Guiimartinho/gnss-bike-computer/hardware_gnssbike/04-pcb-e-caixa.md

# Placa e caixa

O contorno, a espessura, as camadas, onde cada bloco fica e onde nada pode
ficar. Fecha o que as [folhas do esquemático](01-esquematico.md) deixam em
aberto por natureza: um esquemático diz o que se liga a quê, e é o layout
que decide se a antena
enxerga o céu, se o harmônico da flash cai dentro de L1 e se a placa cabe na
caixa. As posições vêm da tabela de zonas de [`docs/14`](../docs/14-hardware-placa-nova.md#placa-de-circuito-impresso)
e, até 2026-09-26, do desenho do conceito da caixa (`tools/docs/case_drawing.py`,
retirado nesse dia: a proposta medida em [`caixa/`](caixa/README.md) o substitui).
Conta feita aqui vem marcada como **conta**; número de ficha ou de desenho
vem marcado como **ficha** ou **desenho**.

**Nesta página:** [O contorno](#o-contorno) · [Orçamento de área](#orçamento-de-área) · [Camadas](#camadas) · [Posicionamento](#posicionamento) · [Zonas proibidas](#zonas-proibidas) · [As duas antenas](#as-duas-antenas) · [Montagem](#montagem) · [O que só a bancada decide](#o-que-só-a-bancada-decide)

> [!WARNING]
> **Não existe placa física e nada foi fabricado nem medido.** Não há
> gerber, não há pilha de camadas de fabricante e ninguém encostou uma ponta
> de prova em nada. O que **passou a existir** desde 2026-09-23 é o projeto
> em KiCad, em [`cad/`](cad/): as 116 peças posicionadas, os planos de terra e
> parte das trilhas, com a verificação de regras do KiCad e o
> [dry-run das regras das fichas](09-dry-run-da-pcb.md).
>
> Esta página continua sendo **a planta**: os retângulos de zona daqui são o
> que o layout deve respeitar, e onde a placa de `cad/` diverge deles, a
> divergência está escrita e medida. Quando os dois discordarem, quem manda
> é o número medido no arquivo, não o retângulo desta tabela.

> [!CAUTION]
> **A placa é 34 × 90 mm desde 2026-09-24 e 34 × 95 desde 2026-09-26 (as
> três teclas espalhadas na largura do display, no passo de 13,4 mm, só
> passam pela área da antena do módulo de rádio com ele 5 mm mais baixo), e
> as tabelas de orçamento de área, de sobreposições e de posicionamento
> abaixo ainda são as de 55 × 97.** Elas
> precisam ser refeitas a partir dos retângulos novos, que estão em
> [`cad/make_dxf.py`](cad/make_dxf.py) (`ZONES`) e agora são **derivados de
> `W` e `H`**, não escritos um a um. Enquanto isso, quando esta página e o CAD
> discordarem, **quem vale é o CAD**.
>
> Uma tentativa anterior de 50 × 86 mm partia da largura do display e da
> altura da caixa. Estava errada pela raiz: **a placa não se mede pela
> caixa.** O tamanho de agora sai das regras das fichas, e a conta está em
> [De onde saem os 34 × 90](#de-onde-saem-os-34--90).
>
> A caixa do conceito continuava sendo a de 62 × 104 (o desenho dela foi
> retirado em 2026-09-26; a proposta medida, em [`caixa/`](caixa/README.md),
> tem 62 × 106 × 17), e **isso não é pendência da placa**: a caixa
> tem o tamanho que o display, a bateria e a mão pedem, e a placa encolher não
> muda nenhum dos três.

## O contorno

> [!IMPORTANT]
> **A placa não é dimensionada pela caixa, e a caixa não é dimensionada pela
> placa.** As duas são independentes: o tamanho da placa sai do **circuito**
> — peças, roteamento e as distâncias que as fichas impõem — e o da caixa sai
> do display, da bateria e da ergonomia. Uma placa menor não encolhe a caixa;
> ela apenas ocupa menos espaço dentro dela. Esta página já derivou uma da
> outra e estava errada.

| Item | Medida | Origem |
|---|---|---|
| PCB | **34 × 95 mm**, espessura de 0,8 mm | derivado das regras em [`cad/make_dxf.py`](cad/make_dxf.py) (`W`, `H`); os 5 mm além dos 90 de 2026-09-24 são das teclas no passo de 13,4 (abaixo) |
| Raio de canto da placa | **3 mm no desenho, 4 mm em [14](../docs/14-hardware-placa-nova.md#placa-de-circuito-impresso)** | as duas fontes discordam, ver abaixo |
| Caixa | conceito: 62 × 104 × 19 mm, mais 3 mm do engate de quarto de volta; proposta de 2026-09-26: **62 × 106 × 17** ([abaixo](#a-placa-de-hoje-dentro-da-caixa-do-conceito)) | o desenho do conceito (`tools/docs/case_drawing.py`, retirado em 2026-09-26); [`caixa/make_caixa.py`](caixa/make_caixa.py) (`W_C, H_C, T_C`) |
| Raio de canto da caixa | 7 mm | idem (`R`) |
| Placa da V3, para comparar | 52,35 × 77,47 mm | [13](../docs/13-placa-nova.md#o-que-cabe-numa-caixa-pequena) |

### De onde saem os 34 × 90

Uma regra domina: a **7.2** da ficha do ME54BS13 pede **50 mm entre dois
módulos de rádio** na mesma placa, e esta tem dois — o próprio ME54BS13 e o
MAX-F10S. Com o módulo deitado num canto (contorno de 17,0 × 13,5) e o
receptor no oposto (10,4 × 10,6, abaixo dos 8 mm da zona da antena), os 50 mm
entre os dois contornos fixam o lado longo. Varrendo cada milímetro inteiro
que ainda cumpre a regra **e** ainda cabe a fila de três teclas na largura
(3 × 10,2 mm mais 0,8 de margem de cada lado):

| Contorno | Área | Módulos a |
|---|---|---|
| 32 × 89 | 2.848 mm² | 50,8 mm |
| 33 × 89 | 2.937 mm² | 50,9 mm |
| **34 × 90** | **3.060 mm²** | **51,9 mm** |
| 44 × 86 | 3.784 mm² | 50,2 mm, com as teclas ainda na borda de baixo |

Ficou **34 × 90**. Os 2 mm além dos 88 que a regra sozinha permitiria não são
folga: a 88 o receptor tinha de encostar na borda esquerda para alcançar os
50 mm, e aí os pinos de 1V8 dele, que saem desse lado, ficavam com 1,2 mm de
placa para pôr um capacitor de desacoplamento que a ficha quer a 2 mm.

São **3.060 mm² contra os 5.335 mm² dos 55 × 97 que estavam escritos à mão —
43 % menos placa** — e a ocupação dos contornos das peças sobe de 28 % para
48 %.

**E depois 34 × 95** (2026-09-26). O dono quis as três teclas espalhadas na
largura do display, exatamente sob as capas da caixa, e não juntas no canto
esquerdo: no passo de 13,4 mm, o maior que a margem de 0,8 mm da borda
deixa, a terceira chave fica em x = 30,4, dentro dos 5 mm que a ficha do
ME54BS13 (7.4) quer livres em volta da área da antena do módulo. A área
começa em y = H − 22: com H = 95 ela desce 5 mm junto com o módulo, e a fila
de teclas em y = 66 passa a 5,0 mm dela. São 3.230 mm² (`GNSSBIKE_H` em
`make_dxf.py` troca a altura).

> [!IMPORTANT]
> **O raio de canto da placa não bate entre as duas fontes.** O desenho do
> conceito traçava a placa com **3 mm** de raio — `xv.rect(3.5, 3.5, W - 7, H - 7, 3, …)`,
> linha 339 do `case_drawing.py` retirado em 2026-09-26; o número vive em
> `cad/make_dxf.RADIUS_DRAWING` —, e [14](../docs/14-hardware-placa-nova.md#placa-de-circuito-impresso)
> escreve "cantos com raio de 4 mm". Um milímetro num canto não muda nada
> elétrico, mas muda o contorno que vai para o fabricante e a folga contra
> a parede de 7 mm de raio da caixa. **Qual dos dois vale ainda não foi
> decidido**, e esta página não escolhe por ninguém: registra os dois.

**Sistema de coordenadas** desta página, o mesmo de [14](../docs/14-hardware-placa-nova.md#placa-de-circuito-impresso):
origem no canto de cima à esquerda da **placa**, vista pela frente, x para a
direita (0 a 34 mm) e y para baixo (0 a 90 mm). **Não há mais conversão para
as coordenadas da caixa**: com a placa dimensionada pelo circuito e a caixa
pelo que ela guarda, onde uma fica dentro da outra é decisão do arranjo
mecânico, que não existe.

> [!IMPORTANT]
> **A folga entre a placa e a caixa não bate com o texto de [14](../docs/14-hardware-placa-nova.md#placa-de-circuito-impresso).**
> Lá está escrito "paredes de cerca de 2 mm e folga de 0,5 mm", que somam
> 2,5 mm por lado e dariam uma placa de 57 × 99 mm. O desenho põe a placa
> com 3,5 mm de recuo, o que com parede de 2 mm deixa **1,5 mm de folga
> mecânica por lado**, não 0,5 mm (**conta**: 3,5 − 2,0). Um milímetro por
> lado é a diferença entre apertar e sobrar; **qual dos dois vale é decisão
> do projeto mecânico, que não existe.** Esta página segue o desenho, que é
> executável, e registra a divergência.

## Orçamento de área

A placa tem **5.335 mm²** (**conta**: 55 × 97). A pergunta é se o que
precisa entrar cabe, e a resposta tem duas partes: a área de planta que as
zonas consomem, e a área que fica com **restrição de altura** por causa do
display na frente e da bateria atrás.

### O que cada zona consome em planta

Áreas calculadas a partir dos retângulos de [14](../docs/14-hardware-placa-nova.md#placa-de-circuito-impresso).
Todas são **conta**, menos a linha marcada como **falta**, que não tem
retângulo em documento nenhum.

| Zona | Retângulo (x, y em mm) | Lados | Área (mm²) | % dos 5.335 |
|---|---|---|---|---|
| Antena GNSS (área livre) | 0–55, 0–8 | 55 × 8 | 440,0 | 8,2 % |
| GNSS (MAX-F10S e blindagem) | 20–35, 2–16 | 15 × 14 | 210,0 | 3,9 % |
| LED RGB | 50–53, 0–3 | 3 × 3 | 9,0 | 0,2 % |
| IMU e magnetômetro | 8–15, 20–23 | 7 × 3 | 21,0 | 0,4 % |
| FPC do display | 3,7–7,1, 29,5–39,5 | 3,4 × 10 | 34,0 | 0,6 % |
| Conector do filme de luz (Molex 5034800440) | **sem retângulo em [14](../docs/14-hardware-placa-nova.md#placa-de-circuito-impresso)** | — | **falta** | — |
| Buzzer | 10,5–21,5, 46,5–55,5 | 11 × 9 | 99,0 | 1,9 % |
| Energia (nPM1300, AEM10900, MAX17262, indutores, conectores) | 16–38, 67–90 | 22 × 23 | 506,0 | 9,5 % |
| Armazenamento (flash NOR) | 0–14, 67–83 | 14 × 16 | 224,0 | 4,2 % |
| Barômetro | 4,5–8, 83–86,5 | 3,5 × 3,5 | 12,3 | 0,2 % |
| ME54BS13 **mais a zona proibida da sua antena** | 37,2–54,2, 58,7–71,4 unido a 49,5–55, 54,6–75,4 | ver a conta abaixo | 270,6 | 5,1 % |
| Botões | 8–47, 88–95 | 39 × 7 | 273,0 | 5,1 % |
| USB-C | 23–32, 94–97 | 9 × 3 | 27,0 | 0,5 % |
| Luz ambiente (OPT3001) | 0,4–2,4, 88–90 | 2 × 2 | 4,0 | 0,1 % |
| **Soma bruta** | | | **2.129,9** | **39,9 %** |
| Sobreposições contadas duas vezes | | | −102,5 | −1,9 % |
| **Soma líquida** | | | **2.027,4** | **38,0 %** |

O módulo entra com a **zona proibida**, não só com o retângulo dele: é a
zona que proíbe cobre, e é ela que o layout tem de respeitar
([Zonas proibidas](#zonas-proibidas)). Ela vai da antena até a borda da
placa e sobra 4,4 mm para cima e para baixo do módulo, e por isso a área é
a **união** dos dois retângulos (**conta**):

```
módulo:         x 37,2 a 54,2, y 58,7 a 71,4 = 17,0 × 12,7 = 215,9 mm²
zona proibida:  x 49,5 a 55,0, y 54,6 a 75,4 =  5,5 × 20,8 = 114,4 mm²
comum aos dois: x 49,5 a 54,2, y 58,7 a 71,4 =  4,7 × 12,7 =  59,7 mm²
união = 215,9 + 114,4 − 59,7 = 270,6 mm²       (270,6 ÷ 5.335 = 5,1 %)
```

> [!NOTE]
> **Estes números são novos.** Até 2026-09-23 este documento contava o
> módulo como o **Fanstel BM20C**, de 10,0 × 16,2 mm, no canto de baixo à
> direita (x 45–55, y 71,5–87,7), com a zona proibida em x 40–55, y 82–91:
> união de **240,0 mm², 4,5 %**. O módulo montado é o **MinewSemi
> ME54BS13**, maior (16,5 × 12,0 × 2,4 mm) e deitado acima das teclas, e
> todas as contas desta seção foram refeitas a partir dos retângulos novos.

A soma bruta fecha (**conta**): 440,0 + 210,0 + 9,0 + 21,0 + 34,0 + 99,0 +
506,0 + 224,0 + 12,3 + 270,6 + 273,0 + 27,0 + 4,0 = **2.129,9 mm²**.

As três sobreposições (**conta**) são exatamente os três pontos que o
layout terá de resolver:

| Sobreposição | Retângulo comum | Área |
|---|---|---|
| GNSS dentro da área livre da antena | 20–35, 2–8 | 15 × 6 = 90 mm² |
| LED RGB dentro da área livre da antena | 50–53, 0–3 | 3 × 3 = 9 mm² |
| Zona do **ME54BS13** dentro da zona de energia | 37,2–38, 67–71,4 | 0,8 × 4,4 = **3,5 mm²** |

A terceira sai de cruzar a zona do módulo com a zona de energia
(**conta**):

```
zona de energia: x 16   a 38,0, y 67,0 a 90,0
zona do módulo:  x 37,2 a 54,2, y 58,7 a 71,4
em x: de max(37,2; 16) = 37,2 a min(54,2; 38,0) = 38,0, ou seja 0,8 mm
em y: de max(58,7; 67,0) = 67,0 a min(71,4; 90,0) = 71,4, ou seja 4,4 mm
área = 0,8 × 4,4 = 3,52 mm², 3,5 mm² arredondado
```

Total das sobreposições: 90 + 9 + 3,5 = **102,5 mm²**.

A terceira sobreposição **trocou de lugar com o módulo**. Com o BM20C no
canto de baixo à direita, quem invadia a zona proibida era a faixa dos
botões, em 21 mm². Com o ME54BS13 deitado acima das teclas, a faixa dos
botões (y 88 a 95) e a zona proibida (y 54,6 a 75,4) **não se tocam mais**;
em troca, o canto de baixo à esquerda do módulo entra na zona de energia.
Os 3,5 mm² são pouco em área e **muito em significado**: é um conversor
chaveado encostando no módulo de rádio
([A zona do ME54BS13](#a-zona-do-me54bs13-em-detalhe)).

**Sobram 3.307,6 mm², 62,0 % da placa** (**conta**: 5.335 − 2.027,4), para
os passivos espalhados, as vias, os furos M2, os pontos de teste, o
footprint Tag-Connect TC2030-NL, os dois pads do console (`uart20`, `TP201` e
`TP202` de [06](06-conectores-e-pontos-de-teste.md#pontos-de-teste)) e as trilhas. **Pela planta,
fecha com folga.**

> [!NOTE]
> Os 6 módulos solares de 23 × 8 mm **não consomem área de placa**: ficam na
> face inclinada da caixa e nos dois chanfros de 45°, virados para o sol,
> enquanto a placa fica dentro, atrás do display. São três orientações
> diferentes, e é isso que faz a colheita render com o guidão apontando para
> qualquer lado — uma placa plana só tem uma orientação, então **soldar os
> módulos na placa não é uma opção**.
>
> Eles chegam por **um conector de 4 vias em pé na borda esquerda, na face
> de trás**, o `J103` (na borda direita da frente até 2026-09-26, quando o
> dry run da caixa o mediu a 0,05 mm da tampa), que consome 10,5 mm dessa
> borda e 8 mm para dentro. Antes eram três pares de
> pads de mola, e a área deles era o número que faltava aqui; agora está
> medida e entra na soma. Ver [Como os painéis chegam à
> placa](#como-os-painéis-chegam-à-placa).
>
> A antena GNSS continua sendo um elemento fora da placa quando se escolhe o
> caminho do `J302` (u.FL); pelo `JP301` também dá para montar a antena de
> chip soldada na borda de cima. **A área dos contatos da antena continua
> sem dimensionar.**

> [!IMPORTANT]
> **O conector do filme de luz não tem zona nem área.**
> [14](../docs/14-hardware-placa-nova.md#placa-de-circuito-impresso) manda
> pôr o Molex 5034800440, de 4 vias e passo de 0,5 mm, "ao lado" do FPC do
> display na borda esquerda, mas a tabela de zonas de lá **não lhe dá
> retângulo**, e a ficha dele não está resumida em nenhum documento deste
> repositório: não há como calcular a área aqui sem inventar uma medida.
> Ele só existe na montagem com a Sharp
> ([05](05-materiais.md#folha-4--display)), o que não o torna opcional no
> layout, porque a placa tem de aceitar as duas montagens. **É um número
> que falta**, e a soma acima está subestimada por ele.

### As duas sombras: display e bateria

O display fica sobre a face da frente e a bateria, sob a face de trás. Não
competem por área de planta, mas **limitam a altura** das peças embaixo
delas: até 3,0 mm sob o display (2,6 até 2026-09-26: o receptor MAX-F10S
tem 2,7 no máximo, e a caixa desceu a placa 0,4 mm em vez de tirar o
receptor de junto da antena) e até 1,2 mm sob a bateria
([14](../docs/14-hardware-placa-nova.md#placa-de-circuito-impresso)).

> [!IMPORTANT]
> **A posição do display e da célula sobre esta placa é uma PROPOSTA de
> 2026-09-26, não uma decisão.** A caixa desenhada de manhã (o conceito
> de `tools/docs/case_drawing.py`, retirado à tarde) era a da
> placa antiga, de 55 × 97, e nenhum arquivo dizia onde as duas peças caem
> sobre a placa de 34 × 90 — a tabela abaixo, até essa data, ainda trazia
> retângulos de 47 mm de largura numa placa de 34. Sem os retângulos a
> regra `ME2` do dry-run passava **sem medir peça nenhuma**; agora eles
> estão em `cad/make_dxf.py` (`SOMBRA_DISPLAY_JDI_MAX_3-0MM` e
> `SOMBRA_BATERIA_MAX_1-2MM`), a regra mede, e o que ela mede está abaixo.
> A caixa de [`caixa/make_caixa.py`](caixa/make_caixa.py) lê os mesmos
> retângulos (`make_dxf.DISPLAY_Y1`), e o dry run dela
> ([`caixa/dry_run_caixa.py`](caixa/dry_run_caixa.py)) mede a pilha inteira.

O que fixa cada retângulo, na placa de 34 × 95:

- **O display** LPM027M128C tem 40,08 × 61,8 mm: é **mais largo que a
  placa**, logo cobre a largura inteira. Em y, ele tem de acabar **acima
  das teclas**, que ficam em y = 66 com corpo de 3,5 mm (uma tecla debaixo
  do vidro não se aperta) — e acima do **furo da capa** de cada tecla na
  tampa, de 5,6 mm, que desce até y = 63,2: fim em **62,9**, começo 61,8
  acima, em **1,1**. Era 64,5 até o dry run da caixa de 2026-09-26, que
  mediu o furo entrando 1,3 mm no vidro colado; as teclas não podem descer
  (o SWD, o conector da célula e o USB-C ocupam y 67,75 a 85,44 até 0,4
  mm), e o dono quer as capas exatamente sobre as chaves.
- **A célula** de 36 × 60 × 7 também cobre a largura. A bolsa é metal, e
  metal não pode ficar atrás da antena GNSS (y até 9,88) nem no canto da
  área da antena do módulo (x ≥ 29,3, y ≥ 68,0; ficha do ME54BS13, 7.4).
  Entre as duas antenas há **58,1 mm**, e a célula tem **60**: começando
  logo abaixo da antena GNSS, em **9,9**, ela acaba em **69,9**, 1,9 mm
  dentro do canto da antena do módulo.

| Sombra | Retângulo (coordenadas da placa) | Área (mm²) | % dos 3.230 | Altura permitida |
|---|---|---|---|---|
| Display JDI LPM027M128C (contorno 40,08 × 61,8) | 0–34, 1,1–62,9 | 2.101,2 | 65,1 % | 3,0 mm |
| Bateria LiPo (36 × 60), na face de trás | 0–34, 9,9–69,9 | 2.040,0 | 63,2 % | 1,2 mm |

Contas de conferência (**conta**; a placa tem 34 × 95 = 3.230 mm²):

```
interseção das duas sombras = 34 mm × (62,9 − 9,9) = 34 × 53,0 = 1.802,0 mm²  (55,8 %)
união = 2.101,2 + 2.040,0 − 1.802,0 = 2.339,2 mm²  (72,4 %)
área sem restrição de altura dos dois lados = 3.230 − 2.339,2 = 890,8 mm²  (27,6 %)
```

**56 % da placa tem teto de 3,0 mm na frente e de 1,2 mm atrás ao mesmo
tempo**, e pouco mais de um quarto está livre das duas — a faixa de cima (a
antena GNSS e o receptor) e a de baixo (USB-C, módulo de rádio e teclas). O
dry-run de 2026-09-26 mediu as peças contra esses tetos (`ME2`), com as
alturas das fichas, e **cinco não cabiam**; no mesmo dia, com a caixa
desenhada e medida, todas saíram da sombra ou o teto subiu:

| Peça | Altura | Onde estava | Teto | O que foi feito |
|---|---|---|---|---|
| `J102`, conector da célula | 4,25 mm (GH) | face de trás, (4,0; 62,0) | 1,2 mm | virou o **JST SH** de 2,9 mm, **na frente**, em pé em (13,5; 80,4): fora das duas sombras, sob os 4,2 mm que a tampa deixa; perde a trava positiva ([06](06-conectores-e-pontos-de-teste.md#j102--bateria)) |
| `LS601`, buzzer | 3,00 mm | face de trás, zona `ZONA_BUZZER` (y 62 a 73) | 1,2 mm | face de trás em (18,0; 76,2), y ≥ 69,95, fora da célula; os furos de som ficam no fundo da caixa |
| `U502`, BMP585 | 1,86 mm | face de trás, no respiro (y 67 a 71) | 1,2 mm | face de trás em (9,7; 82,5), entre o `J103` e o buzzer, acima das pernas do USB-C; o respiro da caixa segue a peça |
| `J103`, conector do painel | 3,75 mm | frente, (29,0; 32,0) | 2,6 mm | **face de trás**, em pé na borda esquerda, (4,9; 75,2) a 270°: fora da célula, com 8 mm de ar até o fundo da caixa; o chicote sai para a parede e sobe pela lateral da placa |
| `U301`, MAX-F10S | 2,70 mm | frente, sob a antena (y 10,5 a 22) | 2,6 mm | **o teto subiu para 3,0 mm**: a caixa desceu a placa 0,4 mm (`make_caixa.DISPLAY_VAO`) e a célula acabou a 0,3 mm do fundo |

E dois conflitos que não são de altura, desenhados em `zonas.dxf`
(`CONFLITOS` em `cad/make_dxf.py`) para ninguém esquecer:

- **o display cobre 8,8 mm da área da antena GNSS** (y de 1,1 a 9,88;
  eram 7,2 com o display acabando em 64,5): a ficha da Unictron não diz o
  que um vidro com ITO a poucos milímetros faz ao ganho, e a regra `RF9`
  do dry-run também reclama do display a 11,8 mm da área da antena do
  módulo, onde a ficha do ME54BS13 pede 25;
- **a célula entra 1,9 mm no canto da área da antena do módulo.** As
  saídas são uma célula de até 58 mm, ou não mexer nas antenas e aceitar
  o canto — decisão do dono, com medição de S21 na bancada.

O inventário de peças altas fora dessas cinco é curto: o **ME54BS13
(2,4 mm)**, na frente sob o display, com 0,2 mm de folga; os dois indutores
dos bucks em 0805, o `L103` do ADP5091, o conector USB-C e os soquetes FPC,
na faixa de baixo ou na borda, fora da sombra da célula.

> [!CAUTION]
> **O ME54BS13 vai na face da frente, e não há alternativa.** Atrás, o
> teto sob a célula é 1,2 mm e o módulo tem 2,4; na frente, na placa de
> 95 mm, ele fica **abaixo do display** (y 76,25 a 88,75), sob os 4,2 mm
> que a tampa deixa fora dele — e mesmo sob o display, com o teto de 3,0,
> sobrariam 0,6 mm. As alturas saem de ficha, não de peça medida. Não
> medido: a altura real do módulo e a do pack de bateria comprado.

### A ordem de montagem

Manual de montagem: as peças em escala e os oito passos, do chicote solar ao fechamento do aparelho

O manual sai de [`tools/docs/assembly_manual.py`](../tools/docs/assembly_manual.py)
e **todas as peças estão em escala**: a caixa de 62 × 106, a placa de 34 × 95,
o display de 40,08 × 61,8, a célula de 36 × 60, os módulos de 23 × 8 e cada
conector na posição que ocupa no arquivo da placa. As posições estão
**escritas no script** (`CONEC`, `TECLAS`, `FUROS`), copiadas do
`make_pcb.py`, e não lidas do arquivo: quando um conector se move no CAD,
alguém tem de mover a folha junto (feito em 2026-09-26).

A ordem não é arbitrária. Três coisas a decidem:

1. **O chicote solar vem primeiro** porque é o único trabalho de bancada
   demorado, e porque a polaridade dele se confere com os módulos no sol,
   fora da caixa.
2. **Os dois cabos do display entram com a placa ainda fora da cavidade.**
   O `J401` e o `J402` ficam na borda esquerda, a 5,1 mm dela, e a trava de
   um FPC de 0,5 mm não se alcança com a placa assentada.
3. **O chicote solar liga antes de a placa entrar**, porque o `J103` fica no
   **verso** (em pé na borda esquerda, com a boca para a parede). A bateria
   liga **depois**: o `J102` fica na **frente**, e o cabo da célula, que está
   debaixo da placa, dá a volta pela lateral esquerda até ele.

Três coisas que o manual diz que **não estão definidas em arquivo nenhum**:
como o módulo solar é preso à parede, como o painel é preso à frente e onde
ficam os parafusos da caixa.

### Como os painéis chegam à placa

Os seis módulos ficam na caixa e a placa fica dentro dela, então entre os dois
há um chicote. Esta seção diz qual, com que configuração e por quê. Decidido
em 2026-09-24; **nada montado nem medido**.

**A configuração é obrigatória: os seis em paralelo.** Cada KXOB25-05X3F já
tem 3 células em série e abre em 2,07 V, e o MPPT do colhedor rastreia de
0,12 a 2,73 V. Dois módulos em série dariam 4,14 V — 1,4 V acima do teto.

| Arranjo | Em aberto | A 1 sol | Cabe no colhedor? |
|---|---|---|---|
| **6 em paralelo** | **2,07 V** | 6 × 18,4 = **110 mA** | **sim** |
| 2 em série, 3 ramos | 4,14 V | 55 mA | não, passa 1,4 V do teto |
| 3 em série, 2 ramos | 6,21 V | 37 mA | não |

O ponto de máxima potência fica em 80 % de 2,07 = **1,66 V**. Ao meio-dia o
arranjo real entrega cerca de **88 mA**, porque as três faces não pegam sol de
frente ao mesmo tempo; o pior caso teórico, sol normal aos seis, dá 110 mA.
O limite de entrada com o indutor de 4,7 µH fica entre 95 e 123 mA, então
**no pior caso o colhedor pode limitar** — ele sai do ponto de máxima
potência e a placa colhe um pouco menos. Não quebra nada. Está na bancada.

**O conector é o `J103`, JST ZH de 1,5 mm, 4 vias, SMD lateral, com trava.**
Três vias para os grupos (frente, chanfro esquerdo, chanfro direito) e uma
para o terra comum, que os três dividem.

```mermaid
flowchart LR
    F["face inclinada<br/>PV101 · PV102"] --> J["J103<br/>ZH 1,5 mm, 4 vias"]
    E["chanfro esquerdo<br/>PV103 · PV104"] --> J
    D["chanfro direito<br/>PV105 · PV106"] --> J
    J --> R["R113 · R114 · R115<br/>0 Ω, um por grupo"]
    R --> C["C115<br/>22 µF"]
    C --> L["L103"]
    L --> U["colhedor"]
```

Quatro decisões dentro dessa, cada uma com o seu motivo:

1. **Conector, não pad de mola.** Até 2026-09-24 eram três pares de pads de
   2 × 2 mm que uma mola da caixa pressionaria. Três razões derrubaram isso:
   a JLCPCB **não monta mola**; uma bicicleta vibra, e um contato pressionado
   que abre e fecha na entrada de um conversor chaveado é um transitório
   sujo; e o conector come **10,5 mm** de borda (a esquerda, no verso, desde
   2026-09-26) contra os 16 mm dos três pares.
2. **Família diferente da bateria, de propósito.** A célula entra num **JST
   SH de 1,0 mm** de 6 vias (era o GH de 1,25 até 2026-09-26, e a razão da
   família diferente vale igual). Se o painel usasse a mesma família, um dia
   alguém pluga a bateria de 4,2 V na entrada do colhedor, que aguenta
   **2,73 V**. Com **ZH de 1,5 mm** os dois não entram um no outro, e os
   corpos têm tamanhos visivelmente diferentes. É proteção mecânica, de
   graça. (O JST SH de 1,0 mm, que seria a escolha óbvia por ser menor, saiu
   de linha: 3 peças na JLCPCB.)
3. **Três 0 Ω, um por grupo.** Sem eles os seis módulos em paralelo dão um
   número só e nunca se sabe qual face está rendendo. Com eles, abre-se um e
   mede-se o grupo sozinho no sol. É o mesmo raciocínio do `JP301` da antena.
4. **Quatro vias, não seis.** Os três grupos dividem o mesmo terra: três
   pinos de GND seriam o mesmo nó repetido. Além disso o corpo de 6 vias tem
   13,5 mm e fazia sombra no sensor de luz ambiente, que pede o dobro da
   própria altura livre em volta (regra `OP1` do
   [dry-run](09-dry-run-da-pcb.md)).

**Regra de layout que sai disso:** o `C115` de 22 µF fica **entre o conector
e o `L103`**, encostado no conector. O colhedor é um boost com o indutor em
série na entrada, então quem segura a ondulação do chaveamento é o `C115`; se
ele estiver do lado errado, o cabo que vem da caixa vira a antena de um
conversor passando perto da antena do GNSS.

**E um grampo, o `D105`.** O conector certo impede o engano de plugar a
bateria no painel; o grampo impede o prejuízo quando o engano vier de outro
lugar — fio invertido no crimp, painel trocado, fonte de bancada. **A peça
ainda não foi escolhida**: falta conferir a corrente de fuga a 2,1 V, que
entra direto no orçamento solar, e o máximo absoluto do pino de entrada na
ficha do colhedor.

### O aperto que não fecha: a antena GNSS

Entre a borda de cima da placa e o contorno do display sobram **5,1 mm**
(**conta**: 8,6 − 3,5, do desenho), e a zona da antena de
[14](../docs/14-hardware-placa-nova.md#placa-de-circuito-impresso) reserva
8 mm. A peça do protótipo, a **TE L000670, mede 14 × 10,75 × 1 mm**
([15](../docs/15-avaliacao-componentes.md#antena-gnss)).

```
na orientação mais favorável, a peça pede 10,75 mm de profundidade
contra a zona reservada de 8 mm    faltam 10,75 − 8,00 = 2,75 mm
contra a faixa livre de 5,1 mm     faltam 10,75 − 5,10 = 5,65 mm
```

Os 2,75 mm que faltam contra a zona já são um problema; os 5,65 mm contra a
faixa livre são pior, porque o que sobra do outro lado **fica sob o
display**, e [13](../docs/13-placa-nova.md#o-que-cabe-numa-caixa-pequena) é
explícito: "Debaixo do LCD não", porque o LCD deforma o diagrama da antena e
emite ruído de banda larga. Três saídas, nenhuma decidida:

1. **Antena na parede da caixa**, com contatos de mola (a opção A de
   [13](../docs/13-placa-nova.md#o-que-cabe-numa-caixa-pequena), que é o que
   Garmin, COROS e Wahoo fazem): a peça sai da placa e o aperto some. Pede
   fornecedor de antena sob medida, que ainda não existe
   ([14](../docs/14-hardware-placa-nova.md#pendências)).
2. **Display mais para baixo**, roubando dos botões: cada milímetro de
   descida é um milímetro a menos na faixa de baixo, que já tem os botões
   (y 88 a 95) e o USB-C (y 94 a 97).
3. **Caixa mais alta**, que é o que [13](../docs/13-placa-nova.md#o-que-cabe-numa-caixa-pequena)
   já previa como consequência da antena.

Com a Sharp, que é 1,0 mm mais alta que o JDI (**conta**: 62,8 − 61,8), a
faixa livre cai para cerca de **4,6 mm** se o centro for mantido — o aperto
piora.

## Camadas

**4 camadas, 0,8 mm**, com controle de impedância, como já registrado em
[14](../docs/14-hardware-placa-nova.md#placa-de-circuito-impresso).

```mermaid
flowchart TB
    L1["L1 · frente<br/>peças da face do display, sinais rápidos e curtos,<br/>rede em π da antena GNSS, linha de 50 Ω até o elemento"]
    L2["L2 · GND sólido<br/>referência de L1 e de L3, e o plano que a antena usa para irradiar"]
    L3["L3 · alimentação e sinais lentos<br/>3V0 e 1V8 em áreas; display e USB entre L2 e o cobre de L4"]
    L4["L4 · trás<br/>peças da face da bateria, sinais, cobre de retorno"]
    L1 --- L2 --- L3 --- L4
```

### Por que 4 e não 2

| Motivo | O número por trás |
|---|---|
| **O plano de terra é a antena.** Numa antena linear quem irradia é o plano; [13](../docs/13-placa-nova.md#o-que-cabe-numa-caixa-pequena) traz o mesmo chip com 43,4 dB-Hz num plano de 80 × 40 mm e **34,7 dB-Hz** num de 24 × 15 mm | 8,7 dB-Hz de diferença, ficha |
| Em 2 camadas o plano da face de baixo é rasgado pelo roteamento: os 31 sinais de [03](03-netlist.md#nós-do-mcu) mais os 12 nós de alimentação teriam de passar por ali | 31 e 12, do netlist |
| **Camada interna para display e USB.** [13](../docs/13-placa-nova.md#regras-de-projeto) e [14](../docs/14-hardware-placa-nova.md#regras-de-layout) pedem essas linhas entre planos de terra; em 2 camadas não existe camada interna | — |
| **Referência contínua para as duas impedâncias controladas:** 50 Ω do `RF_IN` do MAX-F10S até o elemento e 90 Ω diferencial do par `USB_DM`/`USB_DP` | [03](03-netlist.md#dedicados-do-módulo) |
| **Área.** 46,4 % da frente está sob o display e 40,5 % da traseira sob a bateria: sobram poucas regiões boas para peças, e o roteamento tem de descer | **conta**, acima |
| [13](../docs/13-placa-nova.md#regras-de-projeto), regra 6, já manda "placa de 4 camadas, com planos sólidos e moldura de terra com vias" | — |

A linha de 50 Ω fica curta por construção: a zona do GNSS começa em y 2 e a
zona da antena vai de y 0 a 8, de modo que o percurso é de **poucos
milímetros**. O comprimento exato não existe até o footprint do MAX estar
posicionado e o pino `RF_IN` ter coordenada.

### 0,8 mm, e a tensão que isso cria

A espessura de 0,8 mm **não é escolha de layout**: o desenho do receptáculo
USB-C Molex 2036150003 a recomenda, e a especificação do projeto já desceu
de 1,0 para 0,8 mm por causa dele ([15](../docs/15-avaliacao-componentes.md#usb-c-e-proteção)).
Com 4 camadas dentro de 0,8 mm, os dielétricos ficam finos:

```
cobre: 4 folhas de 35 µm (1 oz) = 0,14 mm
dielétrico disponível = 0,80 − 0,14 = 0,66 mm, repartido em 3 vãos
repartição uniforme = 0,66 ÷ 3 = 0,22 mm por vão
```

E aqui a conta para. A largura de uma trilha de 50 Ω em L1 depende do vão
**L1–L2**, e as duas repartições plausíveis de 0,66 mm são muito diferentes:
uma pilha uniforme dá 0,22 mm de vão, e uma pilha com prepreg fino por fora
e núcleo grosso no meio dá algo como 0,10 mm fora e 0,46 mm no meio. **A
largura de 50 Ω e a de 90 Ω diferencial não existem como número até o
fabricante mandar a pilha dele**, e [02](02-calculos.md#o-que-não-foi-calculado)
já registra as duas como não calculadas.

> [!IMPORTANT]
> **Confirmar com o fabricante, antes do layout:** que ele fabrica 4 camadas
> em 0,8 mm acabados, com que repartição de dielétrico, com que cobre
> (35 µm ou 18 µm) e com que largura de trilha para 50 Ω e 90 Ω
> diferencial nessa pilha. Sem esses quatro números o roteamento de RF e de
> USB não começa. **Nenhum fabricante foi consultado.**

Uma placa de 0,8 mm também **empena mais** que uma de 1,6 mm no forno e sob
o calor do carregador, que dissipa até 1,50 W a poucos milímetros da célula
([02](02-calculos.md#calor-do-carregador)). Não medido.

## Posicionamento

Os retângulos abaixo são os de [14](../docs/14-hardware-placa-nova.md#placa-de-circuito-impresso),
nas coordenadas da placa, e batem com o desenho da caixa — **com uma
exceção: o módulo de rádio**, cujo retângulo mudou com a troca do BM20C
pelo ME54BS13 e não é mais o de lá. As três faixas de y correspondem à
borda de cima (antena e GNSS), ao meio (sob o display, com a bateria atrás)
e à base (energia, botões e USB); o módulo fica **a cavalo entre as duas
últimas**, de y 58,7 a 71,4.

```mermaid
flowchart TB
    subgraph PCB["PCB 34 × 90 mm · vista pela frente · origem no canto de cima à esquerda"]
        direction TB
        subgraph Y1["y 0 a 20 · borda de cima"]
            direction LR
            A1["área livre da antena GNSS<br/>x 0 a 55 · y 0 a 8<br/>sem cobre em nenhuma camada"]
            A2["MAX-F10S sob blindagem<br/>x 20 a 35 · y 2 a 16<br/>frente, até 2,6 mm"]
            A3["LED RGB<br/>x 50 a 53 · y 0 a 3"]
        end
        subgraph Y2["y 20 a 67 · meio, sob o display"]
            direction LR
            B1["FPC do display, 10 vias<br/>x 3,7 a 7,1 · y 29,5 a 39,5<br/>sai pela esquerda"]
            B2["BMI270 e MMC5633NJL<br/>x 8 a 15 · y 20 a 23"]
            B3["buzzer piezo<br/>x 10,5 a 21,5 · y 46,5 a 55,5"]
            B4["LiPo 36 × 60 × 7 mm, atrás<br/>x 9,5 a 45,5 · y 22,5 a 82,5<br/>teto de 1,2 mm embaixo"]
            B5["ME54BS13 16,5 × 12,0 × 2,4 mm<br/>x 37,2 a 54,2 · y 58,7 a 71,4<br/>deitado, na frente; antena nos últimos<br/>4,46 mm, virada para a borda direita"]
        end
        subgraph Y3["y 67 a 97 · base"]
            direction LR
            C1["flash MX25R6435F<br/>x 0 a 14 · y 67 a 83"]
            C2["energia: nPM1300, MAX17262,<br/>AEM10900, indutores<br/>x 16 a 38 · y 67 a 90"]
            C4["BMP585 no respiro, atrás<br/>x 4,5 a 8 · y 83 a 86,5"]
            C5["3 teclas Omron B3S-1002P<br/>6 × 6 × 4,3 mm<br/>x 8 a 47 · y 88 a 95"]
            C6["USB-C IPX8<br/>x 23 a 32 · y 94 a 97"]
            C7["OPT3001<br/>x 0,4 a 2,4 · y 88 a 90"]
        end
    end
    ANT["elemento linear L1 e L5<br/>na parede de cima da caixa,<br/>fora da placa, por contatos de mola"] -.->|"linha de 50 Ω, poucos mm"| A2
    Y1 --> Y2 --> Y3
    PV["6 módulos solares 23 × 8 mm<br/>2 na face inclinada e 2 em cada chanfro,<br/>na caixa, fora da placa"] -.->|"3 grupos em paralelo,<br/>J103 de 4 vias"| C2
```

O que o arranjo garante, e por quê:

| Escolha | Razão |
|---|---|
| GNSS e sua antena na borda de **cima**, rádio na borda **direita**, acima das teclas | é a borda de cima que aponta para o céu com o aparelho inclinado no guidão ([13](../docs/13-placa-nova.md#antena-gnss-dentro-da-caixa)). O rádio ficava no canto de baixo à direita, em ponta oposta; o ME54BS13, maior e deitado, subiu, e a separação entre as duas antenas caiu de 87,2 para 67,2 mm ([As duas antenas](#as-duas-antenas)) |
| FPC do display pela **esquerda** | longe das duas antenas ([14](../docs/14-hardware-placa-nova.md#regras-de-layout)); as 10 vias estão na [folha 4](01-esquematico.md#folha-4--display) |
| Energia (bucks e boost) na base, na diagonal da antena GNSS | laços de chaveamento longe da antena ([13](../docs/13-placa-nova.md#regras-de-projeto), regra 5) |
| BMP585 na face de trás, junto do respiro, em y 83 a 86,5 | fora da sombra da bateria, que termina em y 82,5 (**conta**) |
| OPT3001 embaixo à esquerda | sob a janela de luz ambiente, longe das antenas |
| USB-C no meio da borda de baixo | o anel veda contra a parede, sem tampa |
| `J202`, o conector SWD de 10 vias, em (11,3; 72,2), abaixo das teclas e à esquerda do corredor do par USB | tem 5 mm de altura, então não cabe sob o display (teto 2,6) nem sob a célula, e precisa da face da frente, que é a que se abre; deixado como `JUNTO` do módulo o colocador o pôs em (17,5; 60,5), debaixo do display. A posição é explícita em `make_pcb.py` (2026-09-26) |

## Zonas proibidas

Quatro zonas, com quatro proibições diferentes. **Nenhuma foi verificada em
cobre.**

| Zona | Retângulo (placa) | Área | O que é proibido | Origem |
|---|---|---|---|---|
| **Antena do ME54BS13** | x 49,5–55, y 54,6–75,4 | 114,4 mm² (**conta**: 5,5 × 20,8) | cobre, trilha, plano e via **em todas as camadas**; nenhum componente | ficha MinewSemi ME54BS13 V1.0.0, 7.2 |
| **Antena GNSS** | x 0–55, y 0–8 | 440 mm² (**conta**) | cobre em todas as camadas sob a antena; nada metálico mais alto que 3 mm num raio de 10 mm; a caixa a 3 a 5 mm | [13](../docs/13-placa-nova.md#regras-de-projeto), [14](../docs/14-hardware-placa-nova.md#placa-de-circuito-impresso) |
| **Sombra da bateria** | x 9,5–45,5, y 22,5–82,5 | 2.160 mm² (**conta**) | peças acima de 1,2 mm na face de trás; e a bolsa metálica não pode ficar entre a antena GNSS e o céu | [13](../docs/13-placa-nova.md#regras-de-projeto), [14](../docs/14-hardware-placa-nova.md#placa-de-circuito-impresso) |
| **Conector USB-C** | x 23–32, y 94–97 | 27 mm² (**conta**) | o anel de vedação passa da borda da placa; nada entre o corpo do conector e a parede | desenho Molex 2036150003 |

### A zona do ME54BS13, em detalhe

O módulo tem **16,5 × 12,0 × 2,4 mm** e a antena dele é uma **antena de
PCB** numa das pontas de 12 mm: os últimos **4,46 mm** do comprimento. A
ficha MinewSemi ME54BS13 V1.0.0, na seção 7.2, pede que essa ponta fique
**virada para a borda da placa** e que em volta dela fiquem **4 mm livres**,
sem cobre, trilha, plano ou via em camada nenhuma. Ele fica **deitado**,
acima das teclas, com a antena na borda **direita**, na **face da frente**.

```
zona do módulo:  x 37,2  a 54,2,  y 58,7 a 71,4  (o corpo mais a folga de
                                                  posicionamento)
corpo:           x 37,45 a 53,95, y 59,0 a 71,0  (16,5 × 12,0, centro em
                                                  45,7; 65,0)
área da antena:  x 49,49 a 53,95, y 59,0 a 71,0  (os últimos 4,46 mm)
zona proibida:   x 49,5  a 55,0,  y 54,6 a 75,4  (a área da antena, mais os
                                                  4 mm livres, até a borda)
```

**A troca de módulo desfez um conflito e criou outro.** O que sumiu: com o
BM20C no canto de baixo à direita, a faixa dos botões invadia 21 mm² da
zona proibida. Com o ME54BS13 deitado acima das teclas, a faixa dos botões
(y 88 a 95) e a zona proibida (y 54,6 a 75,4) **não se tocam**, e os quatro
parafusos que o desenho da caixa ainda mostra — em (3,0; 9,0), (52,0; 9,0),
(3,0; 88,0) e (52,0; 88,0) na placa — também ficam todos fora dela.

O que apareceu no lugar é a **regra de isolação da seção 7.2** da mesma
ficha, `Interference Isolation Rule`, que não é uma distância só: é uma
tabela de quatro linhas, medida **do módulo** até a fonte de interferência.

| Fonte de interferência | Distância mínima recomendada | Existe nesta placa? |
|---|---|---|
| Fonte chaveada DC-DC, indutor de potência, transformador | **20 mm** | sim: `U101`, `U103`, `L101`, `L102`, `L103` |
| USB 3.0 / HDMI 2.0 / DDR / SDIO de alta velocidade | 20 mm | não: o USB aqui é 2.0 full speed |
| Clock de alta frequência de MCU, PHY Ethernet | 15 mm | não: o único clock rápido está dentro do próprio módulo |
| **Display, câmera, cabo FPC com fiação** | **25 mm** | sim: o display e os dois cabos planos |

O retângulo da zona de energia desta página termina em x 38 e a antena começa
em x 49,5 (**conta**: 49,5 − 38 = **11,5 mm**) — mas o retângulo é planta, não
é peça. **Na placa montada em [`cad/`](cad/) a linha dos 20 mm é cumprida**: o
posicionador carrega a restrição (`LONGE_DO_MODULO` em `cad/make_pcb.py`) e
a regra `RF9` de [`cad/dry_run_pcb.py`](cad/dry_run_pcb.py) mede
([09](09-dry-run-da-pcb.md)). Sem a restrição, o `L103` fica a **6,8 mm**.

> [!IMPORTANT]
> **A linha dos 25 mm do display deixou de ser questão da placa e virou
> questão do arranjo mecânico.** Enquanto a placa tinha 55 × 97 mm, o display
> de 40,08 × 61,8 ficava por cima dela e a sua sombra chegava a **11,3 mm** do
> módulo, contra os 25 mm da tabela — sem posição na placa que resolvesse.
> Com a placa em **34 × 90**, o display é **mais largo do que ela**: ele não
> fica mais sobre a placa, e o que o `RF9` mede agora é o que de fato está na
> placa, os dois cabos planos — o pior deles, o `J402`, a **31,3 mm** do
> módulo, acima dos 25.
>
> Isso **não declara o problema resolvido**: declara que ele mudou de lugar.
> Quanto o display fica do módulo passa a depender de onde a caixa põe cada
> um, e nenhum documento fixa isso ainda. A saída que a própria ficha dá no
> mesmo parágrafo — *"Isolation using different PCB layers and shielding
> covers is recommended"* — continua valendo se a distância não sair.
> **A consequência no alcance só sai de bancada.**

A bolsa da bateria, atrás, termina em x 45,5, a **4 mm** da zona proibida
(**conta**: 49,5 − 45,5), e isso continua em aberto.

> [!WARNING]
> **Nenhum DRC pega a regra dos 20 mm.** Ela não proíbe cobre, proíbe
> **peça**, e o DRC de um CAD não conhece esse tipo de restrição. Quem a
> cumpre é quem posiciona. Por isso ela é uma restrição do posicionador e uma
> medida do dry-run, em vez de uma boa intenção: o `RF9` falha se alguém
> encostar de novo. O que ela custou foi empurrar o colhedor solar e o
> indutor dele para dentro da zona de energia, e custou **1,3 mm** ao
> desacoplamento do `U104`, que foi de 1,7 para **3,3 mm** contra um limite
> de 2 — a troca está registrada porque é troca, não é acidente. **A
> consequência elétrica continua não medida: só bancada diz se o alcance e o
> ruído ficaram onde se espera.**

> [!WARNING]
> **Esta página já afirmou que a regra dos 20 mm não existia.** Ela existe: é
> a 7.2, `Interference Isolation Rule`, e o que se leu antes foi a 7.3, que
> só traz o qualitativo *"do not place modules adjacent to strong
> interference sources"*. Enquanto a afirmação valeu, a restrição saiu do
> posicionador e um indutor de potência chegou a **6,8 mm** do módulo.
> Corrigido em 2026-09-24, lendo a ficha `ME54BS13-nRF54LM20A_Datasheet_K_EN
> v1.0.0` de novo, página 11.

**O que a ficha do ME54BS13 não responde e a do BM20C respondia:** a regra
dos **30 mm de metal externo** era da Fanstel. Se a MinewSemi tem
equivalente, ninguém leu; até lá, a bateria a 4 mm da zona proibida é um
risco **sem número**, e o alcance do rádio só sai de medida.

### A zona da antena GNSS, em detalhe

Além do cobre, três coisas não podem ficar entre a antena e o céu: a **bolsa
metálica da bateria**, os **parafusos** e o **painel solar**
([13](../docs/13-placa-nova.md#regras-de-projeto), regra 2). Na geometria
atual a bateria termina em y 22,5, a 14,5 mm da zona da antena (**conta**:
22,5 − 8), o que resolve a bateria. Os dois parafusos de cima estão em
(6,5; 12,5) e (55,5; 12,5) nas coordenadas da caixa, ou seja, (3,0; 9,0) e
(52,0; 9,0) na placa: **1 mm abaixo da zona**, com cabeça e ilha que
certamente entram nela. Os módulos solares mais altos são os dos chanfros
laterais, e começam em **y 21,5 na caixa**, ou **y 18 na placa**; a faceta
chanfrada que os recebe começa antes, em **y 17,5 na caixa**, ou **y 14 na
placa** (no desenho do conceito, retirado em 2026-09-26: o bisel
`rect(0.6, 17.5, 6.2, 55.0, …)` e os módulos `module(fv, x0, 21.5, 5.5, 23.0, True)`):

```
módulo mais alto:  y 21,5 − 3,5 = 18,0 na placa, a 18,0 − 8 = 10,0 mm da zona
faceta chanfrada:  y 17,5 − 3,5 = 14,0 na placa, a 14,0 − 8 =  6,0 mm da zona
```

Uma versão anterior desta página dizia "y 18 na caixa (y 14,5 na placa)":
os 18 já eram a coordenada da **placa**, e o recuo de 3,5 mm foi descontado
duas vezes. Nenhum dos três foi checado contra o raio de 10 mm que a regra
pede.

### A zona do conector USB-C

O conector é o Molex 2036150003 da [folha 1](01-esquematico.md#folha-1--energia).
O desenho da Molex dá: **placa de 0,8 mm**, furo de **9,54 × 3,76 mm** numa
parede de **pelo menos 1,2 mm**, e a **borda da placa 2,73 mm atrás da
frente do conector**. Com o recuo de 3,5 mm:

```
folga da borda da placa à face externa da caixa = 3,5 mm
a boca do conector fica 3,5 − 2,73 = 0,77 mm atrás da face externa
com parede de 1,2 mm, o conector entra 2,73 − (3,5 − 1,2) = 0,43 mm no furo
com parede de 2,0 mm, o conector entra 2,73 − (3,5 − 2,0) = 1,23 mm no furo
```

Fecha nos dois casos (**conta**), com o anel apertado contra a face interna
da parede. O que sobra em aberto é o **plugue**: ele precisa vencer 0,77 mm
de furo antes de alcançar a boca do conector, e um plugue de capa grossa
pode não entrar. **Nenhum cabo foi provado contra nenhuma caixa.**

## As duas antenas

Uma placa com **duas antenas ligadas a rádios que trabalham ao mesmo
tempo** é o risco de RF deste projeto, e já está registrado como pendência
em [10](../docs/10-status-do-port.md), na
[proposta](../docs/13-placa-nova.md#riscos), nas
[pendências de 14](../docs/14-hardware-placa-nova.md#pendências) e na
[bancada antes do layout de 15](../docs/15-avaliacao-componentes.md#bancada-antes-do-layout).
O que este documento acrescenta é a distância que a geometria dá.

| Antena | Onde | Frequência |
|---|---|---|
| 2,4 GHz (BLE e ANT+) | antena de PCB do ME54BS13, últimos 4,46 mm, x 49,49–53,95, y 59,0–71,0 | 2,40 a 2,48 GHz |
| GNSS L1 e L5 | elementos na parede de cima, fora da placa, x 2,5–25 (L1) e x 30–52,5 (L5), cerca de 2,2 mm à frente da borda de cima ([folha 3](01-esquematico.md#folha-3--gnss)) | 1.575,42 MHz e 1.176,45 MHz |

Distância entre a antena do rádio e o ponto mais próximo do elemento de L5
(**conta**, do centro (51,7; 65,0) ao ponto (52,5; −2,2)):

```
d = raiz de ((52,5 − 51,7)² + (65,0 + 2,2)²) = raiz de (0,64 + 4.515,84) = 67,2 mm
```

Cerca de **67 mm**. Em comprimentos de onda (**conta**, com
c = 3 × 10⁸ m/s):

| Banda | λ | Distância |
|---|---|---|
| 2,44 GHz | 123,0 mm | 0,55 λ |
| L1, 1.575,42 MHz | 190,4 mm | 0,35 λ |

> [!CAUTION]
> **A troca de módulo custou 20 mm de separação.** Com o BM20C no canto de
> baixo à direita a antena ficava em (50; 85) e a conta dava **87,2 mm,
> 0,71 λ** em 2,44 GHz: as duas antenas em pontas opostas da diagonal, que
> é o máximo que uma placa de 55 × 97 mm permite. Com o ME54BS13 deitado
> acima das teclas a antena subiu para y 65 e a distância caiu para
> **67,2 mm, 0,55 λ** (**conta**: 87,2 − 67,2 = 20,0 mm a menos). A
> geometria, que já era o ponto fraco, **piorou**, e o ensaio de S21
> deixou de ser conferência para virar o que decide se o arranjo serve.

> [!CAUTION]
> **Menos de um comprimento de onda não é muita separação.**
> [13](../docs/13-placa-nova.md#regras-de-projeto) dá a faixa esperada num
> aparelho pequeno: **isolação de 6 a 20 dB**, o que com os +8 dBm do
> nRF54LM20A põe **de −12 a +2 dBm na entrada do GNSS**. A defesa deste
> projeto é o MAX-F10S ter SAW, LNA e SAW **dentro do módulo** (a entrada
> aguenta 0 dBm, e a ficha não abre exceção fora da banda). **A isolação
> desta placa não existe como número: ninguém mediu o S21, porque não há
> placa.** O ensaio já está previsto: S21 em 2,44 GHz e C/N0 com o rádio
> transmitindo, antes de ligar o rádio na potência cheia
> ([15](../docs/15-avaliacao-componentes.md#bancada-antes-do-layout)).

### O harmônico de 8 MHz da flash

[13](../docs/13-placa-nova.md#regras-de-projeto) escolheu as frequências do
barramento de armazenamento **de propósito** para fugir de L1: 16 ou
21,33 MHz, "nunca a 8 ou 25 MHz", porque os harmônicos de 1, 2, 4, 8 e
25 MHz caem a menos de 0,6 MHz do centro de L1. Quando o cartão saiu e a
flash NOR entrou, o devicetree ficou com
[`spi-max-frequency = <8000000>`](../zephyr_app/boards/gnss/gnssbike/)
(`gnssbike_nrf54lm20a_cpuapp.dts:463`) — **8 MHz, um dos que a regra
mandava evitar**. A conta confirma:

```
1.575,42 ÷ 8 = 196,93, e o harmônico vizinho é 197 × 8 = 1.576,00 MHz
distância ao centro de L1 = 1.576,00 − 1.575,42 = 0,58 MHz
```

O barramento sai da flash (x 0 a 14, y 67 a 83) e vai ao MCU; a antena está
na borda de cima. **Risco a mitigar no layout**, nas três frentes que
[13](../docs/13-placa-nova.md#regras-de-projeto) e
[14](../docs/14-hardware-placa-nova.md#regras-de-layout) já indicam:

1. **Borda lenta:** **33 Ω** em série no `NOR_SCK` e nos dados, junto do
   pino do MCU, para tirar energia dos harmônicos altos. A conta de
   [02](02-calculos.md#resistor-de-série-no-spi-da-flash) mostra que 33 Ω
   custa cerca de 1 % do meio período a 8 MHz, longe de atrapalhar o
   relógio, e que 100 Ω também caberiam. **O valor final sai de medida**,
   com o espectro na banda (`UBX-MON-SPAN`) e a flash trabalhando: a
   capacitância real da trilha ainda não existe.
2. **Trilha curta:** a flash está a cerca de **67 mm** da área livre da
   antena (**conta**: do meio da zona de armazenamento, y 75, à borda da
   zona da antena, y 8), o que ajuda; manter o laço `SCK`/retorno o mais
   curto possível.
3. **Camada interna** entre planos de terra, como o display e o USB.

Uma quarta saída é de firmware e não de layout: **16 MHz tira o harmônico do
centro de L1** (o valor que [13](../docs/13-placa-nova.md#regras-de-projeto)
tinha escolhido para o mesmo barramento). Trocar o número é uma linha do
devicetree; **a decisão é do dono e não é deste documento**. O que a bancada
tem de fazer é o ensaio: `UBX-MON-SPAN` com a flash escrevendo e apagando,
com e sem os resistores.

### A placa de hoje dentro da caixa do conceito

O dono pediu, em 2026-09-26, para ver a caixa com a placa dentro; e depois,
o interior dela: lugar para colar a célula, teclas que batam com as chaves da
placa, os cortes para colar os painéis e algo transparente por cima deles
para a chuva; depois, as chaves da placa exatamente sob as capas, um dry run
da caixa inteira, a porta do USB-C, o suporte de uma antena GNSS externa e a
fixação dos painéis laterais conferida. O [`caixa/make_caixa.py`](caixa/make_caixa.py)
é uma **proposta** desenhada em volta da `gnssbike.kicad_pcb` de hoje (o
courtyard, a altura e a face de cada peça, e o GLB da placa nas vistas 3D),
e o [`caixa/dry_run_caixa.py`](caixa/dry_run_caixa.py) mede essa mesma
proposta, regra a regra; a decidir em cima dela; nada foi impresso.

| Decisão da proposta | Valor | Por quê |
|---|---|---|
| Caixa | 62 × **106** × **17** mm, raio 7, paredes 2, fundo e tampa 1,5 | a planta é a do conceito de 2026-09-20 mais 2 mm de comprimento, que o berço da antena externa pede (abaixo); 19 sobrava, e com 16 o USB-C (3,26) e o conector SWD batiam na tampa: sob ela sobram 4,2 mm da face da placa |
| Placa | centrada (x 14 a 48), a 0,5 mm da parede de baixo (y 8,5 a 103,5) | o USB-C chega ao entalhe da parede; em cima sobram 6,5 mm para o berço da antena |
| Pilha, do fundo à tampa | célula colada no fundo (z 1,8 a 8,8) entre quatro nervuras; 0,5 de ar e 1,2 de peças do verso; placa em 10,5 a 11,3; **3,0** de peças da frente sob o display (era 2,6: o receptor tem 2,7); display colado por baixo da tampa em volta da janela (fita 0,2), vidro em 14,3 a 15,3; tampa em 15,5 a 17 | os tetos das sombras da placa, os mesmos de `make_dxf.ZONES` (`DISPLAY_Y1`) |
| O que segura a placa | **duas** bossas M2, nos furos de (3,2; 7,0) e (14,4; 91,7), e quatro pilares de ø3 (três cantos e um ao lado do USB-C) | nenhum furo sobre a célula; o segundo foi para a borda de baixo porque a reserva dele ocupava o lugar do sensor de luz e a faixa do verso que segura o `J103` |
| Teclas | as três chaves da placa no passo de **13,4 mm** (x 3,6, 17 e 30,4), espalhadas na largura do display, e as capas **exatamente sobre elas**: capa quadrada de 5 em furo de 5,6, com aba de 7 × 0,5 por baixo da tampa; membrana de TPU de 0,3 num rebaixo de 0,4 | pedido do dono: mexer na placa, não fazer a caixa alcançar as chaves com barras; o furo da capa obrigou o display a subir 1,6 mm na placa (acima) |
| Painéis | dois módulos de 23 × 8 numa faceta plana de 1,5 mm abaixo das teclas, em bolsos de 1,9 sob uma cobertura de 0,6 colada num degrau de 1 mm, com furos de fio de ø1; dois em cada chanfro de 45° e **7,5 mm** das arestas longas (era 6,2), em bolsos de 1,9 cortados na face rebaixada de 0,6, sob uma **tira** transparente de ponta a ponta da rampa, com duas fendas de fio de 1,5 × 2 por bolso | a 6,2 a rampa tinha 8,8 mm e o módulo ocupa 8,4 dela: não havia lugar para degrau nem parede; a 7,5 a rampa tem 10,6, com 1,1 de parede em cada ponta e 0,5 atrás do bolso (`CX10`) |
| Chanfros na montagem | a parede longa da concha para em z 9,5 sob o chanfro, e o pé do chanfro (x 0 a 4,24) assenta nela; a face interna do chanfro é paralela à rampa até 1,0 mm do vidro do display e sobe vertical dali; a placa da tampa começa em x 7,5 ao lado dos chanfros, dentro do sólido deles | pedido do dono; medido em `CX11` (folga de 1,0 ao vidro e 7,96 à placa); até o dry run a placa da tampa atravessava a rampa 2,7 mm |
| Furos e janelas | USB-C na parede de baixo e na aba da tampa, o entalhe começando 0,3 abaixo da face da placa; porta de 14 × 8,2 × 1,2 por fora, em dois ressaltos com pino de ø1,5; três furos de som sob o buzzer e o respiro do barômetro no fundo; janela do LED (`D601`) e do sensor de luz (`U505`) sobre as peças, na fileira das teclas | as peças da placa saíram de baixo do display no mesmo dia |
| Antena GNSS externa (opção) | berço de 12,6 × 4,6 entre duas nervuras contra a parede de cima, com lábio na frente, para uma patch de 12 × 12 × 4 em pé; o rabicho U.FL chega ao `J302` a 15 mm | com a placa a 4,5 mm da parede de cima o berço entrava na placa (`CX12`): a caixa cresceu 2 mm |
| Tampa | 4 parafusos M2 nos cantos, em bossas de ø5, a mais de 8 mm das duas antenas | a vedação da partição não está desenhada |

O dry run da caixa, na placa de hoje: **12 regras medidas e cumpridas, 0
violadas, 1 não medida** (a passagem dos fios dos seis módulos por dentro da
tampa, a junta da porta e da partição, o aperto das capas na membrana e os
parafusos auto-atarraxantes: só uma prova impressa diz). Antes das correções
do dia ele acusava seis: `J103` a 0,05 mm da tampa e sob o display, `U301`
sob o display com 2,7 contra 2,6, os furos das capas 1,3 mm dentro do vidro,
o entalhe do USB-C 0,2 mm acima da base do receptáculo, o berço da antena
dentro da placa e a fita do display com 1,0 mm nos lados curtos — este
último é o que o display dá, e a regra passou a pedir 1,0.

Saem [`gnssbike-caixa.pdf`](caixa/gnssbike-caixa.pdf) (frente com a tampa e a
porta, por dentro com o berço, cortes A-A e B-B, detalhes da tecla e do
bolso, premissas, o que não bate e as peças), as vistas
[`gnssbike-3d-caixa-aberta.png`](../docs/img/hardware/gnssbike-3d-caixa-aberta.png),
[`gnssbike-3d-caixa-frente.png`](../docs/img/hardware/gnssbike-3d-caixa-frente.png) e
[`gnssbike-3d-caixa-explodida.png`](../docs/img/hardware/gnssbike-3d-caixa-explodida.png), e
os STL `caixa-concha`, `caixa-tampa`, `caixa-tecla-1/2/3`,
`caixa-membrana-teclas`, `caixa-cobertura-faceta`, `caixa-cobertura-chanfro`
e `caixa-porta-usb`, sopas de triângulos para o fatiador, não sólidos de CAD.

O que o desenho ainda mostra que **não bate**, para o dono decidir:

| O que | Medida | Quem cede |
|---|---|---|
| A célula (36) e o display (40,08) são mais largos que a placa (34) | 1 mm e 3,04 mm de cada lado | a caixa é quem os segura, e a proposta já faz isso |
| O conector da célula perdeu a trava positiva | JST SH de 2,9 mm no lugar do GH de 4,25, que não cabia sob a tampa (4,2 mm) | o cabo preso à caixa com fita, ou a caixa 0,5 mm mais alta com o GH |
| O display cobre 8,8 mm da área da antena GNSS | subiu 1,6 mm para o furo das capas sair do vidro | só medindo, na bancada (conflito já registrado acima) |
| O conceito tem microSD, AEM10900 e BM20C, a faceta entre o display e os botões e o engate atrás | — | o raio X do conceito (`docs/img/placa-nova-caixa.svg`) está desatualizado; o engate de quarto de volta não foi desenhado |

Não desenhados: a saída dos fios dos seis módulos por dentro da tampa até
`J103`, `J104` e `J105` (passam pelos furos e fendas), o pino e a junta da
porta, a vedação da partição, textos e logotipo.

## Montagem

Três restrições de processo mandam no layout, e todas vêm do módulo:

| Restrição | Consequência | De onde vem |
|---|---|---|
| **60 ilhas LGA por baixo**, além dos 20 pads castelados da borda | montagem por estêncil e forno. Os castelados se inspecionam e, no limite, se retocam com ferro; **as 60 ilhas do meio, não**. Um erro sob o módulo custa uma estação de ar quente ou a placa | desenho mecânico da ficha ME54BS13 V1.0.0 |
| **No máximo duas passagens pelo forno** | uma face por passagem; nada de retrabalho térmico "de brinde" | **regra herdada da ficha do BM20C**: a do ME54BS13 não foi lida quanto a refusão — **a confirmar** |
| **O lado do módulo por último** | a face do módulo é a **segunda** passagem | idem |

Combinando com a conta da sombra da bateria, que põe o módulo na **face da
frente** (acima), a ordem fica:

```mermaid
flowchart LR
    P1["1ª passagem · face de trás<br/>BMP585 no respiro, conector da bateria,<br/>peças até 1,2 mm sob a célula"] --> P2["2ª passagem · face da frente<br/>ME54BS13, MAX-F10S e blindagem,<br/>nPM1300, AEM10900, MAX17262,<br/>indutores, FPC, USB-C, teclas"]
    P2 --> P3["sem 3ª passagem:<br/>o que falhar vai a ar quente,<br/>peça a peça"]
```

O que isso impõe:

- **Tudo o que é pesado vai na segunda passagem**, ou é colado. Na segunda
  passagem a face de trás fica de cabeça para baixo e só a tensão
  superficial da solda a segura: o conector USB-C, o soquete FPC, a
  blindagem do GNSS e os indutores **não** podem ficar na face de trás sem
  cola. A geometria já ajuda: todos esses estão na frente.
- **A face de trás fica com pouca coisa**: o BMP585 junto do respiro, o
  conector da bateria e passivos baixos sob a célula. É o inverso do
  costume, e é consequência direta do módulo.
- **MSL.** O MAX-F10S é MSL 4 e o BMP585, MSL 3
  ([14](../docs/14-hardware-placa-nova.md#regras-de-layout)). Duas passagens
  consomem o orçamento de exposição das duas peças; se a placa parar entre
  as passagens, elas voltam para a estufa.
- **Peças WLP**, o MAX17262 e o MMC5633NJL, pedem estêncil fino e inspeção
  por raio X ou por ótica lateral, que **não estão disponíveis aqui**.

Estas conclusões vêm da regra da ficha e da geometria calculada acima;
**nada foi montado, e a escolha de face de cada peça é do arquivo de
montagem, que não existe.**

## O que só a bancada decide

| Em aberto | Por que não fecha aqui | Onde |
|---|---|---|
| **A pilha do fabricante** | sem as espessuras de dielétrico não há largura de trilha para 50 Ω nem para 90 Ω diferencial; 0,66 mm repartido em 3 vãos admite pilhas muito diferentes | [Camadas](#camadas), [02](02-calculos.md#o-que-não-foi-calculado) |
| **4 camadas em 0,8 mm** | o USB-C manda a espessura e o resto manda as camadas; falta confirmar que o fabricante faz a combinação | [Camadas](#camadas) |
| **A antena GNSS de verdade** | a TE L000670 não cabe: faltam 2,75 mm contra a zona e 5,65 mm contra a faixa livre acima do display | [Orçamento de área](#orçamento-de-área) |
| **Isolação entre as duas antenas** | a conta dá 67,2 mm, 0,55 λ em 2,44 GHz, 20 mm menos do que com o módulo antigo; a isolação real depende do plano, da caixa e das correntes de retorno. Medir o S21 antes de ligar o rádio na potência cheia | [As duas antenas](#as-duas-antenas), [15](../docs/15-avaliacao-componentes.md#bancada-antes-do-layout) |
| **Harmônico de 8 MHz da flash** | 0,58 MHz do centro de L1; só o `UBX-MON-SPAN` com a flash trabalhando diz se aparece | [As duas antenas](#as-duas-antenas) |
| **Alcance do rádio** | a linha de **20 mm** da tabela de isolação (ficha **7.2**) é cumprida na placa de [`cad/`](cad/), mas a de **25 mm do display não é e não pode ser** — 11,3 mm medidos; a bolsa da bateria fica a 4 mm da zona proibida; e se a MinewSemi tem regra de metal externo ninguém a leu | [Zonas proibidas](#zonas-proibidas), [09](09-dry-run-da-pcb.md) |
| **Área do FPC do display** | os **3,4 × 10 mm** da tabela de zonas não saem de ficha nenhuma: o PDF do Hirose FH28 que está em `datasheets/` é só a folha de especificação (ELC4-153887-02), **sem vista, sem corte e sem tabela de cotas**. Falta a folha de desenho da Hirose, ou medir uma amostra | [Orçamento de área](#orçamento-de-área) |
| **Folga entre placa e caixa** | 3,5 mm no desenho contra os 2,5 mm que [14](../docs/14-hardware-placa-nova.md#placa-de-circuito-impresso) descreve | [O contorno](#o-contorno) |
| **Raio de canto da placa** | 3 mm no desenho do conceito (`cad/make_dxf.RADIUS_DRAWING`) contra os 4 mm de [14](../docs/14-hardware-placa-nova.md#placa-de-circuito-impresso); as duas fontes discordam e nenhuma foi confirmada | [O contorno](#o-contorno) |
| **Face de cada peça e ordem do forno** | a conta põe o ME54BS13 na frente; o arquivo de montagem não existe | [Montagem](#montagem) |
| **Plugue do USB-C na caixa** | a boca do conector fica 0,77 mm atrás da face externa; um plugue de capa grossa pode não entrar | [Zonas proibidas](#zonas-proibidas) |
| **Contatos da antena** | a área dos contatos do elemento de antena na parede da caixa não está dimensionada. Os painéis **deixaram de ser pendência** em 2026-09-24: são um `J103` de 4 vias medido ([Como os painéis chegam à placa](#como-os-painéis-chegam-à-placa)) | [Orçamento de área](#orçamento-de-área) |
| **Zona do conector do filme de luz** | [14](../docs/14-hardware-placa-nova.md#placa-de-circuito-impresso) põe o Molex 5034800440 ao lado do FPC do display, mas não lhe dá retângulo, e a medida do corpo dele não está em nenhum documento daqui | [Orçamento de área](#orçamento-de-área) |
| **Empenamento e calor** | 0,8 mm empena mais, e o carregador linear dissipa até 1,50 W dentro de uma caixa vedada | [02](02-calculos.md#calor-do-carregador) |
| **Altura real das peças** | o empilhamento de [14](../docs/14-hardware-placa-nova.md#empilhamento-mecânico) fecha em 17,1 mm dentro de 19 mm, com 1,9 mm de folga, a partir de fichas e não de peças medidas | [14](../docs/14-hardware-placa-nova.md#empilhamento-mecânico) |
