Guiimartinho/gnss-bike-computer/docs/16-arquitetura-firmware.md

# Arquitetura do firmware e máquinas de estado

Arquitetura-alvo do firmware para a placa nova (nRF54LM20A, [14-hardware-placa-nova.md](14-hardware-placa-nova.md)): princípios, camadas, serviços, threads, eventos, máquinas de estado, energia, armazenamento, comunicação, atualização de firmware e a migração a partir do port atual ([05-arquitetura-zephyr.md](05-arquitetura-zephyr.md)). O comportamento continua sendo o do legacy ([04](04-arquitetura-legacy.md), [06](06-algoritmos.md), [08](08-interface.md)); o que muda é como o firmware se organiza para o hardware novo.

> [!IMPORTANT]
> Plano, em implementação. A base (serviços, threads, zbus, máquinas de sistema e de modo, watchdog por serviço) está no código desde 2026-09-19, descrita em [05](05-arquitetura-zephyr.md); o resto é plano. Nada foi testado em placa. Toda diferença de comportamento em relação ao legacy aparece marcada como proposta e, quando aprovada, vai para [06](06-algoritmos.md) e [10](10-status-do-port.md).

**Nesta página:** [Princípios](#princípios) · [Blocos do Zephyr e do NCS](#blocos-do-zephyr-e-do-ncs) · [Camadas](#camadas) · [Serviços](#serviços) · [Threads](#threads) · [Eventos](#eventos) · [Fluxo de dados](#fluxo-de-dados) · [Máquinas de estado](#máquinas-de-estado) · [Partida e desligamento](#partida-e-desligamento) · [Energia por estado](#energia-por-estado) · [Armazenamento](#armazenamento) · [Comunicação](#comunicação) · [Atualização de firmware](#atualização-de-firmware) · [Falhas](#falhas) · [Migração do port](#migração-do-port) · [Ordem de implementação](#ordem-de-implementação) · [Decisões em aberto](#decisões-em-aberto)

## Princípios

1. **O legacy é a especificação.** Modos, ciclo por localização, segmentos, telas, botões, menu e desligamento automático seguem o stravaV10; o que muda é a organização do código.
2. **Um dono por dado.** A thread do modelo é a única que escreve o estado do aparelho, como a `main_loop` do port antigo; as outras recebem cópias.
3. **Eventos, não varredura.** Cada serviço publica quando tem dado novo e dorme no resto do tempo. A CPU só acorda por motivo, o que conta num aparelho que gasta cerca de 21 mW ([15](15-avaliacao-componentes.md#efeito-no-aparelho)).
4. **ISR não processa.** A regra do projeto continua: a interrupção copia e acorda uma thread.
5. **Zephyr nativo.** Devicetree, drivers e subsistemas do Zephyr e do NCS: máquinas de estado no SMF, eventos no zbus, interface no LVGL, botões no subsistema de entrada, USB no `device_next`, arquivos no FatFs, configurações no ZMS, atualização pelo MCUboot.
6. **Energia por estado.** Cada estado do aparelho diz quais trilhos, rádios e sensores ficam ligados ([Energia por estado](#energia-por-estado)).
7. **Medido, não suposto.** Pilhas por `CONFIG_STACK_USAGE`, consumo pelo PPK2, watchdog por thread.

## Blocos do Zephyr e do NCS

Conferidos no NCS v3.3.0 local (`C:\ncs\v3.3.0`, Zephyr 4.3.99).

| Bloco | Onde | O que importa para este firmware |
|---|---|---|
| SMF | `zephyr/lib/smf`, `CONFIG_SMF` | estados hierárquicos com `CONFIG_SMF_ANCESTOR_SUPPORT`; ações de entrada, execução e saída; a execução devolve `SMF_EVENT_HANDLED` ou `SMF_EVENT_PROPAGATE` para o estado pai |
| zbus | `zephyr/subsys/zbus`, `CONFIG_ZBUS` | listener (roda no contexto de quem publica), subscriber (fila, `zbus_sub_wait`), message subscriber (cópia da mensagem) e async listener (workqueue) |
| Entrada | `gpio-keys`, `zephyr,input-longpress` | debounce por devicetree; o toque curto sai na soltura, o longo depois do tempo configurado |
| LVGL | `modules/lib/gui/lvgl` (9.5 "dev", instantâneo do master) e `zephyr/modules/lvgl` | teclado pelo `zephyr,lvgl-keypad-input`; o driver de tela é que define o formato de pixel ([18](18-interface-telas.md#framework)) |
| USB | `device_next`: `CONFIG_USBD_CDC_ACM_CLASS`, `CONFIG_USBD_MSC_CLASS` | o USBHS do nRF54LM20 tem suporte (`nordic,nrf-usbhs-nrf54l`); as amostras `cdc_acm` e `mass` do NCS aceitam o nRF54LM20A |
| Arquivos | FatFs R0.16 sobre `zephyr,flash-disk` | a placa não tem cartão: o disco é uma partição da flash NOR soldada (`boards/gnssbike_nrf54lm20a_cpuapp.overlay`), com `CONFIG_DISK_DRIVER_FLASH=y` e `CONFIG_DISK_DRIVER_SDMMC=n` no `.conf` da placa; o ponto de montagem continua `/SD:`. O caminho de cartão (`zephyr,sdhc-spi-slot` com `zephyr,sdmmc-disk`) e o LittleFS também existem no Zephyr, mas não são usados |
| Configurações | `CONFIG_ZMS` e `CONFIG_SETTINGS_ZMS` | a placa do DK não liga o ZMS por padrão; o port liga |
| Atualização | MCUboot pelo sysbuild (`SB_CONFIG_BOOTLOADER_MCUBOOT`), mcumgr | no nRF54L o NCS usa `SWAP_USING_MOVE` e assinatura ED25519; transportes BLE (pede o papel periférico) e UART, que chega ao USB pelo CDC ACM (amostra `usb_mcumgr`) |
| GNSS | `zephyr/include/zephyr/drivers/gnss.h` | posição por `GNSS_DATA_CALLBACK_DEFINE` (graus em nanograus, velocidade em mm/s) e satélites por `CONFIG_GNSS_SATELLITES`; os callbacks rodam no workqueue do modem; o driver do u-blox é do port (`modules/gnss_drivers`), com **dois** compatíveis, `u-blox,max-f10` e `u-blox,max-m10` (`dts/bindings/gnss/`), no mesmo código: a placa declara o `u-blox,max-f10` do MAX-F10S e o compatível é o que diz ao driver se o receptor tem o grupo `CFG-PM` |
| BLE | `CONFIG_BT_MAX_CONN`, clientes do NCS em `nrf/subsys/bluetooth/services` | o NCS traz clientes de FC (`hrs_client`), bateria, NUS e hora; **CSC, CPS, LNS e FTMS não têm cliente pronto**: o port mantém os seus, sobre o `BT_GATT_DM` |
| Energia | drivers `npm13xx` (mfd, regulador, carregador, GPIO, LED, watchdog), `maxim,max17262`, `sys_poweroff()` | o carregador expõe estado, erro e VBUS como canais de sensor; o nRF54L não tem PM de sistema, só PM de dispositivo e o System OFF |
| Sensores | `bosch,bmp581`, `bosch,bmi270`, `memsic,mmc56x3`, `ti,opt3001`; `st,lsm6dsv16x` para o IMU alternativo | o BMP581 lê por RTIO e só avisa dado pronto no modo de stream (pede o pino de interrupção); o BMI270 carrega um arquivo de configuração na partida e dá gatilhos de dado pronto e de movimento, mas o de movimento pede a configuração `base` (8 KB, compatível extra `bosch,bmi270-base`, sem exemplo no NCS) em vez da `max_fifo` padrão (328 bytes); o BMI270 não tem fusão, e a inclinação sai do acelerômetro, como no legacy; com o LSM6DSV16X no mesmo footprint, o devicetree declara os dois e o firmware usa o que `device_is_ready()` aceitar; o MMC5633NJL fica no mesmo I2C, e o firmware nunca varre o barramento (o endereço 0x7E o põe em I3C); o OPT3001 fica em modo contínuo, sem limiares |
| Watchdog | `CONFIG_TASK_WDT` | 5 canais por padrão: com as 8 threads da aplicação, o `prj.conf` põe `CONFIG_TASK_WDT_CHANNELS=10`; o `wdt31` vem desligado no dtsi do SoC, e o overlay do port o liga |

## Camadas

```mermaid
flowchart TB
    subgraph UI["interface"]
        SCR["telas e widgets (LVGL)<br/>menu, notificações, luz"]
    end
    subgraph APP["aplicação"]
        FSM["máquinas de estado (SMF)<br/>sistema, modo, gravação, interface"]
    end
    subgraph MODEL["modelo (port do legacy)"]
        BOU["boucle por modo<br/>attitude, Kalman, mode_fsm"]
        SEG["segmentos, percurso,<br/>zonas, suffer score, RR"]
        NOV["módulos novos<br/>power_metrics, alerts, workout,<br/>notif_filter, cps/lns/komoot, qry"]
    end
    subgraph SVC["serviços"]
        PWR["energia<br/>nPM1300, AEM10900, MAX17262"]
        GNS["GNSS<br/>u-blox por UBX"]
        SNS["sensores<br/>BMP585, BMI270, MMC5633NJL, OPT3001"]
        RAD["rádio<br/>BLE e ANT+"]
        STO["armazenamento<br/>FatFs na flash NOR"]
        USB["USB<br/>CDC ACM e MSC"]
        CFG["configurações<br/>ZMS"]
    end
    subgraph ZEP["Zephyr e NCS v3.3.0"]
        DRV["drivers por devicetree, zbus, SMF, LVGL,<br/>BT host e SoftDevice Controller, sdk-ant, USB device_next"]
    end
    SCR --> FSM
    FSM --> MODEL
    FSM --> SVC
    MODEL --> SVC
    SVC --> ZEP
    SCR --> ZEP
```

As camadas só se falam para baixo por chamada e para cima por evento: um serviço nunca chama a interface, publica um evento que a interface escuta.

Os módulos do modelo que não estavam no plano de 2026-09-18 e entraram depois, todos com teste de host próprio ([12](12-ferramentas-testes.md#testes-de-host-do-port)) e **nenhum testado em placa**:

| Módulo | O que faz |
|---|---|
| `model/power_metrics.c` | as métricas de Coggan: potência normalizada, fator de intensidade, TSS e índice de variabilidade |
| `model/alerts.c` | os 12 alertas do ciclista: máximo e mínimo de FC, potência, velocidade e cadência, marcos de distância, marcos de tempo em movimento e os lembretes de beber e de comer (`include/model/alerts.h:51-63`) |
| `model/workout.c` | o treino estruturado dos arquivos `.WKT`: passos, repetições e o alvo mandado ao rolo |
| `model/notif_filter.c` | o filtro das notificações do iPhone que chegam pelo ANCS (categoria, repetição, intervalo mínimo, chamadas) |
| `model/cps_parse.c` | o medidor de potência pelo BLE (Cycling Power): potência, cadência, velocidade e balanço entre as pernas |
| `model/lns_parse.c` | a posição do celular pelo BLE (Location and Navigation) |
| `model/komoot_turn.c` | as 24 direções do Komoot traduzidas nas 9 setas da tela |
| `model/qry.c` | as respostas do comando `$QRY`: listar o armazenamento e apagar um arquivo pela política de `model/file_policy.c` |

## Serviços

| Serviço | Responsável por | Publica | Hardware |
|---|---|---|---|
| Energia | ligar e desligar, ship mode, trilhos, carga pelo USB e pelo painel, estado de carga, desligamento automático, botão de ligar | estado da bateria e da carga, pedido de desligar | nPM1300, AEM10900, MAX17262 |
| GNSS | configuração por UBX, sinais de L1 e L5, AssistNow, backup, reinício por falta de dado (LEAP e potência plena só com o M10N) | uma posição por época (NAV-PVT), satélites | u-blox MAX-F10S, direto na UART (a 3,0 V desde 2026-09-26) |
| Sensores | barômetro a 10 Hz (como o legacy), IMU por FIFO, magnetômetro, luz ambiente | amostras filtradas | BMP585, BMI270, MMC5633NJL, OPT3001 |
| Rádio | BLE central (sensores e celular), ANT+ (HRM, BSC, FE-C), pareamento, religação | dados de cada sensor, estado de cada ligação | nRF54LM20A |
| Armazenamento | FatFs, formatos do legacy, lotes de gravação, carga de segmentos, percursos e treinos, comandos `$LOC`, `$DWN`, `$QRY` | resultados de carga, estado do armazenamento | flash NOR **MX25R6435F** de 8 MB soldada, sozinha no `spi00` (CS P2.05, 8 MHz), com `zephyr,flash-disk` montado em `/SD:` |
| USB | porta serial dos comandos (CDC ACM) e o disco do ciclista no PC (MSC) | estado da conexão | USBHS do nRF54LM20A |
| Configurações | FTP, peso, sensores pareados, campos das telas, calibração do magnetômetro | mudanças de configuração | ZMS no RRAM |

## Threads

Prioridade no Zephyr: número menor ganha. São **8** threads da aplicação, uma por serviço; os valores abaixo são os que estão no código (`APP_PRIO_*` em `include/app/app_svc.h` e o `K_THREAD_DEFINE` de cada serviço). A regra do projeto pede medir com `CONFIG_STACK_USAGE` e deixar 1 KB de folga: as oito foram medidas assim e todas passam da folga ([05](05-arquitetura-zephyr.md#pilhas)). Medida no build, não na placa.

| Thread | Prioridade | Pilha | Acorda com | Faz |
|---|---|---|---|---|
| `sensors` | 4 | 2048 B | timer de 100 ms e interrupção da FIFO do IMU | lê os sensores e publica |
| `model` | 5 | 4096 B | qualquer evento que o modelo assina | o ciclo do modo (a `main_loop` do port antigo), a única que escreve o modelo; publica uma cópia do estado por época |
| `gnss` | 6 | 2048 B | quadros UBX do receptor e pedidos da máquina de energia | configura o receptor, manda comando e espera resposta fora do workqueue do modem |
| `radio` | 6 | 3072 B | eventos do BT e do ANT, timers de religação | máquinas de estado de cada sensor, conversão em eventos |
| `ui` | 7 | 6144 B | cópia nova do modelo, botão, notificação, timer do LVGL | compõe e envia a tela, menu, luz |
| `storage` | 8 | 3584 B | lote de gravação, pedido de carga, comando | FatFs e comandos |
| `usb` | 8 | 2048 B | interrupção do CDC ACM e mudança de modo | porta serial dos comandos e disco MSC |
| `power` | 9 | 3072 B | interrupções do nPM1300, do AEM10900 e do MAX17262, timer de 60 s | energia, carga, desligamento |

Ficam por conta do Zephyr e do NCS: as threads do BT host e do MPSL, as do `sdk-ant`, a do subsistema de entrada, o workqueue do modem (onde rodam os callbacks do GNSS), o workqueue do sistema, o log e o idle. Cada thread da aplicação tem o seu canal de 4 s no `task_wdt`, como hoje ([05](05-arquitetura-zephyr.md#watchdog)), com `CONFIG_TASK_WDT_CHANNELS=10` no `prj.conf`, acima dos 5 do padrão.

## Eventos

O zbus passa mensagens por canais com cópia: quem publica não espera quem lê, e quem lê recebe um retrato consistente, sem a trava que a interface antiga usava (`model_lock()`). No código, cada serviço tem uma caixa de entrada enchida por listeners ([05](05-arquitetura-zephyr.md#eventos)), e a lista de canais cresceu para 20.

| Canal | Quem publica | Quem assina | Ritmo | Conteúdo |
|---|---|---|---|---|
| `gnss_fix` | GNSS | modelo | 1 Hz | posição, velocidade, rumo, altitude, hora, precisão, satélites |
| `baro` | sensores | modelo | 10 Hz | pressão e temperatura |
| `imu` | sensores | modelo | 1 Hz (lote da FIFO) | inclinação, rugosidade, movimento |
| `mag` | sensores | modelo | 1 Hz | rumo magnético |
| `ambient` | sensores | interface | 1 Hz | lux |
| `ext_sensor` | rádio | modelo | por dado | FC e RR, potência, cadência, velocidade, rolo |
| `phone` | rádio | modelo | por dado | posição do celular (LNS), curva do Komoot |
| `link_status` | rádio | interface | por mudança | estado de cada sensor |
| `model_state` | modelo | interface, armazenamento, rádio | por época | o retrato do modelo que as telas mostram |
| `notif` | modelo, rádio, energia, armazenamento | interface | por evento | notificação com tipo e duração |
| `log_record` | modelo | armazenamento | a cada lote (5 snapshots de 15 m) | registros do log |
| `power_status` | energia | interface, modelo | por mudança e a cada 60 s | tensão, estado de carga, fonte de carga, temperatura |
| `system_cmd` | interface, energia, armazenamento | aplicação | por evento | trocar modo, desligar, entrar em MSC |
| `input` | subsistema de entrada | interface | por botão | botão e tipo de toque |

## Fluxo de dados

```mermaid
flowchart LR
    GNSSM["MAX-F10S"] -->|"NAV-PVT"| GS["serviço GNSS"]
    BARO["BMP585"] --> SS["serviço de sensores"]
    IMU["BMI270 e MMC5633NJL"] --> SS
    EXT["sensores BLE e ANT+"] --> RS["serviço de rádio"]
    PHONE["celular"] --> RS
    GS -->|"gnss_fix"| MOD["modelo<br/>boucle do modo"]
    SS -->|"baro, imu, mag"| MOD
    RS -->|"ext_sensor, phone"| MOD
    MOD -->|"model_state"| UI["interface"]
    MOD -->|"log_record"| ST["armazenamento"]
    MOD -->|"notif"| UI
    PS["serviço de energia"] -->|"power_status"| UI
    PS -->|"power_status"| MOD
    ST --> FS[("FatFs em /SD:<br/>flash NOR MX25R6435F")]
    UI --> LCD["Sharp LS027B7DH01A<br/>ou JDI LPM027M128C"]
```

## Máquinas de estado

Todas no SMF do Zephyr, com estados hierárquicos e ações de entrada, execução e saída; cada máquina roda na thread do serviço que a possui. A dos segmentos continua a do legacy ([06](06-algoritmos.md#segmentos)).

| Máquina | Dono | Origem |
|---|---|---|
| Sistema e energia | serviço de energia | nova; desligamento automático do legacy (`legacy/source/scheduling/power_scheduler.cpp:16-46`) |
| Modo | modelo | desenho próprio em `model/mode_fsm.c`, com as famílias e as três regras abaixo |
| Gravação | modelo | log do legacy (`Attitude::computeDistance`, `legacy/source/model/Attitude.cpp:431-490`) |
| GNSS | serviço GNSS | `GPS_MGMT` (`legacy/source/sensors/GPSMGMT.cpp:143-265`), refeita para UBX |
| Sensor externo | serviço de rádio, uma por sensor | pareamento do `ant_device_manager` e reaberturas do HRM ([07](07-radio-ant-ble.md#ant-no-legacy)) |
| Carga | serviço de energia | nova |
| Interface | interface | telas por modo e menu (`legacy/source/vue/Vue.h:21-26`, `legacy/source/vue/Menuable.cpp:255-294`) |
| Luz do display | interface | nova (a V3 não tem luz) |
| Segmento | modelo | legacy, sem mudança |

### Sistema e energia

```mermaid
stateDiagram-v2
    [*] --> Desligado
    Desligado --> Partida: botão de ligar ou VBUS
    Partida --> Ligado: serviços prontos
    Ligado --> Desligando: pedido de desligar
    Desligando --> Desligado: sem VBUS
    Desligando --> CarregandoDesligado: com VBUS
    CarregandoDesligado --> Desligado: VBUS some
    CarregandoDesligado --> Partida: botão de ligar
    Ligado --> MSC: comando $DWN,16
    MSC --> Partida: reset
    note right of Desligado
        ship mode do nPM1300
        painel carrega até 3,90 V
        backup do GNSS ligado
    end note
    note right of CarregandoDesligado
        o nPM1300 não entra em ship mode com VBUS
        MCU em System OFF, só o BUCK2 (3V0) ligado
        acorda pelo GPIO3 quando o VBUS some
    end note
```

- **Pedido de desligar:** menu, botão de ligar mantido apertado, 15 min sem ping ou bateria crítica.
- **Desligamento automático:** 15 min sem ping desligam, como no legacy. O ping vem de cada localização processada em CRS e PRC (`legacy/source/model/BoucleCRS.cpp:197`) e de cada dado do rolo em FEC (`legacy/source/model/BoucleFEC.cpp:83`). Parado com fix, o legacy nunca desliga; pingar só em movimento é uma **proposta**, a decidir.
- **Bateria crítica:** nova. Quando o MAX17262 marca a bateria no fim (0 %, que ele declara na tensão de vazio, 3,3 V), o aparelho grava e desliga antes do PCM cortar a célula. Antes, a 10 %, uma notificação de bateria fraca. No código desde 2026-09-19 (`src/svc/power/battery.c`, [06](06-algoritmos.md#bateria)); não testado na placa.
- **Botão de ligar:** o nPM1300 liga pelo SHPHLD e avisa o MCU pelo GPIO3, como a amostra `npm13xx_one_button`; o desligamento pelo botão longo sai da mesma amostra.

### Modo

Os cinco modos vivem em duas famílias, e a família é um estado pai de verdade, não uma função auxiliar: ao ar livre a posição vem do receptor e alimenta a distância; dentro de casa ela vem do rolo ou do PC, e um fix não quer dizer nada.

```mermaid
stateDiagram-v2
    [*] --> CRS
    state "Ao ar livre" as Outdoor {
        CRS
        PRC
        DBG
    }
    state "Dentro de casa" as Indoor {
        FEC
        Zwift
    }
    CRS --> PRC: menu, com percurso carregado
    PRC --> CRS: menu, ou o percurso saiu
    CRS --> DBG: menu
    DBG --> CRS: menu
    Outdoor --> Indoor: menu, fora de uma gravação
    Indoor --> Outdoor: menu, fora de uma gravação
    note right of Outdoor
        GNSS ligado, barômetro a 10 Hz
        ciclo a cada localização
    end note
    note right of Indoor
        GNSS em backup, canal FE-C aberto
        ciclo a cada dado do rolo
    end note
```

A máquina é `model/mode_fsm.c`, com teste de host próprio (`test_mode_fsm`). Ela **não** é o `boucle__change_mode()` do legacy (`legacy/source/model/Boucle.cpp:101-142`), que não guarda nada e deixa entrar em qualquer modo a qualquer momento. Três regras foram acrescentadas, e cada uma era um jeito de perder um pedal:

1. **Modo de percurso pede percurso.** Entrar em PRC sem nada carregado deixava o ciclista numa tela de navegação sem navegação; agora a troca é recusada e a tela diz o porquê. Se o percurso sair debaixo de quem está seguindo, o modo volta sozinho para CRS.
2. **Pedal gravando não muda de família.** Sair da rua para o rolo no meio de uma gravação misturava dado de rolo no arquivo de um pedal de verdade. Dentro da mesma família a troca é livre: quem grava na rua pode querer o percurso ou a tela de diagnóstico, e nenhum dos dois muda de onde vêm os números.
3. **Os números da sessão são da atividade, não do modo.** A máquina não encosta nas zonas de potência nem no suffer score. Até 2026-09-21 entrar em FEC chamava `power_zone_reset()` e `suffer_score_reset()`, e quem punha a bicicleta no rolo perdia as zonas do pedal inteiro — e eram as duas únicas chamadas de reset no firmware, de modo que fora desse caminho as zonas nunca zeravam.

Duas coisas do legacy ficaram **de fora** de propósito: invalidar o modo antigo para liberar os pontos do percurso (aqui eles moram num vetor estático, não há o que liberar) e o `stc.resetCharge()` a cada troca (o medidor de carga do legacy não existe na placa nova).

- O GNSS segue a família: acorda ao ar livre (`legacy/source/model/BoucleCRS.cpp:38`) e dorme dentro de casa (`legacy/source/model/BoucleFEC.cpp:45`). No u-blox, dormir é mandar `UBX-RXM-PMREQ` e desligar o BUCK1, com o backup mantido.
- O MSC fica na máquina de sistema, porque desmonta o FatFs e para o modelo.

### Gravação

```mermaid
stateDiagram-v2
    [*] --> SemPosicao
    SemPosicao --> Descarte: primeira posição válida
    Descarte --> Gravando: 25 m percorridos
    Gravando --> SemPosicao: posição some
    note right of Gravando
        snapshot a cada 15 m
        a cada 5 snapshots grava o lote
        no arquivo do dia e salva o estado para o FDIR
    end note
```

É a gravação do legacy: contínua em CRS e PRC, num arquivo por dia (`@DDMMYY.txt`, [09](09-armazenamento-usb.md#arquivos-do-legacy)), sem início nem fim explícitos. Atividade com início, pausa e fim, e exportação em FIT ou GPX para o Strava, é **proposta** ligada aos formatos no SD, que continuam em aberto.

### GNSS

O receptor escolhido, o **MAX-F10S**, não tem modo econômico de rastreio: a firmware do F10 não tem o grupo `CFG-PM` (descrição de interface UBX-23002975 R02, seção 4.8). A máquina é a mesma para as duas peças do footprint, e o que muda é se o estado **LEAP** existe: o serviço passa `has_leap` ao `gnss_power_init()` a partir do compatível do devicetree.

```mermaid
stateDiagram-v2
    [*] --> Backup
    Backup --> Adquirindo: modo CRS ou PRC
    Adquirindo --> Rastreando: primeiro fix
    Rastreando --> Plena: sinal fraco, só com LEAP
    Plena --> Rastreando: sinal bom por 60 s, só com LEAP
    Rastreando --> Assistencia: dados do AssistNow chegam (a fazer)
    Assistencia --> Rastreando: dados gravados
    Rastreando --> Backup: modo FEC ou Zwift, desligar
    Plena --> Backup: modo FEC ou Zwift, desligar
    Adquirindo --> Backup: modo FEC ou Zwift, desligar
    note right of Rastreando
        F10S: potencia plena, 46,8 mW, 1 Hz
        M10N: LEAP, 13,7 mW, 1 Hz
        sem depender do TIMEPULSE
    end note
    note right of Backup
        UBX-RXM-PMREQ, depois o BUCK1 desligado
        V_BCKP pelo TPS7A02
    end note
```

- **Sinal fraco:** fix perdido, ou precisão estimada pior que um limite a ajustar na bancada. Vale só para o M10N, onde o LEAP rastreia até −159 dBm e a potência plena até −167 dBm ([15](15-avaliacao-componentes.md#escolha-max-f10s)). No F10S o rastreio já é de −167 dBm e não há para onde subir: com `has_leap` falso a máquina nunca pede um modo de energia, e o estado de rastreio aparece como potência plena.
- **Assistência:** a SPG 5.30 pede o LEAP desligado enquanto os dados do AssistNow Live Orbits vão para a flash do módulo. O F10S é ROM e não tem Live Orbits: sobram o AssistNow Offline e o Autonomous, só de L1.
- **Sinais do F10:** todo `CFG-SIGNAL` reinicia o subsistema GNSS, e a seção 4.9.20 pede esperar o reconhecimento e mais 0,5 s. O driver manda as nove chaves de L1, L5 e NavIC num `UBX-CFG-VALSET` só, para custar um reinicio em vez de nove.
- **Vigia:** o legacy reinicia a UART quando passa 3 s sem hora nem satélites (`legacy/source/sensors/GPSMGMT.cpp:143-176`), e avisa na tela. Aqui, 10 s sem `UBX-NAV-PVT` com o receptor ligado mandam a configuração de novo, e 30 s puxam o RESET_N (ou mandam `UBX-CFG-RST`, sem o pino), com notificação: a configuração custa cerca de 0,5 s (mais 0,5 s do reinicio dos sinais, no F10), então não vale repetir a cada 3 s. Implementado em `gnss_power.c` (`GNSS_POWER_SILENCE_MS` e `GNSS_POWER_RESET_MS`), com `test_gnss_power`.
- **Implementado** em 2026-09-19, sem receptor para testar: a máquina inteira em `src/svc/gnss/gnss_power.c` (pura, com `test_gnss_power`, 21 casos, dos quais 5 são do receptor sem LEAP) e as ações no driver próprio ([05](05-arquitetura-zephyr.md#receptor-gnss)). Falta a assistência: o AssistNow ainda não entrou.
- **Ajuda do celular:** o legacy manda a posição do LNS ao GPS depois de 5 posições seguidas (`legacy/source/model/Locator.cpp:217`); no u-blox é o `UBX-MGA-INI-POS_LLH`.

### Sensor externo

Uma máquina por sensor pareado: frequência cardíaca, velocidade e cadência, potência, rolo, e o que o [catálogo de dispositivos](17-dispositivos-ble-ant.md) acrescentar.

```mermaid
stateDiagram-v2
    [*] --> SemPar
    SemPar --> Buscando: pareamento no menu
    Buscando --> Conectado: escolhido na lista, ID salvo
    Buscando --> SemPar: cancelado ou 30 s
    Conectado --> Perdido: sem dado por 5 s
    Perdido --> Conectado: dado volta
    Perdido --> Religando: 30 s
    Religando --> Conectado: ID salvo encontrado
    note right of Religando
        ANT+: busca de baixa prioridade pelo número do dispositivo
        BLE: varredura com filtro de endereço
    end note
```

- O pareamento do legacy busca em fundo e lista até 7 sensores com ID e RSSI (`legacy/rf/ant_device_manager.cpp`, [07](07-radio-ant-ble.md#ant-no-legacy)).
- Os tempos (5 s, 30 s) são de partida; o HRM do legacy reabre o canal até 5 vezes.

### Carga

```mermaid
stateDiagram-v2
    [*] --> Bateria
    Bateria --> Solar: AEM10900 transferindo
    Solar --> Bateria: sem luz
    Bateria --> USBCarregando: VBUS
    Solar --> USBCarregando: VBUS
    USBCarregando --> USBCheia: fim de carga
    USBCheia --> USBCarregando: recarga
    USBCarregando --> PausaTermica: NTC fora da faixa
    PausaTermica --> USBCarregando: NTC volta
    USBCarregando --> Falha: erro do carregador
    USBCarregando --> Bateria: VBUS some
    USBCheia --> Bateria: VBUS some
    PausaTermica --> Bateria: VBUS some
    Falha --> Bateria: VBUS some
```

- A máquina só mostra o que os carregadores fazem sozinhos ([15](15-avaliacao-componentes.md#convivência-das-duas-cargas)): com VBUS, o hardware bloqueia o solar e só o nPM1300 carrega.
- No código desde 2026-09-19 (`src/svc/power/charge.c`, [05](05-arquitetura-zephyr.md#carregador)): o estado sai dos registradores do nPM1300 e do AEM10900 a cada evento e a cada 10 s, e pausa térmica e falha viram notificação. Não testado na placa.
- Fontes: estado do carregador e erros do nPM1300, interrupção e APM do AEM10900, estado de carga e corrente do MAX17262.

### Interface

```mermaid
stateDiagram-v2
    [*] --> Paginas
    Paginas --> Menu: centro
    Menu --> Paginas: Back
    Menu --> Lista: percursos ou pareamento
    Lista --> Menu: Back
    Menu --> Valor: FTP ou peso
    Valor --> Menu: centro grava
    Paginas --> TelaGPS: posição com mais de 6 s
    TelaGPS --> Paginas: posição volta
    note right of Paginas
        CRS: esquerda e direita trocam de página
        PRC: esquerda e direita mudam o zoom
        FEC e DBG: só o centro
    end note
```

- Botões e menu do legacy ([08](08-interface.md#botões)); nos primeiros 5 s depois da partida o menu não abre (`legacy/source/vue/Menuable.cpp:326`).
- Notificações ficam por cima de qualquer estado: fila de até 10, a primeira por cerca de 6 s ([08](08-interface.md#notificações)).
- As telas de cada estado, com maquetes, estão em [18](18-interface-telas.md#telas).

### Luz do display

```mermaid
stateDiagram-v2
    [*] --> Apagada
    Apagada --> Temporaria: botão
    Temporaria --> Apagada: 10 s sem botão
    Apagada --> Automatica: pouca luz
    Automatica --> Apagada: luz ambiente volta
    Temporaria --> Automatica: pouca luz
```

Nova: a V3 não tem luz. O OPT3001 decide "pouca luz", com histerese para não piscar; limite, tempo e brilho (PWM) se ajustam na bancada. Com a luz acesa, a ficha do JDI pede o COM perto de 60 Hz; como o COM é metade do EXTCOMIN (até 70 e 140 Hz na ficha), o EXTCOMIN vai a cerca de 120 Hz, e volta a 1 Hz com a luz apagada. Na Sharp da [lista de compras](19-lista-de-compras.md#display), a luz é o filme frontal da Azumo (10 mA), alimentado pela LDSW2 em 3,3 V; a frequência do EXTCOMIN com a luz acesa se acerta na bancada, dentro da faixa da ficha da Sharp.

## Partida e desligamento

```mermaid
sequenceDiagram
    participant P as nPM1300
    participant B as MCUboot
    participant E as energia
    participant S as armazenamento e configurações
    participant G as GNSS
    participant R as rádio
    participant M as modelo e interface
    P->>B: SHPHLD ou VBUS, BUCK2 a 3,0 V pelo VSET2
    B->>E: aplicação válida
    E->>E: causa do reset, limites do nPM1300, MAX17262, AEM10900 por I2C
    E->>S: ZMS e FatFs
    S->>M: tela inicial e notificação de falha anterior
    E->>G: BUCK1, configuração UBX, sinais L1 e L5
    E->>R: BLE e ANT, religação dos sensores salvos
    E->>M: modo CRS e páginas
```

```mermaid
sequenceDiagram
    participant X as quem pede
    participant M as modelo
    participant S as armazenamento
    participant G as GNSS
    participant R as rádio
    participant U as interface
    participant E as energia
    X->>E: desligar (menu, 15 min, bateria crítica)
    E->>M: parar o ciclo
    M->>S: último lote e estado do FDIR
    S->>S: fechar arquivos e desmontar
    E->>G: UBX-RXM-PMREQ, depois BUCK1 desligado
    E->>R: fechar canais ANT e ligações BLE
    E->>U: limpar a tela e DISP baixo
    E->>E: AEM10900 de volta aos pinos
    alt sem VBUS
        E->>E: ship mode
    else com VBUS
        E->>E: trilhos desligados e System OFF
    end
```

- O legacy zera o estado salvo da atividade antes de desligar (`legacy/source/scheduling/power_scheduler.cpp:36-37`); o port faz o mesmo.
- A tela MIP precisa da inversão do VCOM enquanto mostra imagem: antes de parar o MCU, ela fica limpa e com DISP baixo.

## Energia por estado

| Estado | MCU | 3V0 (BUCK2) | 1V8 (BUCK1) | LDSW1 | GNSS | Rádio | Tela | Consumo |
|---|---|---|---|---|---|---|---|---|
| Desligado | sem alimentação | desligado | desligado | desligado | backup | desligado | desligada | cerca de 34 µA ([14](14-hardware-placa-nova.md#estados-de-energia)) |
| Carregando desligado | System OFF | ligado | desligado | desligado | backup | desligado | desligada | do USB |
| CRS ou PRC | ativo entre eventos | ligado | ligado | em lotes | rastreio (F10S: potência plena; M10N: LEAP) | ligações e canais abertos | 1 quadro/s | cerca de 58 mW com o F10S, 21 mW com o M10N em LEAP ([15](15-avaliacao-componentes.md#efeito-no-aparelho)) |
| FEC ou Zwift | ativo entre eventos | ligado | desligado | em lotes | backup | canal FE-C e sensores | 1 quadro/s | a medir |
| MSC | ativo | ligado | desligado | ligado | backup | desligado | parada | do USB |

## Armazenamento

- **FatFs** sobre a flash NOR **MX25R6435F** de 8 MB soldada, sozinha no `spi00` (CS P2.05, `spi-max-frequency = 8000000`), por `zephyr,flash-disk` numa partição que toma a peça inteira ([15](15-avaliacao-componentes.md#armazenamento)). A placa **não tem cartão nem SD NAND**: a troca é de 2026-09-20. O ponto de montagem continua `/SD:`, para que nem o firmware nem o PC precisem aprender outro nome, e os formatos são os do legacy: segmentos, `*.PAR`, `@DDMMYY.txt` ([09](09-armazenamento-usb.md#arquivos-do-legacy)).
- **Lotes:** o modelo manda 5 snapshots por vez, como o legacy; a thread de armazenamento liga a LDSW1, grava, sincroniza e pode desligar a chave de novo.
- **Carga de segmentos e percursos:** pedido do modelo e resposta por evento, fora da thread do modelo, porque ler o armazenamento pode passar de 4 s ([05](05-arquitetura-zephyr.md#watchdog)).
- **Configurações** no ZMS do RRAM, como o port já faz no nRF54LM20 DK.
- **MSC:** desmonta o FatFs antes de expor o disco pelo USB, como o legacy faz com `$DWN,16`.

## Comunicação

| Canal | Uso | Base |
|---|---|---|
| USB | CDC ACM para comandos e log; MSC para os arquivos | USB `device_next` |
| BLE central | sensores (FC, potência, velocidade e cadência, rolo), celular (LNS, Komoot), ponte com o stravaAP pelo NUS | BT host do Zephyr e clientes do NCS |
| ANT+ | HRM, BSC e FE-C nos canais do legacy, busca em fundo para o pareamento | `sdk-ant` v2.1.1 ([07](07-radio-ant-ble.md#ant-no-ncs-v330)) |
| Comandos | `$LOC`, `$DWN`, `$QRY` pelo USB e pelo NUS | VParser do legacy ([07](07-radio-ant-ble.md#stravaap-e-comandos)) |

O que o legacy usa e o que o `sdk-ant` oferece estão em [07](07-radio-ant-ble.md); a lista completa de dispositivos, com perfis, prioridades e o orçamento de canais e conexões, está em [17](17-dispositivos-ble-ant.md).

## Atualização de firmware

- **MCUboot** pelo sysbuild. O mapa padrão do nRF54LM20 tem 64 KB para o MCUboot, duas imagens de 920 KB e 36 KB de armazenamento (`nrf54lm20_a_b_cpuapp_partition.dtsi`); o firmware com ANT ocupa cerca de 330 KB hoje ([03](03-ambiente-build.md#resultado-de-referência)), então cabe com folga. O port já compila sem o Partition Manager (`SB_CONFIG_PARTITION_MANAGER=n`), e esse mapa do devicetree vale.
- **Modo e assinatura:** no nRF54L o NCS usa `SWAP_USING_MOVE` e ED25519 por padrão; a chave fica fora do repositório.
- **Transporte:** mcumgr (SMP) pelo USB, pelo transporte UART sobre o CDC ACM (a amostra `usb_mcumgr` do NCS faz isso no nRF54LM20 DK), e pelo BLE, que pede o papel periférico — já ligado (`prj.conf:185-186`, `CONFIG_BT_PERIPHERAL=y` junto com `CONFIG_BT_CENTRAL=y`).

## Falhas

- **Watchdog:** um canal de 4 s por thread no `task_wdt`, com o WDT do nRF por trás ([05](05-arquitetura-zephyr.md#watchdog)).
- **FDIR:** o estado salvo da atividade volta depois de um reset, como o `crash_recovery` do port e o FDIR do legacy ([06](06-algoritmos.md#distância-acumulada-e-log)).
- **Queda de tensão:** o comparador de falha de energia (POF) do nPM1300 avisa quando o VSYS cai; o firmware usa o aviso para gravar o lote pendente.
- **Falha anterior:** a causa do reset e o registro de falha aparecem numa notificação na partida, como no legacy ([04](04-arquitetura-legacy.md#boot)).

## Migração do port

| Até 2026-09-18 | Alvo (a base entrou em 2026-09-19, [05](05-arquitetura-zephyr.md)) |
|---|---|
| `main_loop` a cada 100 ms, com botões por varredura | thread `model` que dorme até um evento; botões pelo subsistema de entrada |
| `display` a cada 50 ms, lendo o modelo sob `model_lock()` | thread `ui` com LVGL, lendo a cópia do `model_state` |
| `hal_gpio`, `hal_i2c`, `hal_spi`, `hal_uart` | drivers do Zephyr direto, pelo devicetree |
| `gps_mgmt`, `nmea_parser`, `gps_epo` (MediaTek) | serviço GNSS por UBX, com AssistNow no lugar do EPO |
| `ls027` | driver próprio e LVGL, para a Sharp da lista de compras e para o JDI no mesmo conector |
| BME280, FXOS8700, STC3100 | BMP585, BMI270 e MMC5633NJL, MAX17262 e nPM1300 |
| `power_scheduler` pelo STC3100 | máquina de sistema no serviço de energia, ship mode do nPM1300 |
| `neopixel` (WS2812) | `pwm-leds` com o LED RGB |
| `user_settings` | ZMS, sem mudança |
| `boucle`, `attitude`, segmentos, zonas | sem mudança de algoritmo; recebem eventos em vez de chamadas |

## Ordem de implementação

```mermaid
flowchart LR
    A["1 · base no nRF54LM20 DK<br/>zbus, SMF, threads, watchdog"] --> B["2 · energia<br/>placas de avaliação do nPM1300 e do AEM10900"]
    B --> C["3 · GNSS por UBX<br/>placa de avaliação do M10N"]
    C --> D["4 · sensores"]
    D --> E["5 · armazenamento<br/>FatFs, formatos, lotes"]
    E --> F["6 · rádio<br/>BLE e ANT+"]
    F --> G["7 · interface<br/>LVGL, telas"]
    G --> H["8 · USB e atualização<br/>CDC, MSC, MCUboot"]
```

Encaixa no roteiro de [10](10-status-do-port.md#roteiro): os passos 1 e 2 fecham a fase 1 na placa própria, e os demais seguem as fases 2 a 7.

## Decisões em aberto

| Decisão | Opções | Onde pesa |
|---|---|---|
| Desligamento automático parado com fix | como o legacy (não desliga) ou pingar só em movimento | [Sistema e energia](#sistema-e-energia) |
| Atividade e formato de exportação | log contínuo do legacy, ou atividade com início, pausa e fim e arquivo FIT ou GPX | [Gravação](#gravação) |
| Saída do MSC | só com reset, como o legacy, ou ao desconectar o USB | [Sistema e energia](#sistema-e-energia) |

**Decidida e implementada:** o **papel periférico** entra junto com o central. O `prj.conf:185-186` liga `CONFIG_BT_PERIPHERAL=y` e `CONFIG_BT_CENTRAL=y`, e o cliente de notificações do iPhone (`rf/ble_ancs_client.c`) só funciona com ele, assim como a atualização sem cabo pelo SMP. Não testado com nenhum celular ([17](17-dispositivos-ble-ant.md#limites-do-rádio)).
