Guiimartinho/gnss-bike-computer/docs/05-arquitetura-zephyr.md

# Arquitetura do port Zephyr

Como o `zephyr_app/` está organizado desde 2026-09-19: um serviço por assunto, cada um com a sua thread, eventos no zbus, máquinas de estado no SMF e o hardware pelas APIs do Zephyr, achado por aliases do devicetree. É a base da arquitetura planejada em [16-arquitetura-firmware.md](16-arquitetura-firmware.md); o que cada serviço já faz, e o que falta, está em [10-status-do-port.md](10-status-do-port.md).

> [!IMPORTANT]
> Build verificado em três alvos — `nrf54lm20dk/nrf54lm20a/cpuapp` (o padrão dos scripts), `gnssbike/nrf54lm20a/cpuapp` (a placa do projeto) e `nrf52840dk/nrf52840`, que ainda compila mas **saiu de uso** —, com e sem ANT, e testes de host; **nada rodou em placa**.

**Nesta página:** [Camadas](#camadas) · [Boot](#boot) · [Threads](#threads) · [Eventos](#eventos) · [Máquinas de estado](#máquinas-de-estado) · [Watchdog](#watchdog) · [Fluxo de dados](#fluxo-de-dados) · [Pilhas](#pilhas) · [Tela](#tela) · [Medidor de bateria](#medidor-de-bateria) · [Carregador](#carregador) · [Módulos](#módulos) · [Devicetree e alvos](#devicetree-e-alvos) · [Configuração](#configuração) · [Regras de concorrência](#regras-de-concorrência)

## Camadas

```mermaid
flowchart TB
    subgraph APP["src/app"]
        MAIN["main.c<br/>boot"]
        CHAN["app_channels.c<br/>canais do zbus"]
        SVCF["app_svc.c<br/>watchdog e caixas de entrada"]
    end
    subgraph SVC["src/svc: oito serviços, uma thread cada"]
        PWR["power<br/>máquina de sistema"]
        GNS["gnss"]
        SNS["sensors<br/>tilt"]
        RAD["radio"]
        STO["storage"]
        USBS["usb"]
        MOD["model<br/>máquina de modos"]
        UIS["ui"]
    end
    subgraph MODEL["src/model: algoritmos do legacy"]
        ALG["attitude, Kalman, máquina de modos, segmentos,<br/>percurso, zonas, log, FDIR, configurações"]
    end
    subgraph RF["src/rf"]
        BLE["ble_manager e clientes"]
        ANTN["ant (só com ANT=1)"]
    end
    subgraph UIX["src/ui: telas"]
        SCRS["telas, campos, textos, tema<br/>o mesmo código do renderizador de host"]
    end
    subgraph Z["Zephyr e NCS v3.3.0"]
        ZAPI["zbus, SMF, task_wdt, GNSS, sensores, FatFs,<br/>settings, LVGL, entrada, BT host e SoftDevice Controller"]
    end
    subgraph DRV["modules/gnss_drivers"]
        MEM["memlcd: JDI LPM027M128B e C,<br/>Sharp LS027B7DH01, em retrato"]
    end
    MAIN --> SVC
    SVC --> CHAN
    MOD --> MODEL
    STO --> MODEL
    RAD --> RF
    UIS --> UIX
    UIX --> ZAPI
    SVC --> ZAPI
    RF --> ZAPI
    ZAPI --> MEM
```

- Um serviço nunca chama outro: publica num canal, e quem precisa escuta. As chamadas só descem, para o modelo e para o Zephyr.
- Os nomes em francês vêm do legacy (`parcours` = percurso, `liste_points`, `vecteur`); o glossário está em [04-arquitetura-legacy.md](04-arquitetura-legacy.md#glossário).

## Boot

```mermaid
sequenceDiagram
    participant M as main()
    participant S as serviços
    participant P as energia
    M->>M: alimenta o WDT que sobreviveu a um reset por software
    M->>M: crash_recovery_init (causa do reset, FDIR)
    M->>M: user_settings_init e enforce (NVS ou ZMS)
    M->>M: task_wdt sobre o watchdog0
    M->>M: model_svc_init (attitude, segmentos, percurso, zonas)
    M->>S: storage, usb, power, sensors, gnss, radio, model, ui
    M->>P: power_svc_ready
    P->>S: system_state Ligado
    M-->>M: retorna (a thread main termina)
```

- Os drivers do Zephyr (sensores, receptor GNSS, cartão, tela) iniciam antes do `main()`; um que não responde fica fora, e o serviço dele segue sem ele. O driver da tela limpa a memória do painel (all clear) e liga o COM; o LVGL inicia logo depois (`CONFIG_LV_Z_AUTO_INIT`), ainda sem desenhar.
- A thread `ui` monta a tela de partida, desenha e só então acende a imagem (`display_blanking_off()`, pino DISP); o primeiro retrato do modelo leva à página do modo.
- O `model_svc_init()` roda antes das threads porque o `segment_init()` zera os segmentos: se rodasse depois, apagaria o que o armazenamento acabou de carregar.
- O armazenamento monta o cartão, carrega os segmentos e publica o que achou; o modelo só usa os segmentos depois dessa mensagem.

## Threads

Prioridade no Zephyr: número menor ganha. Pilhas medidas (ver [Pilhas](#pilhas)).

| Thread | Arquivo | Prioridade | Pilha | Acorda com | Faz |
|---|---|---|---|---|---|
| `sensors` | `src/svc/sensors/sensors_svc.c` | 4 | 2048 B | a cada 20 ms | acelerômetro a 50 Hz com média de 1 s, barômetro a 10 Hz, magnetômetro e luz a 1 Hz, como o legacy (`fxos.cpp:600`, `Attitude.cpp`) |
| `model` | `src/svc/model/model_svc.c` | 5 | 4096 B | caixa de entrada; ao menos 1 vez por segundo | o único escritor do modelo: `attitude` e o Kalman, segmentos, zonas, percurso, máquina de modos; publica o retrato da tela e o ponto do log |
| `gnss` | `src/svc/gnss/gnss_svc.c`, `gnss_power.c` | 6 | 2048 B | caixa de entrada | máquina de energia do receptor (backup, aquisição, rastreio; LEAP e plena só com o M10), configura o receptor por UBX, publica a época e segue o modo e o desligamento |
| `radio` | `src/svc/radio/radio_svc.c` | 6 | 3072 B | caixa de entrada | sobe o ANT (com `ANT=1`) e o BLE, liga os clientes aos canais, atualiza o nível da bateria no BLE |
| `ui` | `src/svc/ui/ui_svc.c` | 7 | 6144 B | caixa de entrada, o próximo timer do LVGL; ao menos 1 vez por segundo | a única que chama o LVGL: telas do retrato, teclas, notificações, telas de USB e de desligamento, luz e COM; o driver manda ao painel só as linhas que mudaram |
| `storage` | `src/svc/storage/storage_svc.c` | 8 | 3584 B | caixa de entrada | monta o cartão, carrega segmentos, lista percursos, grava o log de atividade |
| `usb` | `src/svc/usb/usb_svc.c` (só no alvo com pilha USB) | 8 | 2048 B | caixa de entrada; tique de 1 s | liga o USB quando o cabo entra: porta serial com os comandos do legacy e, no modo USB, o disco do ciclista no PC; a interrupção do CDC só enfileira bytes |
| `power` | `src/svc/power/power_svc.c` | 9 | 3072 B | caixa de entrada; tique de 1 s; o medidor e o carregador a cada 10 s; eventos do nPM1300 | máquina de sistema, desligamento automático, ship mode ou System OFF; lê o medidor e o carregador e publica `power_status`; bateria fraca e crítica (`battery.c`); estado da carga (`charge.c`) |
| workqueue do modem | Zephyr (`CONFIG_MODEM_DEDICATED_WORKQUEUE`) | do sistema | 2048 B | bytes do receptor | o driver GNSS interpreta e chama os callbacks do serviço: a época vai para a caixa de entrada da thread `gnss`, que a publica, e os satélites saem em `gnss_sky` dali mesmo |
| RX do BT | Zephyr | cooperativa | 3072 B | pacotes do rádio | os clientes BLE chamam os callbacks do serviço de rádio, que publicam `ext_sensor` e `link_status` |
| entrada | Zephyr (`CONFIG_INPUT_THREAD_STACK_SIZE`) | 0 | 2048 B | eventos das teclas | o `zephyr,input-longpress` separa toque curto e longo; o callback de `src/svc/ui/ui_input.c` publica `input` |
| workqueue do sistema | Zephyr | do sistema | 2048 B | trabalhos | o debounce das teclas, os eventos do nPM1300 (o driver lê os registradores e chama o callback do serviço, que só põe a mensagem na caixa) e, na V3, o VCOM serial da tela |

Ficam por conta do Zephyr e do NCS: o log, o TX do BT, o MPSL e o idle.

## Eventos

Cada serviço tem uma **caixa de entrada**, uma `k_msgq` estática que um listener do zbus enche com cópias das mensagens que o serviço usa (`ZBUS_CHAN_ADD_OBS()` no arquivo do serviço). A thread dorme na caixa com um tempo máximo de 1 s, que também dá o trabalho periódico e a alimentação do watchdog (`app_inbox_get()`). Assim nenhum evento se perde entre dois processamentos, nada é alocado depois do boot, e cada thread tem um ponto só de espera. O retrato da tela e as listas grandes (satélites, pareamento, cartão) não vão na caixa: o listener só avisa, e a thread lê o canal. Com a caixa cheia, a mensagem é descartada e contada no log.

| Canal | Mensagem | Publica | Escutam |
|---|---|---|---|
| `chan_gnss_fix` | posição, velocidade, rumo, altitude, hora UTC, satélites, modo do receptor, uma por época | thread `gnss` | modelo, energia |
| `chan_gnss_sky` | satélites em vista | callback do GNSS | modelo |
| `chan_baro` | pressão e temperatura, 10 Hz | sensores | modelo |
| `chan_imu` | inclinação, rolagem e rugosidade, 1 Hz | sensores | modelo |
| `chan_mag` | rumo magnético compensado, 1 Hz | sensores | modelo |
| `chan_ambient` | luz ambiente, 1 Hz | sensores | interface |
| `chan_ext_sensor` | um dado de sensor externo | rádio | modelo, energia |
| `chan_link_status` | sensor conectado, perdido, procurando ou sem par | rádio | modelo |
| `chan_pair_list` | dispositivos achados no pareamento | rádio | modelo |
| `chan_phone_nav` | próxima curva do celular | rádio | modelo |
| `chan_power_status` | bateria e carga, a cada 60 s e quando muda | energia | modelo, rádio |
| `chan_system_cmd` | os pedidos da interface (modo, desligar, parear, FTP, zoom, formatar, MSC) | interface e serviços | cada serviço filtra os seus |
| `chan_system_state` | Partida, Ligado, MSC, Desligando, Desligado | energia | todos |
| `chan_mode` | modo em vigor | modelo | energia, GNSS, interface |
| `chan_shutdown_ack` | um serviço terminou a sua parte do desligamento | serviços | energia, interface (progresso na tela) |
| `chan_notif` | notificação da tela | qualquer um | interface |
| `chan_log_point` | um ponto do log por época | modelo | armazenamento |
| `chan_input` | tecla e tipo de toque | callback das teclas, na thread da entrada | interface |
| `chan_storage_info` | cartão montado, segmentos carregados, percursos | armazenamento | modelo |
| `chan_model_state` | o retrato da tela (`ui_model_t`, [18](18-interface-telas.md#implementação)) | modelo | interface |
| `chan_dfu` | fase e porcentagem da atualização por BLE ([07](07-radio-ant-ble.md#atualização-por-ble-dfu)) | rádio | interface |

As mensagens estão em `zephyr_app/include/app/app_events.h`, em C sem tipos do Zephyr.

## Máquinas de estado

| Máquina | Arquivo | Estados | Teste |
|---|---|---|---|
| Sistema e energia | `src/svc/power/sys_fsm.c` | Partida, Ligado e MSC sob um pai comum que aceita o desligamento; Desligando espera a resposta de cada serviço por até 5 s; Desligado corta a energia (ship mode do nPM1300 sem VBUS, System OFF com VBUS ou sem PMIC) | `test_sys_fsm` (16 casos), com o `lib/smf/smf.c` do Zephyr |
| Modo | `src/model/mode_fsm.c`, chamada pelo `src/svc/model/model_svc.c` | CRS, PRC, FEC, Zwift, DBG, com as entradas e saídas de `boucle__change_mode()` (`legacy/source/model/Boucle.cpp:101-143`): PRC inicia o percurso carregado e o para ao sair, FEC zera as zonas e o score | `test_mode_fsm` (22 casos) |
| Carga | `src/svc/power/charge.c` | Bateria, Solar, USB, USB cheia, Pausa térmica, Falha, lidos do nPM1300 e do AEM10900 a cada evento e a cada 10 s: com VBUS, o hardware bloqueia o solar | `test_charge` (11 casos) |
| Luz da tela | `src/svc/ui/backlight.c` | Apagada, Temporária (10 s depois de uma tecla) e Automática (pouca luz ambiente, com histerese entre 20 e 50 lux); desligada pelo menu, nada a acende; limites a acertar na bancada | `test_backlight` (11 casos) |

O desligamento automático é o do legacy (`legacy/source/scheduling/power_scheduler.cpp`): cada posição com fix em CRS, PRC e DBG, e cada dado do rolo em FEC, reinicia a contagem de 15 min (`src/model/power_scheduler.c`, `test_power_scheduler`). Diagramas das máquinas em [16](16-arquitetura-firmware.md#máquinas-de-estado).

## Watchdog

O `task_wdt` do Zephyr dá a cada thread de serviço o seu canal de 4 s, o tempo do WDT do legacy (que tinha um canal só, alimentado pelo `boucle` e pelo LCD). São 8 canais em uso, um por serviço, de 10 reservados (`CONFIG_TASK_WDT_CHANNELS=10`); o WDT do nRF fica por trás e pega um travamento em que nem o timer do kernel roda.

- Cada thread alimenta o seu canal antes de cada espera na caixa, e a espera dura no máximo 1 s: um serviço preso num evento por mais de 4 s reinicia o aparelho, com o nome dele no log (`LOG_PANIC` no expirar).
- O armazenamento carrega os segmentos antes de criar o seu canal, porque a carga pode passar de 4 s com muitos arquivos no cartão.
- `CONFIG_TASK_WDT_MIN_TIMEOUT=4000`: o timer do kernel não acorda a CPU a cada 100 ms só para alimentar o WDT.
- O WDT do nRF52 continua contando depois de um `sys_reboot()`: o `main()` o alimenta (`app_wdt_feed_if_running()`) até os canais existirem. O WDT é o `watchdog0` do devicetree (`wdt0` no nRF52840, `wdt31` no nRF54LM20).
- O timer do kernel não pausa num breakpoint: para depurar passo a passo, compile com `-DCONFIG_TASK_WDT=n`.
- Não testado na placa.

## Fluxo de dados

```mermaid
flowchart LR
    RX["receptor GNSS"] -->|"API GNSS<br/>workqueue do modem"| GS["callbacks do gnss_svc"]
    SEN["barômetro, IMU,<br/>magnetômetro, luz"] -->|"API de sensores"| SS["sensors_svc<br/>tilt: 50 amostras"]
    BLEC["clientes BLE e ANT"] --> RS["radio_svc"]
    GS -->|"gnss_fix, gnss_sky"| MOD["model_svc<br/>attitude, Kalman, segmentos,<br/>zonas, percurso"]
    SS -->|"baro, imu, mag"| MOD
    RS -->|"ext_sensor, link_status"| MOD
    MOD -->|"model_state"| UI["ui_svc<br/>LVGL e luz"]
    KEY["botões<br/>gpio-keys e longpress"] -->|"input"| UI
    UI -->|"system_cmd"| MOD
    UI --> DRVM["driver memlcd<br/>quantiza e manda<br/>as linhas que mudaram"]
    DRVM --> PAN[("painel")]
    MOD -->|"log_point"| ST["storage_svc<br/>sd_logger"]
    ST --> FS[("FatFs no cartão")]
    ST -->|"storage_info"| MOD
    GS -->|"gnss_fix"| PW["power_svc<br/>máquina de sistema"]
    RS -->|"ext_sensor"| PW
    PW -->|"system_state"| MOD
    PW -->|"power_status"| MOD
```

## Pilhas

Medidas com `CONFIG_STACK_USAGE=y` (arquivos `.su` do GCC) em 2026-09-19, no build do nRF54LM20 DK. A soma segue a cadeia de chamadas mais funda e acrescenta o quadro de exceção com FPU (~100 B) e uma chamada de log (~250 B).

| Thread | Cadeia mais funda | Total | Pilha | Folga |
|---|---|---|---|---|
| `model` | `model_thread` 392 + `attitude_update_baro` 104 + **`measurement_update` 1672** + `udmat_invert` 352; o alocador de segmentos, que abre o arquivo do cartão na mesma thread, é mais raso: `segment_run_allocator` 32 + `segment_allocator` 616 (com o `load_segment_points` embutido) + FatFs e SD por SPI ~0,7 KB | ~2,9 KB | 4096 B | ~1,2 KB |
| `storage` | `storage_thread` 416 + `segment_load_all` 656 + FatFs (`f_open` 96, `follow_path` 56, `dir_find` 64) + SD por SPI (`sdhc_spi_request` 136, `sdhc_spi_send_cmd` 56, `spi_nrfx_transceive` 128) | ~2,2 KB | 3584 B | ~1,4 KB |
| `radio` | `bt_enable` 24 + `bt_init` 168 + `bt_hci_cmd_send_sync` 96 + `settings_zms_load` 144 e o ZMS | ~1,5 KB | 3072 B | ~1,5 KB |
| `sensors` | `sensors_thread` 168 + leitura I2C (`i2c_nrfx_twim_msg_transfer` 56) + publicação no zbus (`zbus_chan_pub` 56, `_zbus_vded_exec` 104, listener até 80, `k_msgq_put`) | ~0,9 KB | 2048 B | ~1,1 KB |
| `usb` | `usb_thread` 72 + `cdc_process` 56 + `cmd_parser_feed` 24 + `app_cmd_handle` 112 + publicação no zbus (~0,35 KB) + log (~0,3 KB); o caminho de ligar o barramento é mais raso (`usb_go` 56 + as funções do stack, todas abaixo de 120 B) | ~0,9 KB | 2048 B | ~1,1 KB |
| `power` | `power_thread` 40 + `read_gauge` 64 + bateria crítica pela máquina de sistema (`smf_set_state` 64, `shutdown_entry` 16) + publicação no zbus (`app_publish` 56, `zbus_chan_pub` 56, `_zbus_vded_exec` 104, listener até 80, `app_inbox_put` 56) + log (~0,3 KB); a leitura I2C do medidor fica em ~0,3 KB | ~1,1 KB | 3072 B | ~1,9 KB |
| `gnss` | `gnss_thread` 136 + `apply` 24 + `ublox_m10_configure` 24 + `valset` 32 + `ubx_m10_valset` 48 + `run_script` 32 + `modem_ubx_run_script` 40, ou a publicação no zbus (`zbus_chan_pub` 56, `_zbus_vded_exec` 104, listener até 80, `app_inbox_put` 56) + log | ~0,6 KB | 2048 B | ~1,4 KB |
| `ui` | `ui_thread` 136 + `lv_timer_handler` 40 + `lv_display_refr_timer` 144 + `refr_area` 88 + 4 níveis da árvore de objetos × (`lv_obj_refr` 272 + `lv_obj_redraw` 352) + evento de desenho ~0,3 KB + arco (`ui_draw_disc` 200, `lv_draw_arc` 128, `lv_draw_sw_arc` 600, máscara e mistura ~0,4 KB) | ~4,7 KB | 6144 B | ~1,4 KB |
| entrada | `input_thread` 40 + `ui_keys_cb` 16 + publicação no zbus (`zbus_chan_pub` 56, `ui_listener` 80, `app_inbox_put` 56) + log | ~0,9 KB | 2048 B | ~1,1 KB |
| workqueue do sistema | VCOM serial da V3: `com_work_handler` 16 + `send_mode` 32 + `spi_nrfx_transceive` 128 + `nrfx_spim_xfer` 40 + espera + log; no nRF54LM20, os eventos do nPM1300: `work_callback` 104 + leitura I2C + `pmic_event` 16 + `app_inbox_put` 56 + log, ~0,7 KB | ~1,0 KB | 2048 B | ~1,0 KB |
| workqueue do modem | UBX no nRF54LM20 (`modem_ubx_process_handler` 48 + `pvt_handler` 144 + `ubx_m10_parse_pvt` 16 + `gnss_publish_data` 24 + `gnss_data_cb` 64 + `app_inbox_put`), ou os satélites, que publicam no zbus de lá (`sat_handler` 40, `zbus_chan_pub` 56, `_zbus_vded_exec` 104, listener até 80); com NMEA, `modem_chat_process_handler` 64 e `gnss_nmea0183_parse_rmc` | ~0,7 KB | 2048 B | ~1,3 KB |
| `main` | `settings_zms_save` 144 e o ZMS, ou `zms_mount` 232, com log | ~0,8 KB | 2048 B | ~1,2 KB |

- O workqueue do sistema, de 1024 B, ficaria com ~170 B de folga com os callbacks do GNSS: por isso o modem ganhou workqueue próprio. Com o VCOM serial da tela (V3), o workqueue do sistema subiu para 2048 B.
- A thread RX do BT subiu de 2200 para 3072 B, pelos ~0,45 KB que a publicação dos clientes acrescenta.
- O desenho do LVGL é recursivo: cada nível da árvore de objetos (tela, célula, campo, rótulo) custa 624 B. O log interno do LVGL fica desligado no firmware, porque `lv_log_add()` sozinho tem 848 B de quadro e cairia no fundo dessa cadeia; o renderizador de host o mantém ligado.
- No PC, o renderizador de host mede a pilha das telas pintando-a: 7.359 B em x86-64 (ponteiros de 8 B e 32 B de sombra por chamada no Windows), cota superior do que o Cortex-M33 gasta ([12](12-ferramentas-testes.md#renderizador-de-telas)).
- Na placa, confirme com `CONFIG_THREAD_ANALYZER=y`.

```sh
source tools/fw/ncs_env.sh
cd zephyr_app
python -m west build -p always -b nrf54lm20dk/nrf54lm20a/cpuapp -d build_su --no-sysbuild . -- -DCONFIG_STACK_USAGE=y
find build_su -name "*.su" -exec cat {} + | sort -t$'\t' -k2 -rn | head -40
```

## Tela

O driver de `modules/gnss_drivers/drivers/display/memlcd.c` atende os painéis de memória de 2,7" pela API de tela do Zephyr ([18](18-interface-telas.md#framework)). O Zephyr do NCS não tem driver para o LPM027M128B (o `jdi,lpm013m126` limita a tela a 255 px e usa outro cabeçalho), e o `sharp,ls0xx` não gira a tela.

```mermaid
flowchart LR
    LV["LVGL<br/>áreas em RGB565<br/>240 × 400"] -->|"display_write"| BL["memlcd_frame_blit<br/>gira 90°, quantiza,<br/>marca as linhas"]
    BL --> FB[("quadro no formato do fio<br/>JDI 36.482 B · Sharp 12.482 B")]
    LV -->|"último pedaço do quadro"| TX["send_frame<br/>trechos de linhas seguidas<br/>num envio SPI"]
    FB --> TX
    TX --> PNL["painel"]
    COM["COM: EXTCOMIN por timer<br/>ou VCOM serial"] --> PNL
```

| Item | Como funciona | Fonte |
|---|---|---|
| Retrato | o LVGL desenha 240 × 400; o ponto (x, y) vai para a coluna y da linha 239 − x, como o `drawPixel()` da V3 com `setRotation(3)` | [08](08-interface.md#pipeline-de-desenho) |
| Cores | cada pixel RGB565 passa pela regra de [18](18-interface-telas.md#implementação) (`memlcd_pixel.h`, a mesma do renderizador de host): 8 cores no JDI; preto e branco na Sharp, com a cor pela luminância | `memlcd_rgb565_to_rgb3()`, `memlcd_rgb565_to_mono()` |
| Quadro | cada linha fica na memória com os bytes de endereço em volta dos pixels; um trecho de linhas seguidas vai num buffer só do SPI, até 16 trechos por quadro (com mais, o último cresce sobre a lacuna) | `memlcd_frame.h` |
| JDI | SPI com o bit mais significativo primeiro; por linha, 6 bits de modo (M0 alto, 3 bits por pixel) e 10 de endereço (linha 1 a 240), 150 B de pixels em vermelho, verde e azul; 16 clocks no fim; all clear com M2 | ficha do LPM027M128B, 6.2, 6.8 e 8 |
| Sharp | SPI com o bit menos significativo primeiro; byte de modo, e por linha o endereço, 50 B (1 é branco) e um byte vazio; mais um byte no fim | ficha do LS027B7DH01, 6-5 |
| COM | com `extcomin-gpios`, um timer do kernel troca o pino (cada subida inverte o COM); sem ele, o bit M1 vai num comando pelo SPI a cada inversão. Inversões por segundo: `extcomin-frequency` na partida, 1 a 20 na Sharp e 1 a 140 no JDI por `memlcd_set_com_hz()` | fichas: JDI 4.2 e 7; Sharp 6-3 |
| Partida | alimentação (`power-gpios`), all clear, 2 ms, COM; o DISP sobe no `display_blanking_off()`, com 200 µs para as travas e a polaridade do COM | JDI 4.3; Sharp 6-2 |
| Desligamento | `memlcd_power_off()`: all clear, DISP baixo, 50 µs, COM parado, alimentação cortada | JDI 4.3 (T5 a T7) |
| Chip select | ativo alto; atrasos em volta dele pelo devicetree (`spi-cs-setup-delay-ns`, `spi-cs-hold-delay-ns`) | JDI 4.2; Sharp 6-3 |

- O JDI com DISP baixo mostra preto e guarda a memória (ficha, 1.4); a Sharp apaga.
- Teste de host: `test_memlcd` (19 casos) confere a quantização, a rotação, o empacotamento de cada painel, o formato do quadro (12.482 B da Sharp, os 10 bits de endereço do JDI), as linhas marcadas e os trechos ([12](12-ferramentas-testes.md#testes-de-host-do-port)).
- Não testado em painel: SPI, COM, tempos e cores ficam para a bancada.

## Medidor de bateria

O MAX17262 da placa nova é lido pela API de fuel gauge do Zephyr, com um driver próprio (`modules/gnss_drivers/drivers/fuel_gauge/max17262.c`, compatível `adi,max17262`). O driver da árvore do Zephyr (`maxim,max17262`, API de sensores) grava a capacidade em mAh onde o registrador conta 0,5 mAh, põe a corrente de carga no `IChgTerm`, que pede a corrente de fim de carga, em passos crus, devolve capacidades sem o fator de 0,5 mAh e lê o tempo até vazio com sinal, de modo que 0xFFFF (desconhecido) nunca é reconhecido.

| Item | Como funciona | Fonte |
|---|---|---|
| Configuração | depois de cada reset do medidor (`Status.POR`): espera `FStat.DNR`, sai da hibernação, grava `DesignCap`, `IChgTerm`, `VEmpty` e `ModelCfg`, espera o `Refresh`, volta a hibernação, zera o `ETHRM` quando não há termistor e limpa o `POR` | ficha do MAX17262 e o guia do ModelGauge m5 EZ |
| Célula | 2000 mAh, fim de carga em 60 mA (10 % dos 600 mA do nPM1300), 4,2 V, vazio em 3,3 V e religamento em 3,88 V (os valores de fábrica) | [14](14-hardware-placa-nova.md#carga) |
| Leituras | tensão, corrente média, carga (`RepSOC`), temperatura do chip, tempo até vazio e até cheio, capacidades, ciclos, nas unidades da API | `max17262_regs.h`, `test_max17262` (10 casos) |
| Serviço | a thread `power` lê a cada 10 s, publica `power_status` quando algo da tela muda ou a cada 60 s, avisa bateria fraca e pede o desligamento com a bateria no fim ([06](06-algoritmos.md#bateria)) | `battery.c`, `test_battery` (10 casos) |

- Não testado com o medidor: a configuração, os tempos de espera e as leituras ficam para a bancada, com a placa de avaliação do MAX17262 no `i2c24` do DK.

## Carregador

O nPM1300 usa os drivers do Zephyr (MFD, reguladores e o carregador pela API de sensores), com a configuração de [14](14-hardware-placa-nova.md#alimentação) no devicetree.

| Item | Como funciona | Fonte |
|---|---|---|
| Trilhos | BUCK1 travado em 1,8 V (o V_IO do GNSS tem máximo absoluto de 1,98 V) e ligado na partida; BUCK2 travado em 3,0 V e sempre ligado (o MCU); LDO1 como chave do cartão, ligada; LDO2 como LDO de 3,3 V da luz, ligado só com a luz acesa pela thread `ui` | [14](14-hardware-placa-nova.md#árvore) |
| Carga | 600 mA, fim em 4,20 V e em 10 % da corrente (60 mA, o `IChgTerm` do medidor), NTC de 10 kΩ B3380 com os limites JEITA de fábrica | [14](14-hardware-placa-nova.md#carga) |
| VBUS | 500 mA na partida; quando o VBUS chega, o serviço lê o que a fonte USB-C oferece pelo CC (500 mA ou 1,5 A) e sobe o limite, que o nPM1300 volta ao padrão quando o cabo sai; o VBUS vai para a máquina de sistema, que escolhe ship mode ou System OFF | ficha do nPM1300; amostras `npm13xx_*` do NCS |
| Eventos | VBUS entrou e saiu, carga completa e erro do carregador: o driver do MFD os recebe pelo GPIO3 e chama o callback no workqueue do sistema, que só põe uma mensagem na caixa da thread `power` | `mfd_npm13xx_add_callback()` |
| Estado | `charge.c` junta o `BCHGCHARGESTATUS`, o `BCHGERRREASON`, o `VBUSINSTATUS` e o `NTCSTATUS` do nPM1300 com o estado do AEM10900 e dá o estado da [máquina de carga](16-arquitetura-firmware.md#carga); pausa térmica e falha viram notificação | `test_charge` (11 casos) |
| Solar | driver próprio do AEM10900 (`modules/gnss_drivers/drivers/charger/aem10900.c`, compatível `e-peas,aem10900`, API de carregadores do Zephyr): na partida confere o número da peça, passa à configuração por I2C para carregar até 4,05 V (os pinos carregam até 3,90 V; os demais registradores ficam no valor de fábrica, que é o dos pinos) e liga o monitor de potência (APM); a thread `power` lê a cada 10 s se o painel carrega, a potência e o limiar em vigor, e devolve o AEM aos pinos antes de cortar a energia; se o AEM reinicia e volta aos pinos, o driver grava a configuração de novo | ficha do AEM1090x, seções 6 e 9; `aem10900_regs.h`, `test_aem10900` (7 casos) |

- O LED de carga do nPM1300 (LED1) acende sozinho, sem firmware ([14](14-hardware-placa-nova.md#componentes-principais)); o devicetree não mexe nos LEDs.
- A potência do painel em mW depende do produto θ·L da seção 9.13 da ficha do AEM1090x, que a e-peas informa para cada aplicação: até lá, `apm-scale-pj` fica em 0, a tela mostra 0 mW e só o estado Solar diz que o painel carrega.
- Não testado com o nPM1300 nem com o AEM10900: as placas de avaliação ligam no `i2c24` do DK, com a interrupção do nPM1300 em P0.04.

## Módulos

| Pasta | Arquivos | Papel |
|---|---|---|
| `src/app/` | `main.c`, `app_channels.c`, `app_svc.c` | boot, canais, watchdog e caixas de entrada |
| `src/svc/power/` | `power_svc.c`, `sys_fsm.c`, `battery.c`, `charge.c` | serviço de energia, máquina de sistema, bateria fraca e crítica, estado da carga |
| `src/svc/gnss/` | `gnss_svc.c`, `gnss_power.c` | receptor pela API GNSS do Zephyr e a máquina de energia dele |
| `src/svc/sensors/` | `sensors_svc.c`, `tilt.c` | sensores pela API de sensores; inclinação, rumo e rugosidade |
| `src/svc/radio/` | `radio_svc.c` | ANT e BLE, clientes para eventos |
| `src/svc/storage/` | `storage_svc.c` | cartão, log, segmentos, percursos |
| `src/svc/model/` | `model_svc.c`, `model_ui.c` | a thread do modelo e o retrato da tela |
| `src/svc/ui/` | `ui_svc.c`, `ui_input.c`, `backlight.c` | a thread da tela; as teclas para o zbus; a máquina de estado da luz ([16](16-arquitetura-firmware.md#luz-do-display)) |
| `src/model/` | `activity`, `alerts`, `attitude`, `climb`, `cmd_parser`, `cps_parse`, `crash_recovery`, `csc_calc`, `dfu_state`, `distance`, `file_policy`, `fit_encode`, `ftms_parse`, `gpx_scan`, `incident`, `kalman_altitude`, `komoot_turn`, `liste_points`, `lns_parse`, `loc_arbiter`, `map_project`, `mode_fsm`, `notif_filter`, `parcours`, `power_estimate`, `power_metrics`, `power_scheduler`, `power_zone`, `qry`, `radar`, `radar_wire`, `route_file`, `route_profile`, `rr_zone`, `sd_logger`, `segment`, `segment_file`, `suffer_score`, `udmatrix`, `user_settings`, `vecteur`, `workout` | os algoritmos do legacy e os que o port acrescentou, em C puro, sem Zephyr, para o teste de host rodar no PC |
| `src/rf/` | `ble/ble_manager.c`, `ble/ble_nus.c`, `ble/ble_lns.c`, `ble_hrs_client.c`, `ble_bsc_client.c`, `ble_fec_client.c`, `ble_cps_client.c`, `ble_lns_client.c`, `ble_ancs_client.c`, `ble_komoot_client.c`, `ble_radar_client.c`, `dfu.c`, `file_xfer.c`, `ant/ant.c`, `ant/ant_channel.c`, `ant/ant_sensors.c`, `ant/power_ant.c`, `ant/radar_ant.c` | BLE, que anuncia e varre desde 2026-09-20 (`src/svc/radio/radio_svc.c` sobe os dois e registra os clientes), mais a atualização por BLE e o envio de arquivos; e o ANT, só com `ANT=1` e sem nenhum canal aberto de fato ([07](07-radio-ant-ble.md#rádio-no-port)) |
| `src/ui/`, `include/ui/` | interface LVGL da placa nova ([18](18-interface-telas.md)) | a mesma no firmware e no renderizador de host (`tests/ui`) |
| `modules/gnss_drivers/` | `drivers/display/memlcd.c`, `memlcd_frame.c`, `include/drivers/display/memlcd*.h`, `drivers/fuel_gauge/max17262.c`, `include/drivers/fuel_gauge/max17262_regs.h`, `drivers/charger/aem10900.c`, `include/drivers/charger/aem10900*.h`, `drivers/gnss/gnss_ublox_m10.c`, `ubx_m10.c`, `include/drivers/gnss/ub*_m10.h`, `dts/bindings/` (com o prefixo `e-peas` em `vendor-prefixes.txt`) | drivers próprios num módulo do Zephyr dentro da aplicação: a tela ([Tela](#tela)), o medidor MAX17262 ([Medidor de bateria](#medidor-de-bateria)), o carregador solar AEM10900 ([Carregador](#carregador)) e os receptores u-blox F10 e M10 ([Receptor GNSS](#receptor-gnss)) |

Saíram em 2026-09-19, substituídos pelas APIs do Zephyr ou pelos serviços: o HAL próprio (`src/hal`), os drivers da V3 (`ls027`, `baro`, `fxos`, `stc3100`, `gps_mgmt`, `nmea_parser`, `gps_epo`, `neopixel`), a interface em paisagem (`src/vue`), a USB da pilha antiga (`src/usb`), os stubs do sistema de arquivos (`src/utils`), o `boucle`, o `model_lock`, o `zwift` (protocolo próprio, não o do legacy) e o `baro_drift` (duplicado).

Saíram em 2026-09-21, porque ninguém os lia: `model/kalman.c` (o filtro de posição; o de altitude, `kalman_altitude.c`, ficou e é usado), `model/locator.c` e `model/loc_source.c`. O árbitro de fontes de posição que o `loc_source.c` prometia virou `model/loc_arbiter.c`, esse sim chamado pelo `model_svc.c` ([06](06-algoritmos.md#fontes-de-posição)).

## Receptor GNSS

O **MAX-F10S** da placa nova fala UBX, e o Zephyr do NCS v3.3.0 não tem driver do M10 nem do F10: o do M8 configura pelas mensagens `UBX-CFG-*` antigas, que nenhum dos dois aceita, e o do F9P é um receptor RTK. O `u-blox,m10` que entra no Zephyr 4.5 também não serve ao F10. O port traz o seu, em `modules/gnss_drivers/drivers/gnss/`, sobre a camada UBX do Zephyr (`modem_ubx` num pipe de UART).

Um driver só atende as duas peças do footprint MAX: o **MAX-F10S** de banda dupla (`u-blox,max-f10`), que a placa leva, e o **MAX-M10N-10B** de banda única (`u-blox,max-m10`), a alternativa econômica. Os quadros e as chaves da UART, da taxa, do modelo dinâmico e da saída de mensagens têm os mesmos IDs nas duas firmwares.

| Parte | O que faz | Onde |
|---|---|---|
| Protocolo | `ubx_m10.c` monta e lê os quadros em C puro, sem Zephyr: cabeçalho, checksum de Fletcher de 8 bits, `UBX-CFG-VALSET` de uma chave e de um lote (`ubx_m10_valset_many()`), `VALGET` (o tamanho do valor sai dos bits 30 a 28 da chave), `UBX-RXM-PMREQ`, `UBX-CFG-RST`, `UBX-NAV-PVT` e `UBX-NAV-SAT` | fichas "u-blox F10 SPG 6.00 Interface description" (UBX-23002975 R02) e "u-blox M10 SPG 5.30" (UBXDOC-304424225-20395), seções 3.2, 3.4, 3.10, 3.14/3.15 e 3.16; `test_ubx_m10` (24 casos) |
| Driver | `gnss_ublox_m10.c` liga o pipe, trata as mensagens espontâneas e atende a API GNSS do Zephyr (taxa, modelo dinâmico, constelações) | `u-blox,max-f10` e `u-blox,max-m10` no devicetree |
| Configuração | protocolos do UART em UBX, NMEA desligado (14 chaves), `UBX-NAV-PVT` e `UBX-NAV-SAT` a cada época, taxa de 1 Hz, modelo `portable`, pulso de tempo desligado; no M10, também o modo LEAP; tudo nas camadas RAM **e** BBR | o standby apaga a RAM do receptor (manual de integração 3.7.4.2), e a BBR, que o V_BCKP segura, devolve a configuração |
| Sinais (só F10) | um `UBX-CFG-VALSET` com as nove chaves de L1, L5 e NavIC: `GPS_L1CA`, `GPS_L5`, `GAL_E1`, `GAL_E5A`, `BDS_B1C`, `BDS_B2A`, `SBAS_L1CA`, `NAVIC_ENA` e `NAVIC_L5`. NavIC só liga com a propriedade `navic` do devicetree | toda escrita em `CFG-SIGNAL` reinicia o subsistema GNSS: um quadro só custa um reinicio, e o driver espera 0,5 s depois do reconhecimento (UBX-23002975 R02, 4.9.20) |
| Bandas (só F10) | L1 e L5 juntos, sempre: "Single-band operation is not supported" (ficha do MAX-F10S, 1.3). Nada a escolher no devicetree | o GPS L5 sai ligado na firmware, mas os satélites ainda transmitem como não saudáveis e ficam fora da solução |
| Energia | `ublox_m10_standby()` manda `UBX-RXM-PMREQ` com backup e force e, se o nó tiver `vcc-supply`, corta o trilho; `ublox_m10_wake()` acorda pela linha RX. `ublox_m10_set_power_mode()` troca LEAP (`CFG-PM-OPERATEMODE` = 2) e potência plena **só no M10**: a firmware do F10 não tem o grupo `CFG-PM`, e a função devolve `-ENOTSUP` se alguém pedir LEAP | manual de integração do M10, 3.7.2 e 3.7.4.2; UBX-23002975 R02, 4.8 |
| Falhas | `ublox_m10_hw_reset()` puxa o RESET_N por 2 ms quando o receptor para de responder; sem o pino, `UBX-CFG-RST` | `legacy/source/sensors/GPSMGMT.cpp:143-176` reiniciava a UART |

- O receptor pode perder uma mensagem do host enquanto faz o ciclo do LEAP (manual de integração 3.7.2): toda configuração vai com 3 repetições, e o driver leva o receptor à potência plena antes de um lote. No F10 não há ciclo, mas as repetições ficam: elas também cobrem um quadro perdido na UART.
- Os callbacks do driver rodam no workqueue do modem e **não podem esperar resposta**: quem espera é a thread `gnss`, porque a resposta chega num item de trabalho desse mesmo workqueue. É também por isso que a espera de 0,5 s do `CFG-SIGNAL` mora na thread.
- O `hdop` publicado é o pDOP do `UBX-NAV-PVT` (o horizontal sozinho pediria o `UBX-NAV-DOP`, uma mensagem a mais por época), diferença registrada em [06](06-algoritmos.md#fontes-de-posição).
- Não testado com receptor nenhum: o DK não tem GNSS, e a placa de avaliação (EVK-F101-00) ainda não foi comprada.
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
