Guiimartinho/gnss-bike-computer/docs/08-interface.md

# Interface: telas, menus, botões e notificações

Como o stravaV10 original desenha as telas no Sharp Memory LCD, como os três botões navegam pelos modos e menus, e em que pé está a interface do port Zephyr. A interface em paisagem que o port teve até 2026-09-19 não traduzia a original e saiu. A interface da placa nova (LVGL, retrato, 8 cores ou preto e branco, com os arranjos do legacy), com todas as telas desenhadas e testadas no PC, está em [18-interface-telas.md](18-interface-telas.md).

**Nesta página:** [Display](#display) · [Interface original](#interface-original) · [Imagens](#imagens) · [Interface do port](#interface-do-port) · [Comparação](#comparação) · [O que falta](#o-que-falta)

## Display

| Item | Valor |
|---|---|
| Painel | Sharp Memory LCD LS027, 400 × 240 pixels, 1 bit por pixel, sem backlight |
| Montagem no aparelho | **retrato**: 240 de largura × 400 de altura (foto `img/front1.png`) |
| Interface | SPI a 2 MHz, LSB primeiro, CS ativo em nível alto |
| Buffer | 12.482 B: `[comando][endereço][50 B de pixels][dummy] × 240 linhas + [dummy]`; bit menos significativo = pixel da esquerda |
| VCOM | precisa alternar: o legacy alterna pelo bit M1 a cada envio; na V3, EXTMODE e EXTCOMIN vão ao GND por 10 kΩ (R13, R16) e o DISP ao VCC por 10 kΩ e 0,1 µF (R17, C43); a placa nova usa o EXTCOMIN ([18](18-interface-telas.md#atualização-e-luz)) |
| Refresh | legacy: por evento, cerca de 1 Hz; placa nova: a cada época do GNSS ou botão, só as linhas que mudaram |

O layout do buffer é o de `legacy/drivers/lcd/ls027.c:22-24`; o driver do port antigo, removido em 2026-09-19, usava o mesmo, e o driver novo (`memlcd`, [05](05-arquitetura-zephyr.md#tela)) guarda o quadro da Sharp nos mesmos 12.482 B.

## Interface original

### Pipeline de desenho

```mermaid
sequenceDiagram
    participant B as boucle_task
    participant L as ls027_task
    participant V as vue (Vue.cpp)
    participant D as LS027 (SPI)
    B->>L: cancela a espera a cada ciclo GPS/FEC
    Note over L: espera até 1250 ms (LS027_TIMEOUT_DELAY_MS)
    L->>L: bsp_tasks() (botões)
    L->>V: vue.refresh()
    alt menu aberto
        V->>V: tasksMenu()
    else menu fechado
        V->>V: tasksCRS / tasksFEC / tasksPRC / displayDebug
    end
    V->>V: sobrepõe a primeira notificação da fila
    L->>D: vue.writeWhole() = LS027_UpdateFull
```
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
