Guiimartinho/gnss-bike-computer/docs/17-dispositivos-ble-ant.md

# Dispositivos BLE e ANT+

Catálogo dos dispositivos externos que um computador de bordo de ciclismo encontra, com o protocolo de cada um (perfil ANT+ ou serviço BLE), o que o `sdk-ant` e o NCS já oferecem, a prioridade para o port e o que é fechado. O que o legacy usa e o mapa da API do `sdk-ant` estão em [07-radio-ant-ble.md](07-radio-ant-ble.md); a máquina de estado de cada sensor, em [16](16-arquitetura-firmware.md#sensor-externo).
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
