Guiimartinho/gnss-bike-computer/docs/telas/01_partida_cor.png

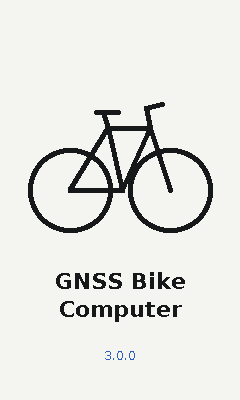
docs/telas/01_partida_cor.png
