Guiimartinho/gnss-bike-computer/docs/telas/02_crs1_cor.png

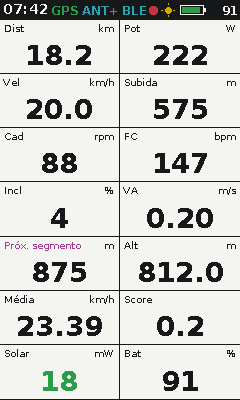
docs/telas/02_crs1_cor.png
