Guiimartinho/gnss-bike-computer/docs/telas/03_crs1_1seg_cor.png

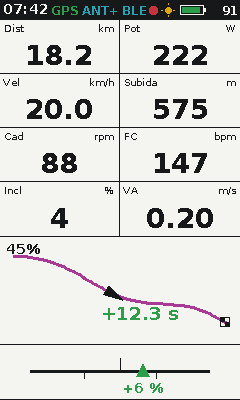
docs/telas/03_crs1_1seg_cor.png
