Guiimartinho/gnss-bike-computer/docs/telas/04_crs1_1seg_perto_cor.png

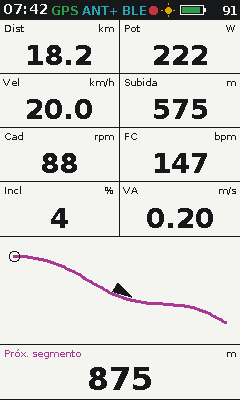
docs/telas/04_crs1_1seg_perto_cor.png
