Guiimartinho/gnss-bike-computer/docs/telas/05_crs1_2seg_cor.png

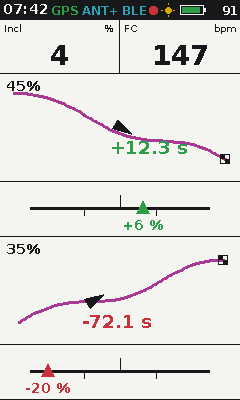
docs/telas/05_crs1_2seg_cor.png
