Guiimartinho/gnss-bike-computer/docs/telas/06_crs1_2seg_1perto_cor.png

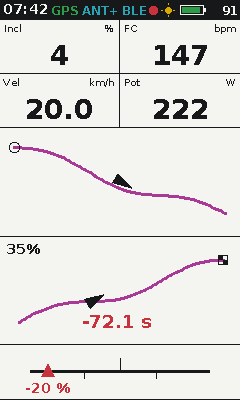
docs/telas/06_crs1_2seg_1perto_cor.png
