Guiimartinho/gnss-bike-computer/docs/telas/07_crs1_2seg_2perto_cor.png

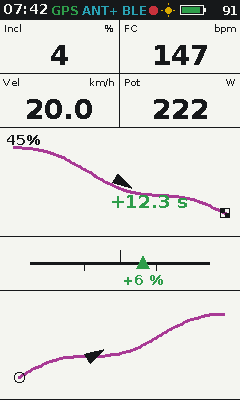
docs/telas/07_crs1_2seg_2perto_cor.png
