Guiimartinho/gnss-bike-computer/docs/telas/08_crs1_2seg_perto_cor.png

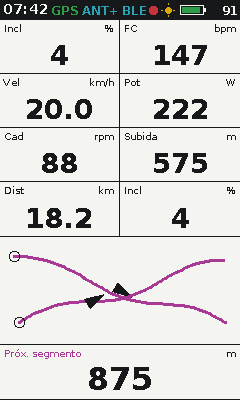
docs/telas/08_crs1_2seg_perto_cor.png
