Guiimartinho/gnss-bike-computer/docs/telas/09_crs2_cor.png

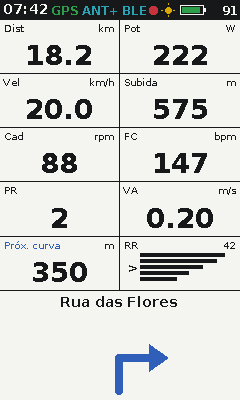
docs/telas/09_crs2_cor.png
