Guiimartinho/gnss-bike-computer/docs/telas/10_crs3_cor.png

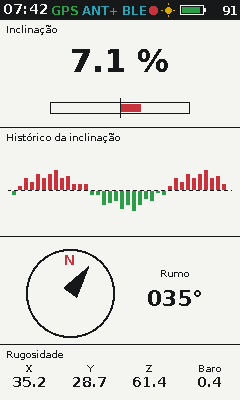
docs/telas/10_crs3_cor.png
