Guiimartinho/gnss-bike-computer/docs/telas/11_notificacao_cor.png

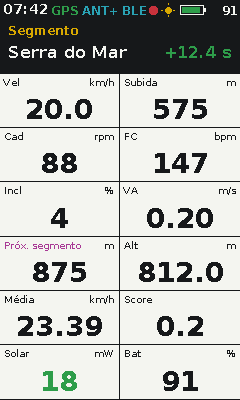
docs/telas/11_notificacao_cor.png
