Guiimartinho/gnss-bike-computer/docs/telas/12_gnss_cor.png

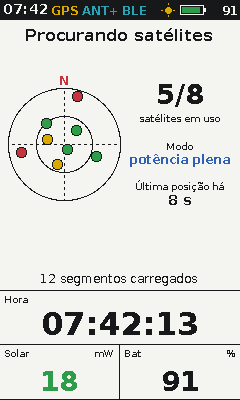
docs/telas/12_gnss_cor.png
