Guiimartinho/gnss-bike-computer/docs/telas/13_prc_cor.png

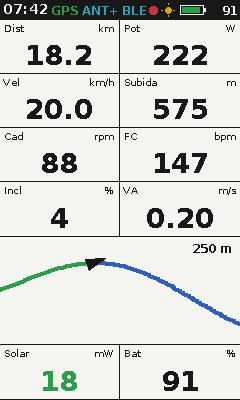
docs/telas/13_prc_cor.png
