Guiimartinho/gnss-bike-computer/docs/telas/15_fec_conectando_cor.png

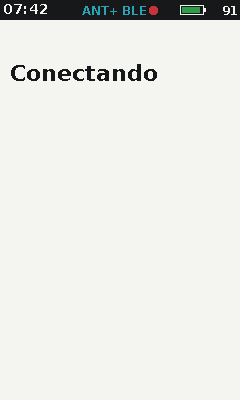
docs/telas/15_fec_conectando_cor.png
