Guiimartinho/gnss-bike-computer/docs/telas/16_fec_cor.png

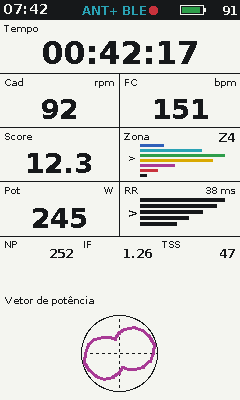
docs/telas/16_fec_cor.png
