Guiimartinho/gnss-bike-computer/docs/telas/17_dbg_cor.png

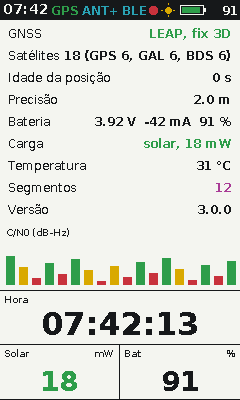
docs/telas/17_dbg_cor.png
