Guiimartinho/gnss-bike-computer/docs/telas/18_menu_cor.png

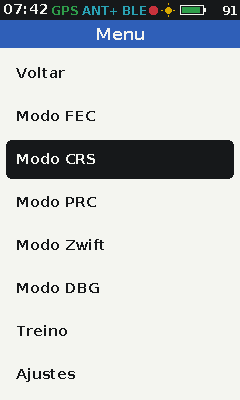
docs/telas/18_menu_cor.png
