Guiimartinho/gnss-bike-computer/docs/telas/18b_percursos_cor.png

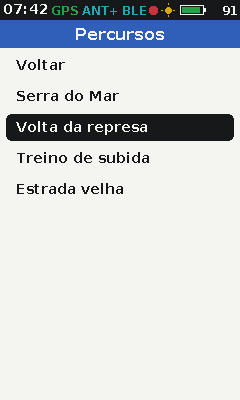
docs/telas/18b_percursos_cor.png
