Guiimartinho/gnss-bike-computer/docs/telas/18c_sem_percursos_cor.png

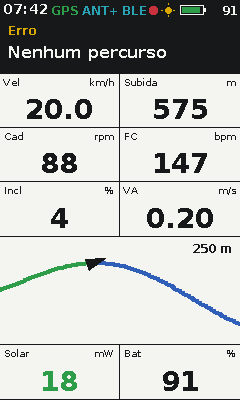
docs/telas/18c_sem_percursos_cor.png
