Guiimartinho/gnss-bike-computer/docs/telas/19_ajustes_cor.png

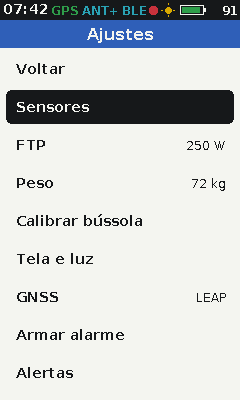
docs/telas/19_ajustes_cor.png
