Guiimartinho/gnss-bike-computer/docs/telas/20_sensores_cor.png

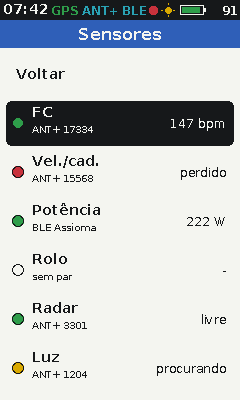
docs/telas/20_sensores_cor.png
