Guiimartinho/gnss-bike-computer/docs/telas/21_parear_cor.png

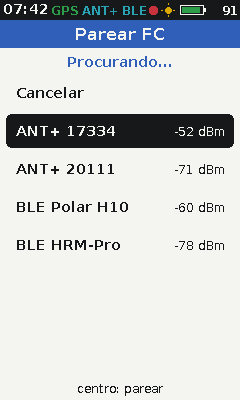
docs/telas/21_parear_cor.png
