Guiimartinho/gnss-bike-computer/docs/telas/22_valor_cor.png

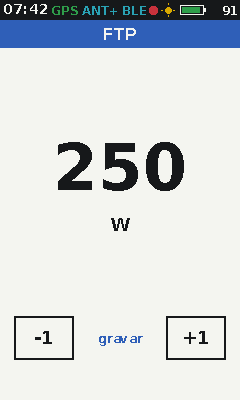
docs/telas/22_valor_cor.png
