Guiimartinho/gnss-bike-computer/docs/telas/23_tela_luz_cor.png

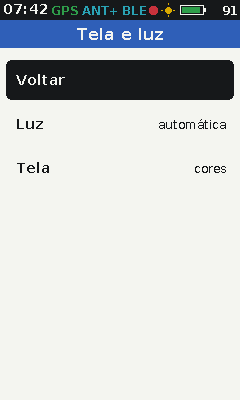
docs/telas/23_tela_luz_cor.png
