Guiimartinho/gnss-bike-computer/docs/telas/24_formatar_cor.png

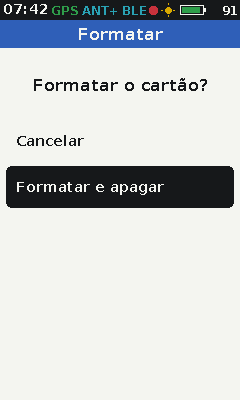
docs/telas/24_formatar_cor.png
