Guiimartinho/gnss-bike-computer/docs/telas/25_energia_cor.png

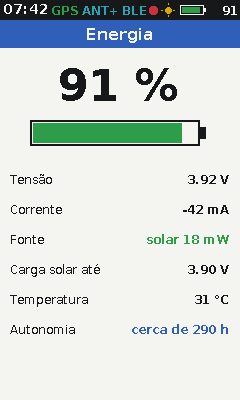
docs/telas/25_energia_cor.png
