Guiimartinho/gnss-bike-computer/docs/telas/26_usb_cor.png

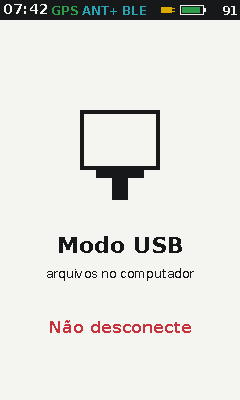
docs/telas/26_usb_cor.png
