Guiimartinho/gnss-bike-computer/docs/telas/27_desligando_cor.png

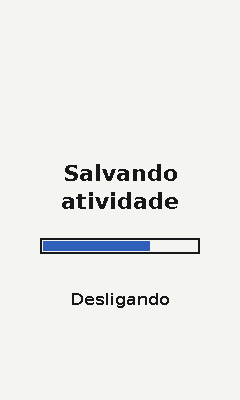
docs/telas/27_desligando_cor.png
