Guiimartinho/gnss-bike-computer/docs/telas/29_atualizacao_pronta_cor.png

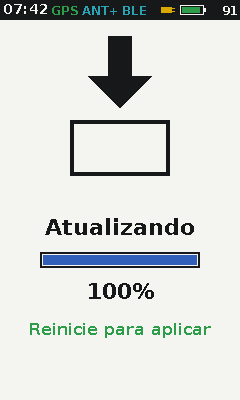
docs/telas/29_atualizacao_pronta_cor.png
