Guiimartinho/gnss-bike-computer/docs/telas/30_perfil_cor.png

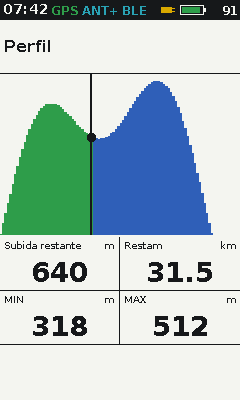
docs/telas/30_perfil_cor.png
