Guiimartinho/gnss-bike-computer/docs/telas/31_volta_cor.png

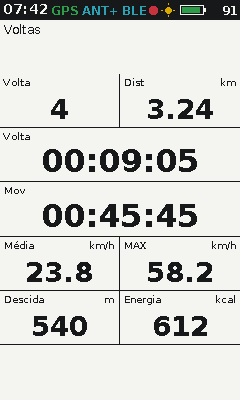
docs/telas/31_volta_cor.png
