Guiimartinho/gnss-bike-computer/docs/telas/33_subida_cor.png

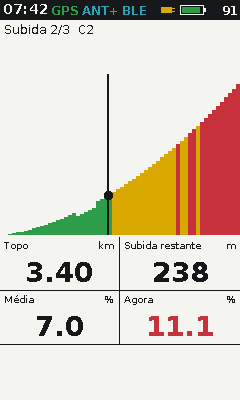
docs/telas/33_subida_cor.png
