Guiimartinho/gnss-bike-computer/docs/telas/33_subida_mono.png

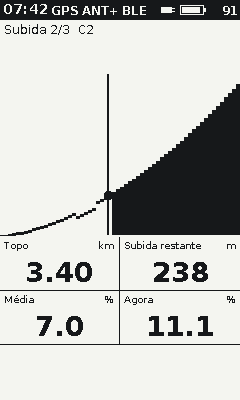
docs/telas/33_subida_mono.png
