Guiimartinho/gnss-bike-computer/docs/telas/34_proxima_subida_mono.png

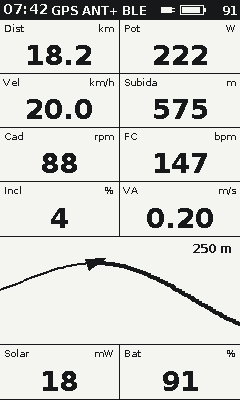
docs/telas/34_proxima_subida_mono.png
