Guiimartinho/gnss-bike-computer/docs/telas/36_queda_cor.png

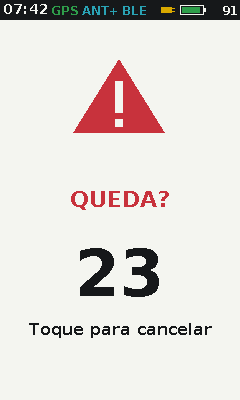
docs/telas/36_queda_cor.png
