Guiimartinho/gnss-bike-computer/docs/telas/37_alarme_cor.png

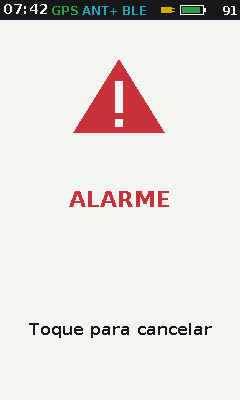
docs/telas/37_alarme_cor.png
