Guiimartinho/gnss-bike-computer/docs/telas/38_treino_cor.png

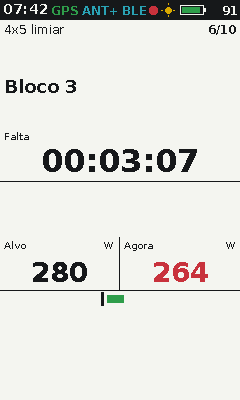
docs/telas/38_treino_cor.png
