Guiimartinho/gnss-bike-computer/docs/telas/39_treino_sem_arquivo_cor.png

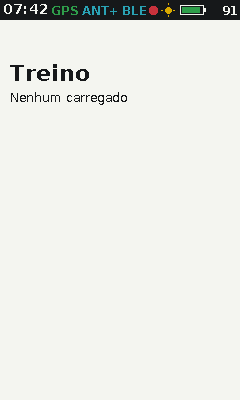
docs/telas/39_treino_sem_arquivo_cor.png
