Guiimartinho/gnss-bike-computer/docs/telas/40_treinos_cor.png

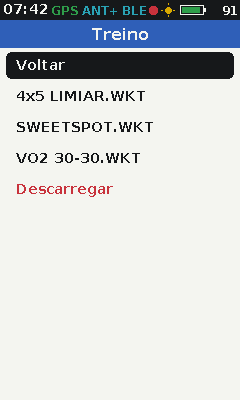
docs/telas/40_treinos_cor.png
