Guiimartinho/gnss-bike-computer/docs/telas/41_alertas_cor.png

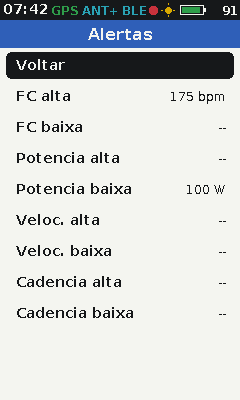
docs/telas/41_alertas_cor.png
