Guiimartinho/gnss-bike-computer/docs/telas/42_lembretes_cor.png

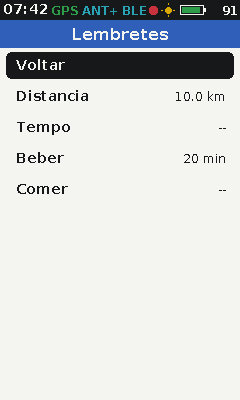
docs/telas/42_lembretes_cor.png
