Guiimartinho/gnss-bike-computer/docs/img/hardware/gnssbike-3d-montagem.png

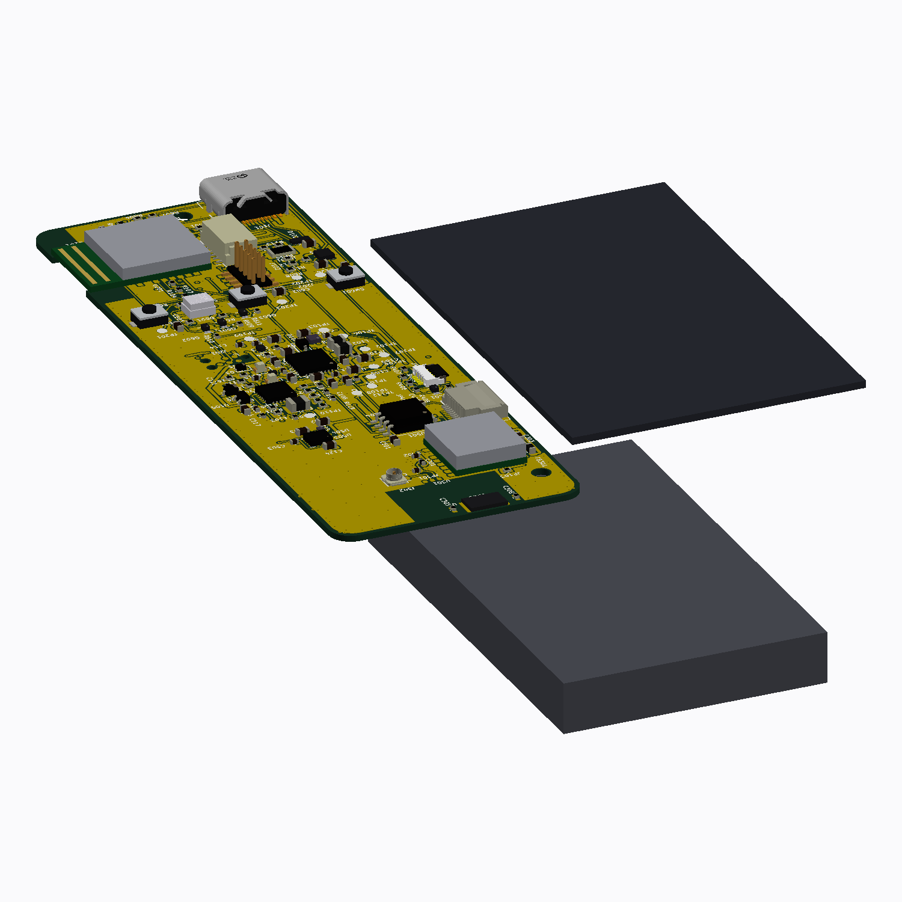
docs/img/hardware/gnssbike-3d-montagem.png
