Guiimartinho/gnss-bike-computer/hardware_gnssbike/cad/make_pcb.py

#!/usr/bin/env python3
"""Write gnssbike.kicad_pcb: the board, with every part placed and every net.

The outline, the stackup, the single mounting hole and the two antenna
keep-outs come from hardware_gnssbike/04-pcb-e-caixa.md. What is new here is
the placement: each part that the document gives a zone to is put in its zone,
and everything else - the decoupling, the pull-ups, the series resistors -
lands on the nearest free slot to the part it belongs to, outside the
keep-outs and off the board edge. Nothing is routed: the tracks are the
owner's job, and this is the board he starts from.

Run:   python hardware_gnssbike/cad/make_pcb.py
Check: python hardware_gnssbike/cad/check_pcb.py
"""

from __future__ import annotations

import hashlib
import math
import pathlib
import sys

HERE = pathlib.Path(__file__).resolve().parent
sys.path.insert(0, str(HERE))

import footprints as FPS  # noqa: E402
import fp_load  # noqa: E402
import make_dxf as M  # noqa: E402
import nets as N  # noqa: E402
import parts as P  # noqa: E402

ORIGEM = (25.0, 25.0)          # where the board's top left sits on the sheet
CU = 0.035
# The stack-up is ASYMMETRIC, and that is the point. Section 4.4 of the
# MAX-F10S integration manual says to "select the stack-up, copper, and
# dielectric properties of the PCB accordingly to fulfil this condition" -
# the condition being 50 ohm on the RF line. With the dielectric split
# evenly, 0.22 mm each, a 50 ohm microstrip is 0.431 mm wide and does not fit
# between the module's pads: it cannot leave its own pin. A thin prepreg to
# the ground plane and a thick core in the middle brings it to 0.196 mm,
# which routes, and it is the usual four layer stack-up for a board with RF.
DIEL_RF = 0.10                 # F.Cu to the ground plane on In1.Cu
DIEL_NUCLEO = 0.80 - 4 * CU - 2 * DIEL_RF    # In1.Cu to In2.Cu
DIEL = (DIEL_RF, DIEL_NUCLEO, DIEL_RF)
CU_LAYERS = ("F.Cu", "In1.Cu", "In2.Cu", "B.Cu")
KEEPOUTS = {"KEEPOUT_ANTENA_GNSS", "KEEPOUT_ANTENA_MODULO"}
BORDA = 0.8                    # keep parts this far inside the outline
RAIO_COURTYARD_FURO = 2.45     # F.CrtYd of MountingHole_2.2mm_M2.kicad_mod
FOLGA = 0.05                   # between two courtyards: the courtyard
                               # already carries the maker's clearance
PASSO = 0.5                    # placement grid

# The part that anchors each zone of 04-pcb-e-caixa.md.
ANCORAS: dict[str, str] = {
    "U301": "ZONA_GNSS_MAX-F10S",
    "D601": "ZONA_LED_RGB",
    "U503": "ZONA_IMU_MAGNETOMETRO",
    "J401": "ZONA_FPC_DISPLAY_J401",
    "LS601": "ZONA_BUZZER",
    "U101": "ZONA_ENERGIA",
    "U501": "ZONA_FLASH_MX25R6435F",
    "U502": "ZONA_BAROMETRO_BMP585",
    "U201": "ZONA_MODULO_ME54BS13",
    "SW602": "ZONA_BOTOES",
    "J101": "ZONA_USB_C",
    "U505": "ZONA_LUZ_AMBIENTE_OPT3001",
}
# Parts that follow an anchor instead of a zone of their own.
JUNTO: dict[str, str] = {
    "U102": "U101", "U103": "U101", "U104": "U101",
    "L101": "U101", "L102": "U101", "L103": "U103",
    "J102": "U101", "JP101": "U101", "RT101": "U101",
    "D101": "J101", "D102": "J101",
    "U105": "U103", "R124": "U103", "R125": "U103", "R106": "U103",
    "D106": "U103", "C122": "U102", "C123": "U503", "C124": "U503",
    "C125": "U502", "C126": "U505",
    "C129": "U101", "R406": "J402", "R407": "J402", "R408": "J402",
    "R409": "J402", "D107": "SW602",
    "FB301": "U301", "L301": "U301",
    "U504": "U503",
    "J402": "J401", "Q401": "J401",
    "SW601": "SW602", "SW603": "SW602",
    "Q601": "D601", "Q602": "D601", "Q603": "D601",
    "J201": "U201", "J202": "U201", "TP201": "U201", "TP202": "U201", "TP203": "U201",
    # Each power test point goes beside what it measures, which is what
    # 06-conectores-e-pontos-de-teste.md asks for point by point: the VBUS one
    # "junto do conector", the ground one "com via propria ao plano".
    "TP101": "J101", "TP102": "U101", "TP103": "U102", "TP104": "U101",
    "TP105": "U101", "TP106": "U101", "TP107": "U101", "TP108": "U101",
    "TP109": "U104", "TP110": "U103", "TP112": "U101",
}
# The back face. Nothing about the case decides this: these are the parts
# that do not have to be reached from the front and that free the front face
# for the ones that do.
# J102 left this set on 2026-09-26: the cell connector is a JST SH on the
# FRONT now (see BORDA_FIXA)
ATRAS = {"U502", "RT101", "LS601", "J103"}
# LS601 is on the back because of arithmetic, not taste: it is 10,5 x 9,5 mm,
# the largest part on the board after the two modules, and on the front the
# only band left between the key row and the module is 9,25 mm tall. Pushed
# out of it, the spiral parked it 0,84 mm from the TPS7A02 and took the ring
# that regulator's decoupling needed, which AL1 then reported as two
# capacitors 5,5 and 6,6 mm from a pin that wants 2. The back face was
# carrying three parts.


def passantes() -> set[str]:
    """Refs whose pads pierce the board, so they take room on both faces."""
    saida = set()
    for ref, (nome, _o, _n) in FPS.FP.items():
        try:
            texto = fp_load.carregar(nome)[0]
        except FileNotFoundError:
            continue
        arv = fp_load.parse(texto)
        for pad in fp_load.kids(arv, "pad"):
            camadas = fp_load.kid(pad, "layers")
            if len(pad) > 2 and pad[2] != "smd":
                saida.add(ref)
                break
            if camadas and any(str(c).startswith("*") for c in camadas[1:]):
                saida.add(ref)
                break
    return saida


PASSANTE = passantes()

# Parts whose position AND rotation the case decides, not the placer: x, y,
# angle. These are not the numbers of 04-pcb-e-caixa.md, and the difference is
# the point. That document's zone table was written before any footprint
# existed, and three of its rectangles do not hold the real part:
#
#   USB-C      the zone is 9 x 3 mm. A USB-C receptacle is about 9 x 10 mm:
#              the body goes INTO the board, it does not sit on its edge. The
#              three keys and the connector cannot share the bottom band, so
#              the keys moved up to y 79 and the connector kept the edge.
#   modulo     the zone is 10 x 16.2 mm, for the Fanstel part. The MinewSemi
#              ME54BS13 is 12 x 16.5, and its datasheet wants 4 mm clear
#              around the antenna side and that side facing off the board. It
#              lies down with the antenna to the right edge, above the keys.
#   GNSS       the zone starts at y 2, inside the antenna keep-out that runs
#              to y 8. 04 already counted that overlap as 90 mm2 and left it
#              open; here the receiver sits below the keep-out, at y 8.5.
# Every one of these is measured from an EDGE of the board, never from the
# absolute coordinate it used to carry: they were written for a 55 x 97
# outline and every one of them was wrong the moment the outline changed.
# W and H come from make_dxf, which derives them from the rules.
_W, _H = M.W, M.H

BORDA_FIXA: dict[str, tuple[float, float, int]] = {
    # A peca fica na ESQUERDA da borda de baixo; o modulo fica na direita, e
    # os dois sao o unico par que cabe ali.
    #
    # O que fixa o y e a BOCA, nao o centro: com o modelo do fabricante
    # girado 180 graus (footprints.MODELO_GIRADO), o corpo vai de -5,30 a
    # +2,60 no referencial do footprint, de modo que a boca esta 2,60 mm a
    # frente da origem. Para ela ficar a 0,64 mm da borda de baixo, a origem
    # cai em _H - 3,24. Com a origem em _H - 5,34, que e onde esteve, a boca
    # ficava 2,74 mm DENTRO da placa e o sobremolde do plugue bateria no
    # canto antes de o conector assentar.
    #
    # A ilha mais proxima da borda passa a ser a da blindagem, a 1,14 mm
    # dela, e os 16 contatos ficam em _H - 7,29, bem dentro.
    # 6,9 e nao 6,2: a 6,2 a serigrafia do receptaculo saia 1,5 mm a
    # esquerda do centro e cortava o arco de 3 mm do canto da placa (DRC
    # silk_edge_clearance, duas vezes); a 6,9 ela fica a 2,2, dentro do arco
    # 6,5 desde o dry run da caixa (2026-09-26): o segundo furo M2 foi para
    # a borda de baixo, entre este receptaculo e o modulo (x >= 17,0), e a
    # reserva dele (4,9 mais 0,05 de cada lado) so cabe com o contorno do
    # receptaculo acabando em 11,82. A serigrafia fica 0,4 mais perto do
    # arco do canto do que a 6,9; o DRC do check_pcb.py e quem diz se corta
    "J101": (6.5, _H - 4.29, 0),
    # O diodo de protecao do USB fica ACIMA da fileira de contatos, a 90
    # graus, com os cinco pinos de sinal virados para ela a 0,5 mm de passo -
    # o mesmo passo da fileira - e com o par ENTRANDO pelos pinos 4 e 5 e
    # SAINDO pelos 7 e 6, em frente, que a ficha reserva para isso. Em x, o
    # x = J101 - 0,25 poe o D+ do diodo meio passo a direita do A6 e o D- meio passo a
    # direita do A7: as duas subidas sao diagonais paralelas, sem cruzar.
    # O colocador o punha ao LADO do receptaculo, em (12,5; 85,5), e dali o
    # par nao chega por F.Cu: entre o pino da blindagem e o diodo sobram
    # 0,73 mm, e duas trilhas de 0,207 com os 0,2 de isolamento pedem 1,01.
    # O ponto de teste do VBUS, que ocupava este lugar, foi para onde o
    # diodo estava.
    # Em y, 79,1 vem do furo M2 que esteve em (4,0; 75,75) ate 2026-09-26:
    # o colocador reserva um QUADRADO de RAIO_COURTYARD_FURO + FOLGA (2,5
    # mm) em volta de um furo, e o contorno do diodo (0,75 abaixo do centro,
    # deitado a 90) tinha de comecar depois de 78,25. O furo foi para a
    # borda de baixo, em (14,4; 91,7) - make_dxf.FUROS_DOC diz por que - e o
    # diodo ficou onde estava, com o sensor de luz acima dele (y <= 75,25)
    # e as pernas do USB-C abaixo (y >= 85,44). As diagonais que ligar_usb()
    # desenha do receptaculo ate os pinos do diodo sao calculadas da posicao
    # real, nao de um numero fixo.
    # x 4,0 since 2026-09-26 (was 6,65): the diode sits against the left
    # edge, leaving x >= 6,65 to the USB pair and the pocket to the right
    # for the cell connector J102
    "D102": (4.0, 79.1, 90),
    # As tres teclas em linha, a 9,0 mm de passo, em y = 66,0 - ABAIXO do
    # display. Ate 2026-09-26 elas estavam em y = 58, e a revisao mecanica
    # mostrou o obvio que ninguem tinha medido: o LPM027M128C tem 61,8 mm de
    # altura numa placa de 90, e cobre y = 58 em qualquer posicao razoavel.
    # Uma tecla debaixo do display nao se aperta. Decisao do dono, o mesmo
    # dia: descem.
    #
    # Onde cabem, medido: a linha fica entre o fim do display (que passa a
    # ter de acabar em y <= 64,5 da placa - restricao registrada em 04; desde
    # o dry run da caixa e 62,9, make_dxf.DISPLAY_Y1, para o furo da capa
    # de 5,6 na tampa nao entrar no vidro) e o
    # corredor sem peca que o par USB precisa para entrar nos pinos do
    # modulo (x 19,4-22,8, y >= 68,3). O que limita a direita e a area da
    # antena do modulo, KEEPOUT_ANTENA_MODULO em x >= 29,3 e y >= 68,0, que
    # a 7.4 da ficha quer a 5 mm de qualquer peca: o contorno da tecla
    # (5,5 x 3,5) acaba 0,25 mm acima da area, entao os 5 mm tem de vir
    # quase todos em x, e o contorno tem de acabar em x <= 24,3. Com 9,0 de
    # passo a terceira tecla ficava em 23,0, a 3,56 mm da area, e livre() a
    # recusou; a 8,5 de passo, centro em 21,5, o contorno acaba em 24,25 e
    # a distancia da 5,06 mm.
    # 2026-09-26, later the same day: the owner wants the three keys spread
    # across the display's width, at the case's pitch, and moved them on the
    # board rather than have the case reach them with levers. Centred on
    # the display (x 17), the widest pitch BORDA allows a 5,5 mm courtyard
    # is 13,4: x 3,6 and 30,4 leave 0,85 mm to the edges. The third key at
    # 30,4 only clears the module's antenna keep-out because the board grew
    # to 95 mm (make_dxf.H) and the module went 5 mm down with it.
    "SW601": (3.6, 66.0, 0),
    "SW602": (17.0, 66.0, 0),
    "SW603": (30.4, 66.0, 0),
    # The 10-way SWD header (2026-09-26): 5 mm tall, so it cannot be under
    # the display (y < 64,5, ceiling 2,6 mm) nor under the cell; and it has
    # to be on the FRONT, where the lid opens. Left as a JUNTO of the module
    # the placer put it at (17,5; 60,5), under the display. Here: below the
    # keys (their courtyard ends at y 67,75), right of the light sensor by
    # more than twice its own 2,5 mm (OP1: at x 11,3 it sat 2,25 mm from
    # U505) and left of the USB pair's corridor (x >= 19,4): the courtyard
    # (8,6 x 7,4) spans x 9,9-18,5 and y 67,9-75,3.
    "J202": (14.2, 71.6, 0),
    # bottom right CORNER, which is the datasheet's "Best" (7.5, figure 1):
    # antenna over the notch, off the board edge, and as far from the GNSS
    # receiver as the board allows - which is the 50 mm of 7.2, and the rule
    # that decides this board's long side. x so that the courtyard ends
    # exactly on the edge: W - 17/2. y leaves 5.75 mm below the module,
    # because the power pins on its lower castellated edge need a capacitor
    # within 0.5 mm and a 0603 courtyard does not fit against the margin.
    "U201": (_W - 8.5, _H - 12.5, 270),
    "J401": (5.1, 26.5, 270),        # display flat cable, out to the left
    # 36, not 38: at 38 its courtyard reached the M2 hole's keep-out,
    # which sits at (3,2; H/2) on the same edge
    "J402": (5.1, 37.0, 270),        # the light's cable, same side
    # on the back face the footprint is mirrored, so the angle that sends
    # the cable to the left is 270, not 90. It costs the front nothing: the
    # two faces have their own placement area since this run.
    # battery connector, now a JST SH on the FRONT (2026-09-26). The GH on
    # the back at (4,0; 62,0) was under the cell, 4,25 mm tall against a
    # 1,2 mm ceiling (ME2); the strip of the back under the cell's shadow
    # (y 70 to 85) cannot hold a GH with the 12 mm buzzer, the M2 hole's
    # square and the USB-C's legs (the buzzer cannot come within 5 mm of
    # the module's antenna keep-out), the back's top strip is the GNSS
    # antenna's keep-out, and on the front a GH (4,25) hits the case's lid,
    # which leaves 3,8 mm. The SH (2,9) fits on the front, in the pocket
    # between the SWD header (y <= 75,3), the module (x >= 17) and the USB-C
    # (y >= 85,4). Lying at (10,6; 82) its left mounting pad sat on the USB
    # pair's path (x 6,65-7,15: DRC clearance and mask bridge, 2 each) and
    # it was 3 mm from the light sensor, which wants 5,8. STANDING (270: the
    # cable leaves to the left, over D102, to the cell under the board) the
    # courtyard is 6,56 x 9,8 at x 10,2-16,8, y 75,5-85,3: 3 mm clear of the
    # USB pair, 6,0 from the sensor, 0,2 from the module and 0,14 from J101.
    "J102": (13.5, 80.4, 270),
    # The Tag-Connect pads: left as a JUNTO of the module they took the
    # pocket meant for J102. No height and no part, so under the display
    # is fine; the clip is used with the board out of the case, and J202
    # is the everyday path (2026-09-26).
    "J201": (26.0, 52.0, 0),
    # The light sensor's datasheet asks for every nearby component to be at
    # least twice its own height away, because of secondary optical
    # reflections. The case window follows the sensor, not the other way.
    # On the RIGHT edge: the left of the top band is the receiver's, and
    # the receiver has to be hard in that corner for the 50 mm rule.
    # ambient light: at (32; 16,5) it was under the display's glass, where
    # no window reaches it. Below the keys, left, where the lid's window is
    # over it (2026-09-26). At (3,5; 71) the first key was 2,0 mm away (it
    # is 2,0 tall) and the SWD header 2,25 (2,5 tall). Here every taller
    # neighbour is beyond twice its height: SW601 5,0 (needs 4), J202 5,65
    # (needs 5), J102 6,0 (needs 5,8), D102 3,1 (needs 0,8); the 0402s
    # around it are lower than the sensor and cast no shadow on it.
    "U505": (3.0, 74.0, 0),
    # y 9,75: o corpo cresceu de 1,6 x 1,6 para 3,5 x 2,8 e ficou a
    # 3,25 mm do sensor de luz, que pede o dobro da altura do vizinho -
    # 3,8 mm para os 1,9 deste LED. Descido para 3,85 mm de folga, com
    # a borda de baixo em 8,10, logo acima do keepout da antena GNSS.
    # RGB LED: at (31,1; 9,75) it was under the display's glass. In the
    # keys' row, between the second and the third key: that row (y <= 67,75)
    # is the only strip below the display and above the 5 mm band of the
    # module's antenna keep-out (y >= 68), and (21,5; 70,5) fell in the USB
    # pair's corridor. The lid's light-pipe hole is under the keys'
    # membrane there (2026-09-26).
    "D601": (23.7, 66.0, 0),
    # barometer, back face: the zone put it at (3; 71), 0,8 mm under the
    # cell's shadow (y <= 69,9) with 1,86 mm against a 1,2 ceiling (ME2).
    # The back's strip off the cell and off the module's antenna band (x <=
    # 24,3 for y >= 68) holds, since 2026-09-26, the solar connector J103
    # standing at the left edge (x 0,9-8,9, y 69,95-80,45), the buzzer
    # (x 11,75-24,25, y 69,95-82,45) and, between the two and above the
    # USB-C's legs (y >= 85,44), this: x 7,82-11,58, y 80,62-84,38.
    "U502": (9.7, 82.5, 0),
    # buzzer, back face, 12,5 round: right of J103, left of the module's
    # antenna band, off the cell (y >= 69,9 with 3,0 mm of height)
    "LS601": (18.0, 76.2, 0),
    # The receiver goes hard into the top LEFT corner, and that is the 50 mm
    # rule again: with it centred, its courtyard overlapped the module's in x
    # and the distance collapsed to the vertical gap alone.
    # 180 degrees, and it is not cosmetic: at 0 the RF_IN pin came out on the
    # LEFT side, which here is the board edge 1.2 mm away, so the antenna
    # feed and its pi network had nowhere to go and ended up 10.5 mm from the
    # pin that 4.4 wants them "as short as possible" from. Turned round, the
    # pin faces into the board, where the network fits in line.
    "U301": (8.5, 15.3, 180),
    # Where the antenna in the case wall lands: under its keep-out and a few
    # millimetres from the pi network, which is what "linha de 50 ohm, poucos
    # mm" in 04-pcb-e-caixa.md asks for. To the right of the receiver, so the
    # pi network sits between the two.
    # A antena de chip, na borda de baixo. O corpo tem 3,0 mm de
    # profundidade e a ficha o poe a 0,30 mm da borda, entao o centro
    # fica em y = 1,80. O x e o do resto da cadeia de RF, para o
    # caminho ser o mais curto possivel.
    "E301": (13.25, 1.8, 0),
    # Os dois capacitores de sintonia, encostados nos pinos de terra
    # da antena: eles SAO parte da antena, nao desacoplamento.
    "C305": (17.55, 1.8, 90),
    "C306": (8.95, 1.8, 90),
    "J302": (20.4, 12.4, 0),
    # The pi network, IN LINE between the antenna contact and the receiver's
    # RF_IN pin, and fixed here rather than left to the netlist placer -
    # which put it 10.5 mm away, on a rule that asks for "as short as
    # possible". The order is the netlist's, not a guess: J302 FEED and
    # C301 sit on RF_ANT, L301 is the series element, and C302 and the pin
    # sit on RF_IN. So antenna, shunt, series, shunt, pin, laid along the
    # 8.06 mm from the contact's pad at (15,0; 10,5) to the pin at
    # (11,0; 17,5). MAX-F10S IM 4.4.
    # Shifted 0,6 mm right on 2026-09-24: the module's land pattern grew when
    # the real drawing was read - the pad now reaches 0,8 mm outside the body
    # instead of 0,35 - and the old positions had the inductor sitting on it.
    "C301": (17.4, 13.4, 0),
    "L301": (15.8, 15.2, 90),
    "C302": (15.8, 17.2, 0),
    # The six solar modules, in three groups of two, on one connector on the
    # right edge. They carry the harvester's SRC node, which is low voltage
    # and is the input of a boost, so it sits as close to the harvester's
    # band as the edge allows: a long run of SRC picks up everything.
    #
    # The angle is 90 so the housing opens toward +X, that is toward the
    # board edge: the contacts of this footprint stick out at y = -1,65 and
    # the body runs from -3,5 to +4,5, so +Y is the cable side. A side-entry
    # connector pointing inward would make the harness loop back over the
    # board. The centre is 5,0 from the edge, which leaves the housing 0,5
    # short of it.
    # y 32,0: o corpo de 4 vias tem 10,5 mm, entao ele vai de 26,75 a
    # 37,25 - 9,0 mm livres ate o sensor de luz (que pede duas vezes a
    # altura do vizinho) e 0,65 mm antes do colhedor.
    # 2026-09-26, the case's dry run: at (W-5; 32) the connector, 3,75 mm
    # tall, sat under the display's glass (ceiling 3,0) and 0,05 mm under
    # the lid. The front outside the display is full (keys, SWD header,
    # cell connector, module, USB-C), so it goes to the BACK, standing at
    # the left edge: 270 sends the cable to the left on the back (see J402),
    # out to the case wall and round the board's edge to the lid's modules.
    # Courtyard 8 x 10,5 at x 0,9-8,9, y 69,95-80,45: off the cell's shadow
    # (y <= 69,9, ceiling 1,2), left of the buzzer (x >= 11,75), above the
    # barometer (y >= 80,62) and the USB-C's legs (y >= 85,44).
    "J103": (4.9, 75.2, 270),
}



# Which chip each capacitor decouples, from 05-materiais.md. The netlist
# cannot say it: a decoupling capacitor sits between a rail and ground, and
# the rail touches everything. The bill of materials is where it is written -
# "C101 a C109: entradas e saidas do nPM1300", "C113, C114: entrada e saida do
# TPS7A02", "C115, C116: CSRC e CINT do AEM10900" - and without it the placer
# sends the capacitor to the centre of gravity of a rail, which is nowhere.
DECOPLA: dict[str, str] = {
    "C101": "U101", "C102": "U101", "C103": "U101", "C104": "U101",
    "C105": "U101", "C106": "U101", "C107": "U101", "C108": "U101",
    "C109": "U101", "C110": "U101", "C111": "U101",
    "C113": "U104", "C114": "U104",
    "C115": "U103", "C116": "U103", "C117": "U103",
    "C118": "U102",
    "C201": "U201", "C210": "U201",
    "C301": "E301", "C302": "U301", "C303": "U301", "C304": "U301",
    "C404": "J401",
    "C501": "U501", "C502": "U504", "C503": "U503",
    "C601": "SW601", "C602": "SW602", "C603": "SW603",
    # the pull-ups of a bus go beside the master, not beside a slave
    "R107": "U201", "R108": "U201", "R504": "U201", "R505": "U201",
    # o pull-up do PMIC_INT vai com o PMIC, nao com o modulo: junto do
    # modulo ele caiu em cima do pino de D+ e fechou a entrada do par USB
    "R109": "U101",
    # the series resistors of the flash: two at the MCU, one at the flash
    "R506": "U201", "R507": "U201", "R508": "U501",
    # the gate pull-downs go at the transistor
    "R402": "Q401", "R609": "Q601", "R610": "Q602", "R611": "Q603",
}

# A part is allowed inside the keep-out that exists because of it: the
# radio module sits over its own antenna zone, which forbids copper, not it.
#
# The same goes for the GNSS chip antenna and its two tuning capacitors. The
# Unictron layout guide is explicit that the 50 ohm trace AND the matching
# components live INSIDE the cut-out - the cut-out forbids ground plane, not
# the antenna's own network. Putting the tuning capacitors outside it would
# put ground between the antenna and its own tuning, which is the one place
# copper must not be.
DONO_DO_KEEPOUT: dict[str, str] = {
    "U201": "KEEPOUT_ANTENA_MODULO",
    "E301": "KEEPOUT_ANTENA_GNSS",
    "C305": "KEEPOUT_ANTENA_GNSS",
    "C306": "KEEPOUT_ANTENA_GNSS",
}

# What the ME54BS13 datasheet actually asks around its antenna, read in
# V1.0.0 and not in a summary of it:
#
#   7.3  no copper pour, no component and no fully enclosed metal housing
#        over the antenna area, and the RF side never faces inward;
#   7.4  "no signal traces, metal objects, or other interference sources
#        should exist within 3-5 mm around the antenna area", the module at
#        the edge or corner, and the PCB beneath the antenna hollowed out.
#
# There is NO "20 mm from a switching converter" rule; this file carried one
# until 2026-09-24, and while it kept the power supply 20 mm away it let ten
# other parts sit inside 5 mm of the antenna - one of them at 0.8 mm.
# It applies to EVERY part, not to a chosen list.
DIST_ANTENA = 5.0

# ME54BS13 V1.0.0, 7.2, "Interference Isolation Rule": 20 mm between the
# module and a DC-DC switching supply, a power inductor or a transformer.
#
# This constraint was in this file, was taken out on 2026-09-24 on the wrong
# conclusion that the rule did not exist, and is back. It does exist - the
# section is 7.2, not the 7.3 that was looked in - and taking it out let a
# power inductor sit 6.8 mm from the module.
#
# It is measured to the MODULE's courtyard, which is what the datasheet says,
# not to the antenna band: the sentence is "the module must maintain a
# minimum safe distance from strong interference sources".
LONGE_DO_MODULO = 20.0
CHAVEIA = {"L101", "L102", "L103", "U101", "U103"}
MODULO_DE_RADIO = "U201"
ANTENA_DO_RADIO = "KEEPOUT_ANTENA_MODULO"
# The module's OWN decoupling is exempt, and it has to be. Section 7.2 puts
# the capacitor 0.5 mm from the power pin, and the module's power pads sit
# 2.1 mm from its own antenna band - so no point exists that satisfies both
# 0.5 mm from the pin and 5 mm from the antenna. The 3-5 mm of 7.4 is about
# foreign interference sources, not about the module's own support parts,
# which every figure in 7.5 draws right against it.
DO_MODULO = {r for r, dono in ()} | {"C201", "C210"}

# Rotations that are not about the case but about the circuit.

ROTACAO: dict[str, int] = {
    "J201": 0,
    "J202": 0,
    "U101": 0,
    "U103": 0,
}


def uid(*parts: object) -> str:
    h = hashlib.sha256("|".join(str(p) for p in parts).encode()).hexdigest()
    return f"{h[0:8]}-{h[8:12]}-4{h[13:16]}-8{h[17:20]}-{h[20:32]}"


def P_(x: float, yd: float) -> tuple[float, float]:
    return (x + ORIGEM[0], yd + ORIGEM[1])


def redes() -> tuple[dict[str, int], dict[tuple[str, str], str]]:
    """Merge the nets that share a pin, number them, and index by pad."""
    bruto: dict[str, set] = {}
    for nome, pinos in N.NETS.items():
        membros = set()
        for ref, pin_name in pinos:
            part = P.PARTS[ref]
            numero = next(q.number for q in part.pins
                          if q.name == pin_name or q.number == pin_name)
            membros.add((ref, numero))
        bruto[nome] = membros
    pai = {n: n for n in bruto}

    def raiz(n):
        while pai[n] != n:
            pai[n] = pai[pai[n]]
            n = pai[n]
        return n

    de_pino: dict[tuple, str] = {}
    for nome, membros in bruto.items():
        for m in membros:
            if m in de_pino:
                a, b = raiz(de_pino[m]), raiz(nome)
                if a != b:
                    pai[b] = a
            else:
                de_pino[m] = nome
    juntos: dict[str, set] = {}
    nomes_do_grupo: dict[str, list[str]] = {}
    for nome, membros in bruto.items():
        juntos.setdefault(raiz(nome), set()).update(membros)
        nomes_do_grupo.setdefault(raiz(nome), []).append(nome)

    # A merged group keeps the best of its names, not whichever happened to
    # claim a pin first. Without this the ground comes out called FPC_VSS,
    # because the panel's ground is one of the names that merged into it.
    import sheets as S
    melhor: dict[str, str] = {}
    for r, membros_nomes in nomes_do_grupo.items():
        melhor[r] = sorted(
            membros_nomes,
            key=lambda n: (n not in S.TRILHOS, -len(bruto[n]), n))[0]

    numeros = {"": 0}
    por_pad: dict[tuple[str, str], str] = {}
    for i, (r, membros) in enumerate(sorted(juntos.items(),
                                            key=lambda kv: melhor[kv[0]]), start=1):
        numeros[melhor[r]] = i
        for m in membros:
            por_pad[m] = melhor[r]
    return numeros, por_pad


def livre(x: float, y: float, bx: tuple[float, float, float, float],
          postos: list[tuple[float, float, float, float]],
          ref: str = "", borda: float | None = None) -> bool:
    """See por(): `postos` is already the list of the face being placed on."""
    """Is the courtyard, placed at (x, y), inside the board and free?

    The box comes relative to the footprint origin, not centred on it: a
    connector's courtyard sits to one side of its pads, and treating it as
    centred is what pushed every decoupling capacitor two millimetres further
    out than it had to be.
    """
    eps = 1e-6
    b = BORDA if borda is None else borda
    x0, y0, x1, y1 = x + bx[0], y + bx[1], x + bx[2], y + bx[3]
    if x0 < b - eps or y0 < b - eps or             x1 > M.W - b + eps or y1 > M.H - b + eps:
        return False
    r = M.RADIUS_DRAWING
    for cx, cy in ((r, r), (M.W - r, r), (r, M.H - r), (M.W - r, M.H - r)):
        qx = min(max(x0, cx - r if cx < M.W / 2 else -1e9),
                 cx + r if cx > M.W / 2 else 1e9)
        del qx
    if ref in CHAVEIA:
        mx, my, mang = BORDA_FIXA[MODULO_DE_RADIO]
        m = caixa(MODULO_DE_RADIO, mang)
        dx = max(mx + m[0] - x1, x0 - (mx + m[2]), 0.0)
        dy = max(my + m[1] - y1, y0 - (my + m[3]), 0.0)
        if math.hypot(dx, dy) < LONGE_DO_MODULO:
            return False
    for nome, (kx0, ky0, kx1, ky1), _c, _s in M.ZONES:
        if nome == ANTENA_DO_RADIO and DONO_DO_KEEPOUT.get(ref) != nome                 and ref not in DO_MODULO:
            dx = max(kx0 - x1, x0 - kx1, 0.0)
            dy = max(ky0 - y1, y0 - ky1, 0.0)
            if math.hypot(dx, dy) < DIST_ANTENA:
                return False
        if nome not in KEEPOUTS or DONO_DO_KEEPOUT.get(ref) == nome:
            continue
        if x1 > kx0 and kx1 > x0 and y1 > ky0 and ky1 > y0:
            return False
    for px0, py0, px1, py1 in postos:
        if x1 + FOLGA > px0 and px1 + FOLGA > x0 and \
                y1 + FOLGA > py0 and py1 + FOLGA > y0:
            return False
    return True


def espiral(cx: float, cy: float, bx: tuple[float, float, float, float],
            postos: list, raio_max: float = 60.0, ref: str = ""):
    """The nearest free slot to (cx, cy), searched outwards."""
    if livre(cx, cy, bx, postos, ref):
        return (cx, cy)
    passo = PASSO
    r = passo
    while r <= raio_max:
        n = max(8, int(2 * math.pi * r / passo))
        for i in range(n):
            a = 2 * math.pi * i / n
            x = round((cx + r * math.cos(a)) / PASSO) * PASSO
            y = round((cy + r * math.sin(a)) / PASSO) * PASSO
            if livre(x, y, bx, postos, ref):
                return (x, y)
        r += passo
    return None


def caixa(ref: str, ang: int) -> tuple[float, float, float, float]:
    """The real courtyard, turned: x0, y0, x1, y1 around the origin.

    Module level on purpose. While this lived inside colocar() the checker
    had a copy of its own - the symmetric box, twice the furthest edge, with
    a 1.8 mm floor - and the two disagreed: the checker reported 54
    overlapping courtyards on a board where KiCad reported one. A rule
    measured by two definitions is not a rule.
    """
    fp_load.carregar(FPS.FP[ref][0])
    x0, y0, x1, y1 = fp_load.CAIXA[FPS.FP[ref][0]]
    for _ in range((ang // 90) % 4):
        x0, y0, x1, y1 = y0, -x1, y1, -x0
    # a minimum, because a test point's courtyard is barely bigger than
    # its own pad and two of them then land on top of each other
    if x1 - x0 < 1.2:
        m = (x0 + x1) / 2
        x0, x1 = m - 0.6, m + 0.6
    if y1 - y0 < 1.2:
        m = (y0 + y1) / 2
        y0, y1 = m - 0.6, m + 0.6
    return (x0, y0, x1, y1)


def tam(ref: str, ang: int) -> tuple[float, float]:
    x0, y0, x1, y1 = caixa(ref, ang)
    return (x1 - x0, y1 - y0)


# Silkscreen text. 0.8 mm tall with a 0.15 mm stroke is not a preference:
# it is the floor almost every fab publishes for legible silkscreen, and what
# this file wrote before - 0.7 with a 0.1 stroke - is below it, so it would
# not print reliably whatever the layout did. Raising it makes the collision
# problem worse, which is why the labels are now PLACED instead of all being
# dropped 1.8 mm above their part: at a fixed offset, 37 pairs of reference
# designators sat on top of each other, and a designator you cannot read
# identifies nothing.
# 0.6 mm with a 0.12 mm stroke. 0.8/0.15 is the number a fab publishes as
# its conservative floor, and it is the right floor for a board with room;
# on this one it is a designator taller than half the parts it names, and it
# read as clutter rather than as labelling. 0.6/0.12 is what dense boards
# use and what most houses print without comment - but it IS below the
# conservative figure, and no fab has been consulted for this board at all
# (that is already an open item), so it is one of the things to confirm with
# the one that is chosen.
TEXTO_ALT = 0.6
TEXTO_TRACO = 0.12
# Width of a character as a fraction of the text height. 1.06, measured in
# KiCad's own SVG export and not guessed: "C101" at 0.8 mm comes out with
# textLength 3.38, which is 0.845 per character. At the 0.75 this carried,
# every label was modelled 30% narrower than it prints, this file reported
# zero collisions and the exported silkscreen had 35 pairs on top of each
# other.
TEXTO_LARG = 1.06
TEXTO_FOLGA = 0.12         # between two labels


def _caixa_texto(ref: str, x: float, y: float, ang: int = 0) -> tuple:
    """The rectangle a label occupies, turned if the label is turned."""
    w = len(ref) * TEXTO_ALT * TEXTO_LARG + TEXTO_FOLGA
    h = TEXTO_ALT + TEXTO_FOLGA
    if ang % 180:
        w, h = h, w
    return (x - w / 2, y - h / 2, x + w / 2, y + h / 2)


def _cruza(a: tuple, b: tuple) -> bool:
    return a[2] > b[0] and b[2] > a[0] and a[3] > b[1] and b[3] > a[1]


def rotulos(lugar: dict) -> dict[str, tuple[float, float, int]]:
    """Where each reference designator goes, and at what angle.

    The angle is not free: it follows the PART. A component turned 90 degrees
    gets a label turned 90 degrees, so the text reads along the thing it
    names, and a board where every designator is horizontal over a column of
    vertical resistors reads as noise - which is what this produced, 123
    labels and not one of them turned, over 44 parts that are.

    Two rules, in order. A label may NEVER sit on another label - that is
    what makes the board unreadable. A label SHOULD not sit on another
    part's courtyard, but on a board at 48% occupancy that is not always
    possible, and a designator printed over a chip's body is still legible
    while two designators printed over each other are not.

    Candidates are tried from the part's own courtyard outwards, nearest
    first, so a label stays next to the thing it names.
    """
    postas: list[tuple] = []
    corpos = []
    ordem_corpos = []
    for ref, (x, y, ang, _a) in lugar.items():
        bx = caixa(ref, ang)
        corpos.append((x + bx[0], y + bx[1], x + bx[2], y + bx[3]))
        ordem_corpos.append(ref)
    saida: dict[str, tuple[float, float, int]] = {}
    # biggest parts first: they have the most room around them and the most
    # to lose from a label landing in the middle of a fine pitch package
    ordem = sorted(lugar, key=lambda r: -(
        (caixa(r, lugar[r][2])[2] - caixa(r, lugar[r][2])[0]) *
        (caixa(r, lugar[r][2])[3] - caixa(r, lugar[r][2])[1])))
    for ref in ordem:
        x, y, ang, _atras = lugar[ref]
        bx = caixa(ref, ang)
        rot = 90 if ang % 180 else 0
        meia_w = len(ref) * TEXTO_ALT * TEXTO_LARG / 2
        meia_h = TEXTO_ALT / 2
        if rot:
            meia_w, meia_h = meia_h, meia_w
        melhor = None
        # PROXIMIDADE primeiro, e so depois qualquer outra coisa.
        #
        # A versao anterior preferia um lugar livre do contorno de QUALQUER
        # peca a um lugar perto da propria. Numa placa a 48% de ocupacao isso
        # empurra o rotulo para milimetros de distancia, e o resultado e uma
        # nuvem de designadores em que nenhum aponta para nada - que e
        # exatamente o que se via no desenho de montagem. Um rotulo sobre o
        # contorno da PROPRIA peca continua dizendo qual peca e; um rotulo a
        # 4 mm dela nao diz.
        #
        # Entao: candidatos do mais perto para o mais longe, e o primeiro que
        # nao cai sobre OUTRO rotulo ganha. Cair sobre contorno so desempata
        # entre candidatos da mesma distancia.
        for passo in (0.0, 0.25, 0.5, 0.8, 1.2, 1.7, 2.3):
            anel = []
            for dx, dy in ((0.0, bx[1] - meia_h - 0.2 - passo),
                           (0.0, bx[3] + meia_h + 0.2 + passo),
                           (bx[2] + meia_w + 0.25 + passo, 0.0),
                           (bx[0] - meia_w - 0.25 - passo, 0.0),
                           (bx[2] + meia_w + 0.25 + passo,
                            bx[1] - meia_h - 0.2 - passo),
                           (bx[0] - meia_w - 0.25 - passo,
                            bx[1] - meia_h - 0.2 - passo),
                           (bx[2] + meia_w + 0.25 + passo,
                            bx[3] + meia_h + 0.2 + passo),
                           (bx[0] - meia_w - 0.25 - passo,
                            bx[3] + meia_h + 0.2 + passo)):
                cx_, cy_ = x + dx, y + dy
                t = _caixa_texto(ref, cx_, cy_, rot)
                # the whole box of the text stays 0.3 mm inside the outline,
                # not just its centre: a label turned 90 degrees near the
                # bottom edge kept its centre inside and its far half out,
                # and the DRC reported the silkscreen cut by the edge
                if not (t[0] > 0.3 and t[2] < M.W - 0.3
                        and t[1] > 0.3 and t[3] < M.H - 0.3):
                    continue
                if any(_cruza(t, q) for q in postas):
                    continue
                # quantos contornos ALHEIOS ele pisa: so para desempatar
                alheios = sum(1 for r2, c in zip(ordem_corpos, corpos)
                              if r2 != ref and _cruza(t, c))
                anel.append((alheios, (dx, dy), t))
            if anel:
                anel.sort(key=lambda q: q[0])
                melhor = (anel[0][1], anel[0][2], anel[0][0] == 0)
                break
        if melhor is None:
            # nothing anywhere: leave it on the part and say so by putting it
            # dead centre, which is visibly deliberate rather than a near miss
            saida[ref] = (0.0, 0.0, rot)
            postas.append(_caixa_texto(ref, x, y, rot))
            continue
        saida[ref] = (melhor[0][0], melhor[0][1], rot)
        postas.append(melhor[1])
    return saida


def colocar() -> tuple[dict[str, tuple[float, float, int, bool]], list[str]]:
    """Place every part: x, y, rotation and which face.

    The rules are the ones a person uses, in this order:

      1. a connector faces the edge it comes out of, and its rotation is not
         negotiable: the USB-C opening has to point out of the case, the
         display's flat cable has to leave to the left, the module's antenna
         has to look off the board;
      2. a part with a zone in 04-pcb-e-caixa.md goes to the middle of it;
      3. everything else goes to the centre of gravity of the parts it
         connects to, so a decoupling capacitor lands beside the pin it
         decouples and a series resistor lands between the two ends it joins;
      4. a two terminal part is turned to lie along the line between the two
         parts it connects, which is what makes the track short and straight
         instead of an L around the part.
    """
    zonas = {n: r for n, r, _c, _s in M.ZONES}
    tam_bruto: dict[str, tuple[float, float]] = {}
    for ref, (nome, _o, _n) in FPS.FP.items():
        tam_bruto[ref] = fp_load.carregar(nome)[1]

    lugar: dict[str, tuple[float, float, int, bool]] = {}
    # The hole is KiCad's MountingHole_2.2mm_M2, and THAT footprint's
    # courtyard is a circle of 2,45 mm of radius (fp_circle end 2.45 on
    # F.CrtYd), for the head or washer of the screw. Reserving less than the
    # courtyard is how J201 landed 2,0 mm from the hole and the DRC called it
    # an overlap: the placer and the DRC have to agree on the same circle.
    raio = RAIO_COURTYARD_FURO + FOLGA
    # One list per face, not one for the board. A part on the back does not
    # take room from a part on the front, and pretending it does is how a
    # small board runs out of space that it has: the battery connector, the
    # barometer and the thermistor were blocking the front face where they
    # are not. What IS in both lists is what goes through the board - the
    # mounting hole and its keep-out - because that really does take the room
    # on both faces.
    furos = [(fx - raio, fy - raio, fx + raio, fy + raio)
             for fx, fy in M.FUROS_DOC]
    # Corredores sem peca, so na frente: faixas que o roteamento precisa e
    # que o colocador enchia de peca miuda. O primeiro fica em cima dos
    # pinos D+ e D- do modulo, em (20,55; 71,5) e (21,65; 71,5) com o
    # modulo onde BORDA_FIXA o poe: o par do USB so entra neles por cima,
    # entre vizinhos a 1,1 mm, e um resistor a 1,5 mm acima do pino fecha
    # a entrada - o R109 fechou, e quando ele saiu o DISP_PWR_EN entrou.
    # ate 70,7 e nao ate os pinos: a caixa de colocacao do modulo comeca
    # em 70,75, e um corredor que entra nela derruba a posicao fixa do modulo.
    # De 68,3 e nao de 68,2: o contorno da tecla da direita acaba em 67,75 e
    # livre() exige FOLGA entre contornos; a 68,2 a tecla nao cabia.
    # The top end follows the module since the board grew to 95
    # (2026-09-26): the module's placement box starts at H - 19,25, and the
    # corridor ends 0,05 above it, as before; the bottom end stays at 68,3,
    # FOLGA under the keys' courtyards, which did not move in y.
    # The second corridor is the USB pair's own path from the ESD diode D102
    # (courtyard to y 79,85, x 2,5-5,5) to the receptacle J101 (from y 85,44,
    # D+ and D- pads at x 6,25 and 6,75): ligar_usb() draws the two diagonals
    # there from the real positions, and the placer knew nothing about them.
    # When the bottom M2 hole moved to (14,4; 91,7) on 2026-09-26 it pushed
    # the test point TP101 to (3; 84), straight onto the pair: a short to a
    # ground stub, a clearance of 0,071 mm and a mask bridge, all three in
    # the DRC. Both ends are fixed parts, so the strip stops FOLGA short of
    # each courtyard; x 3 to 8,5 keeps the cell connector (x >= 10,22) out
    # of it.
    corredores = [(19.4, 68.3, 22.8, M.H - 19.3), (3.0, 80.0, 8.5, 85.3)]
    postos_face: dict[bool, list[tuple[float, float, float, float]]] = {
        False: list(furos) + corredores, True: list(furos)}
    falhas: list[str] = []

    def por(ref: str, cx: float, cy: float, ang: int = 0,
            preso: bool = False) -> None:
        bx = caixa(ref, ang)
        atras = ref in ATRAS
        # a part whose pads pierce the board has to clear BOTH faces, and it
        # has to do so when IT is placed, not only afterwards: the Tag-Connect
        # is placed late, by connectivity, and landed on top of the buzzer -
        # which had gone to the back precisely because the front had no room.
        postos = postos_face[atras]
        if ref in PASSANTE:
            postos = postos + postos_face[not atras]
        if preso:
            # a fixed position has to be legal on its own: overlapping here
            # silently is how two connectors end up on top of each other.
            # A connector that comes out of the case may touch the edge - that
            # is the point of it - so the edge margin does not apply to it.
            p = (cx, cy) if livre(cx, cy, bx, postos, ref, borda=0.0) else None
            if p is None:
                falhas.append(f"{ref}: a posicao fixa ({cx:.1f}; {cy:.1f}) nao "
                              f"esta livre para o contorno {bx}")
        else:
            p = espiral(cx, cy, bx, postos, ref=ref)
        if p is None:
            falhas.append(f"{ref}: nao coube perto de ({cx:.1f}; {cy:.1f})")
            return
        lugar[ref] = (p[0], p[1], ang, ref in ATRAS)
        caixa_posta = (p[0] + bx[0], p[1] + bx[1], p[0] + bx[2], p[1] + bx[3])
        postos_face[atras].append(caixa_posta)
        if ref in PASSANTE:
            # its pads pierce the board, so it takes the room on both faces
            postos_face[not atras].append(caixa_posta)

    # ---- 1. the parts whose orientation the case decides ----
    for ref, (cx, cy, ang) in BORDA_FIXA.items():
        if ref in tam_bruto:
            por(ref, cx, cy, ang, preso=True)

    # ---- 2. the zones ----
    for ref, zona in ANCORAS.items():
        if ref in lugar:
            continue
        if ref not in tam_bruto:
            falhas.append(f"{ref}: sem footprint, nao colocado")
            continue
        x0, y0, x1, y1 = zonas[zona]
        ang = ROTACAO.get(ref, 0)
        por(ref, round((x0 + x1) / 2 / PASSO) * PASSO,
            round((y0 + y1) / 2 / PASSO) * PASSO, ang)

    # ---- 3. decoupling and inductors, hugging the pin they serve ----
    # The datasheets do not say "near": the ME54BS13 asks for 0.5 mm between a
    # capacitor's pad and the power pin, and both the nPM1300 and the AEM10900
    # ask for the inductor and the reactive parts "as close as possible" to
    # their pins. A capacitor 7 mm away is 15 nH of loop, which at 200 mA and a
    # 2 ns edge is 1.5 V of ringing on a 3.7 V rail - the capacitor stops being
    # a capacitor and becomes part of the problem.
    def pad_global(ref: str, numero: str) -> tuple[float, float] | None:
        if ref not in lugar:
            return None
        nome_fp = FPS.FP[ref][0]
        texto = fp_load.carregar(nome_fp)[0]
        arv = fp_load.parse(texto)
        for p in fp_load.kids(arv, "pad"):
            if p[1] != numero:
                continue
            a = fp_load.kid(p, "at")
            px, py = float(a[1]), float(a[2])
            x, y, ang, atras = lugar[ref]
            if atras:
                px = -px
            r = math.radians(ang)
            return (x + px * math.cos(r) + py * math.sin(r),
                    y - px * math.sin(r) + py * math.cos(r))
        return None

    def pads_locais(ref: str) -> list[tuple[float, float]]:
        """Every pad of a footprint, as an offset from the footprint origin."""
        arv = fp_load.parse(fp_load.carregar(FPS.FP[ref][0])[0])
        saida = []
        for p in fp_load.kids(arv, "pad"):
            a = fp_load.kid(p, "at")
            if a:
                saida.append((float(a[1]), float(a[2])))
        return saida

    def encostar(ref: str) -> bool:
        """Put a two terminal part right beside the pin it serves."""
        if ref in lugar or ref not in tam_bruto or len(P.PARTS[ref].pins) != 2:
            return False
        melhor = None
        # the bill of materials decides first; the netlist only breaks ties
        dono_bom = DECOPLA.get(ref)
        for _nome, pinos in N.NETS.items():
            refs = {r for r, _p in pinos}
            if ref not in refs:
                continue
            if dono_bom is None and len(refs) > 8:
                continue
            if dono_bom is not None and dono_bom not in refs:
                continue
            for outro, pino in pinos:
                if outro == ref or outro not in lugar:
                    continue
                if dono_bom is not None and outro != dono_bom:
                    continue
                if dono_bom is None and len(P.PARTS[outro].pins) < 4:
                    continue
                numero = next(q.number for q in P.PARTS[outro].pins
                              if q.name == pino or q.number == pino)
                p = pad_global(outro, numero)
                if p and (melhor is None or len(P.PARTS[outro].pins) > melhor[2]):
                    melhor = (p, outro, len(P.PARTS[outro].pins))
        if melhor is None:
            return False
        (px, py), dono, _n = melhor
        dx, dy, _a, _b = lugar[dono]
        v = math.hypot(px - dx, py - dy) or 1.0
        ux, uy = (px - dx) / v, (py - dy) / v

        # What every one of these datasheets constrains is the loop from the
        # supply PIN to the capacitor's own PAD, and that is not the distance
        # between the two parts' centres: a 0402 turned the wrong way puts its
        # near pad half a millimetre further out for nothing, and stepping a
        # fixed 0.6 mm out of the chip ignores which pad ends up facing the
        # pin. So each free candidate is scored pad to pad, both orientations
        # are tried, and the best wins. C111 sat 2.02 mm from U101's 3V3BL pin
        # against a 2.00 limit while a slot 1.90 mm away was free one grid
        # step up - the old rule could not see it, because by centre distance
        # that slot was the worse of the two.
        locais = pads_locais(ref)
        fora = max((math.hypot(a, b) for a, b in locais), default=0.0)
        espelha = -1.0 if ref in ATRAS else 1.0
        melhor_pos, melhor_d = None, float("inf")
        caixas = {a: caixa(ref, a) for a in (0, 90)}
        postos = postos_face[ref in ATRAS]
        if ref in PASSANTE:
            postos = postos + postos_face[ref not in ATRAS]
        raio = PASSO
        while raio <= 12.0:
            # a pad can only be `fora` closer than the part's own centre, so
            # once the ring itself is further than that, nothing on it or
            # beyond it can beat what is already in hand
            if raio - fora > melhor_d:
                break
            n = max(12, int(2 * math.pi * raio / PASSO))
            for i in range(n):
                a = 2 * math.pi * i / n
                cx = round((px + raio * math.cos(a)) / PASSO) * PASSO
                cy = round((py + raio * math.sin(a)) / PASSO) * PASSO
                for ang, bx in caixas.items():
                    if not livre(cx, cy, bx, postos, ref):
                        continue
                    r = math.radians(ang)
                    d = min(math.hypot(cx + espelha * ax * math.cos(r)
                                       + ay * math.sin(r) - px,
                                       cy - espelha * ax * math.sin(r)
                                       + ay * math.cos(r) - py)
                            for ax, ay in locais)
                    if d < melhor_d:
                        melhor_d, melhor_pos = d, (cx, cy, ang)
            raio += PASSO
        if melhor_pos is None:
            # nothing free within 12 mm: fall back to the old step-out so the
            # failure is reported by por() instead of vanishing
            ang = 0 if abs(ux) >= abs(uy) else 90
            w, h = tam(ref, ang)
            d = 0.6 + max(w, h) / 2
            por(ref, round((px + ux * d) / PASSO) * PASSO,
                round((py + uy * d) / PASSO) * PASSO, ang)
            return ref in lugar
        por(ref, melhor_pos[0], melhor_pos[1], melhor_pos[2])
        return ref in lugar

    def ordem_de_encostar(ref: str) -> tuple:
        """Who gets first pick of the ring around a chip.

        The smallest capacitor decouples the highest frequency, and it is the
        one whose loop to the pin has to be shortest: a 100 nF part 4 mm away
        is not decoupling anything above a few tens of megahertz, while a
        10 uF bulk capacitor 4 mm away is doing its job. So the ring is
        handed out by capacitance, smallest first, and only then to
        everything else. Alphabetical order - which is what this did before -
        put C101 ahead of C112 for no reason at all.
        """
        if ref not in DECOPLA or not ref.startswith("C"):
            return (2, 0.0, ref)
        # The radio module's own decoupling picks first, whatever its value:
        # its datasheet asks for 0.5 mm from the pin, which is the tightest
        # number on this board, and the module sits in a corner where the
        # room runs out. Sorting only by capacitance let a 4.7 uF that had to
        # be within 5 mm land 11.2 mm away, behind parts with no such rule.
        if DECOPLA[ref] == "U201":
            return (0, 0.0, ref)
        v = P.PARTS[ref].value.lower().replace(",", ".")
        mult = {"p": 1e-12, "n": 1e-9, "u": 1e-6, "µ": 1e-6}
        f = 1.0
        for letra, m in mult.items():
            if letra + "f" in v:
                f = m
                break
        try:
            num = float(v.split()[0])
        except (ValueError, IndexError):
            num = 1.0
        return (1, num * f, ref)

    # first pass: the parts that hug an anchor, before the other
    # chips take the ring around it
    for ref in sorted(FPS.FP, key=ordem_de_encostar):
        encostar(ref)

    # A test point takes what is LEFT. It is a pad to touch a probe on, and
    # it must never push a decoupling capacitor off the ring it needs: when
    # the eleven points of the power sheet were placed with the rest of
    # JUNTO, AL1 went from zero capacitors out of limit to three, one of them
    # 4.0 mm from a pin that wants 2.
    for ref, dono in sorted(JUNTO.items(),
                            key=lambda kv: kv[0].startswith("TP")):
        if ref not in tam_bruto or dono not in lugar or ref in lugar:
            continue
        if ref.startswith("TP"):
            continue                     # depois do desacoplamento
        dx, dy = lugar[dono][0], lugar[dono][1]
        por(ref, dx, dy, ROTACAO.get(ref, 0))

    # second pass: now the chips that follow an anchor are placed too
    for ref in sorted(FPS.FP, key=ordem_de_encostar):
        encostar(ref)

    # and only now the test points, on whatever the decoupling left
    for ref, dono in JUNTO.items():
        if not ref.startswith("TP") or ref not in tam_bruto or ref in lugar:
            continue
        if dono not in lugar:
            continue
        dx, dy = lugar[dono][0], lugar[dono][1]
        por(ref, dx, dy, ROTACAO.get(ref, 0))

    # ---- 4. the rest, by connectivity, turned along it ----
    ligados: dict[str, set[str]] = {}
    for _nome, pinos in N.NETS.items():
        refs = {r for r, _p in pinos}
        if len(refs) > 8:          # a rail joins everything: it says nothing
            continue
        for a in refs:
            ligados.setdefault(a, set()).update(refs - {a})

    # which parts each terminal of a two pin part talks to
    por_terminal: dict[str, dict[str, set[str]]] = {}
    for _nome, pinos in N.NETS.items():
        refs = {r for r, _p in pinos}
        if len(refs) > 8:
            continue
        for ref, pino in pinos:
            if len(P.PARTS[ref].pins) != 2:
                continue
            por_terminal.setdefault(ref, {}).setdefault(pino, set()).update(
                refs - {ref})

    def angulo(ref: str) -> int:
        """Lay a two terminal part along the line between its two ends."""
        if ref in ROTACAO:
            return ROTACAO[ref]
        lados = por_terminal.get(ref)
        if not lados or len(lados) < 2:
            return 0
        centros = []
        for _pino, outros in sorted(lados.items()):
            pts = [lugar[o] for o in outros if o in lugar]
            if not pts:
                return 0
            centros.append((sum(p[0] for p in pts) / len(pts),
                            sum(p[1] for p in pts) / len(pts)))
        dx = centros[1][0] - centros[0][0]
        dy = centros[1][1] - centros[0][1]
        return 0 if abs(dx) >= abs(dy) else 90

    resto = [r for r in FPS.FP if r not in lugar]
    # A part the spiral cannot place stays out of `lugar`, and until
    # 2026-09-26 it also stayed in `resto` with the same score: the same wave
    # came round again, ran the whole spiral again, and the placer never
    # ended (a stack dump every two minutes showed it in espiral(), always
    # from this loop). Whoever fails is given up on here and reported by
    # por() in `falhas`; the run ends and says which part did not fit.
    desistidos: set[str] = set()
    while resto:
        pontuacao = {r: len(ligados.get(r, set()) & set(lugar)) for r in resto}
        melhor = max(pontuacao.values())
        if melhor == 0:
            for ref in sorted(resto):
                por(ref, M.W / 2, M.H / 2, ROTACAO.get(ref, 0))
            break
        onda = [r for r in resto if pontuacao[r] == melhor]
        for ref in sorted(onda):
            vizinhos = [lugar[v] for v in ligados.get(ref, ()) if v in lugar]
            cx = sum(v[0] for v in vizinhos) / len(vizinhos)
            cy = sum(v[1] for v in vizinhos) / len(vizinhos)
            por(ref, round(cx / PASSO) * PASSO, round(cy / PASSO) * PASSO,
                angulo(ref))
            if ref not in lugar:
                desistidos.add(ref)
        resto = [r for r in resto if r not in lugar and r not in desistidos]

    return lugar, falhas


def cabecalho(n_redes: int, nomes: dict[str, int]) -> str:
    lay = [(0, "F.Cu", "signal", "top_cu"), (1, "In1.Cu", "signal", "gnd"),
           (2, "In2.Cu", "signal", "pwr"), (31, "B.Cu", "signal", "bottom_cu"),
           (32, "B.Adhes", "user", "B.Adhesive"), (33, "F.Adhes", "user", "F.Adhesive"),
           (34, "B.Paste", "user", None), (35, "F.Paste", "user", None),
           (36, "B.SilkS", "user", "B.Silkscreen"), (37, "F.SilkS", "user", "F.Silkscreen"),
           (38, "B.Mask", "user", None), (39, "F.Mask", "user", None),
           (40, "Dwgs.User", "user", "User.Drawings"), (41, "Cmts.User", "user", "User.Comments"),
           (42, "Eco1.User", "user", "User.Eco1"), (43, "Eco2.User", "user", "User.Eco2"),
           (44, "Edge.Cuts", "user", None), (45, "Margin", "user", None),
           (46, "B.CrtYd", "user", "B.Courtyard"), (47, "F.CrtYd", "user", "F.Courtyard"),
           (48, "B.Fab", "user", None), (49, "F.Fab", "user", None)]
    rows = "\n".join(f'\t\t({n} "{nm}" {ty}' + (f' "{al}")' if al else ")")
                     for n, nm, ty, al in lay)
    pilha = [('\t\t\t(layer "F.SilkS"\n\t\t\t\t(type "Top Silk Screen")\n\t\t\t)'),
             ('\t\t\t(layer "F.Paste"\n\t\t\t\t(type "Top Solder Paste")\n\t\t\t)'),
             ('\t\t\t(layer "F.Mask"\n\t\t\t\t(type "Top Solder Mask")\n'
              '\t\t\t\t(thickness 0.01)\n\t\t\t)')]
    for i, nm in enumerate(CU_LAYERS):
        pilha.append(f'\t\t\t(layer "{nm}"\n\t\t\t\t(type "copper")\n'
                     f'\t\t\t\t(thickness {CU})\n\t\t\t)')
        if i < 3:
            tipo = "core" if i == 1 else "prepreg"
            pilha.append(f'\t\t\t(layer "dielectric {i + 1}"\n\t\t\t\t(type "{tipo}")\n'
                         f'\t\t\t\t(thickness {DIEL[i]:.4f})\n\t\t\t\t(material "FR4")\n'
                         f'\t\t\t\t(epsilon_r 4.5)\n\t\t\t\t(loss_tangent 0.02)\n\t\t\t)')
    pilha += [('\t\t\t(layer "B.Mask"\n\t\t\t\t(type "Bottom Solder Mask")\n'
               '\t\t\t\t(thickness 0.01)\n\t\t\t)'),
              ('\t\t\t(layer "B.Paste"\n\t\t\t\t(type "Bottom Solder Paste")\n\t\t\t)'),
              ('\t\t\t(layer "B.SilkS"\n\t\t\t\t(type "Bottom Silk Screen")\n\t\t\t)'),
              '\t\t\t(copper_finish "None")\n\t\t\t(dielectric_constraints no)']
    ax = P_(0.0, 0.0)
    redes_txt = "\n".join(f'\t(net {i} "{nome}")'
                          for nome, i in sorted(nomes.items(), key=lambda kv: kv[1]))
    return ("(kicad_pcb\n\t(version 20240108)\n\t(generator \"pcbnew\")\n"
            "\t(generator_version \"8.0\")\n\t(general\n\t\t(thickness 0.8)\n"
            "\t\t(legacy_teardrops no)\n\t)\n\t(paper \"A4\")\n\t(layers\n" + rows + "\n\t)\n"
            "\t(setup\n\t\t(stackup\n" + "\n".join(pilha) + "\n\t\t)\n"
            "\t\t(pad_to_mask_clearance 0)\n"
            f"\t\t(aux_axis_origin {ax[0]:.4f} {ax[1]:.4f})\n"
            f"\t\t(grid_origin {ax[0]:.4f} {ax[1]:.4f})\n\t)\n" + redes_txt)


def contorno(saida: list[str], r: float) -> None:
    w = 0.1

    def linha(a, b):
        saida.append(f'\t(gr_line\n\t\t(start {a[0]:.4f} {a[1]:.4f})\n'
                     f'\t\t(end {b[0]:.4f} {b[1]:.4f})\n'
                     f'\t\t(stroke (width {w}) (type solid))\n\t\t(layer "Edge.Cuts")\n'
                     f'\t\t(uuid "{uid("l", a, b)}")\n\t)')

    def arco(c, a0, a1):
        def pt(d):
            return (c[0] + r * math.cos(math.radians(d)), c[1] + r * math.sin(math.radians(d)))
        s, m, e = pt(a0), pt((a0 + a1) / 2), pt(a1)
        saida.append(f'\t(gr_arc\n\t\t(start {s[0]:.4f} {s[1]:.4f})\n'
                     f'\t\t(mid {m[0]:.4f} {m[1]:.4f})\n\t\t(end {e[0]:.4f} {e[1]:.4f})\n'
                     f'\t\t(stroke (width {w}) (type solid))\n\t\t(layer "Edge.Cuts")\n'
                     f'\t\t(uuid "{uid("a", c, a0)}")\n\t)')

    # The notch under the module's antenna. Section 7.4 of the ME54BS13
    # datasheet asks for the PCB beneath the antenna to be hollowed out so
    # the antenna region is suspended, and figure 1 of 7.5 - the one it calls
    # "Best" - shows exactly this: the module in a corner with its RF end
    # over the void. Taking it out to the board edge makes it a notch rather
    # than a slot, which avoids leaving a 1 mm rib of board on the outside.
    recorte = next((z for n, z, _c, _s in M.ZONES
                    if n == "RECORTE_ANTENA_MODULO"), None)

    linha(P_(r, 0.0), P_(M.W - r, 0.0))
    if recorte:
        rx0, ry0, _rx1, ry1 = recorte
        linha(P_(M.W, r), P_(M.W, ry0))
        linha(P_(M.W, ry0), P_(rx0, ry0))
        linha(P_(rx0, ry0), P_(rx0, ry1))
        linha(P_(rx0, ry1), P_(M.W, ry1))
        linha(P_(M.W, ry1), P_(M.W, M.H - r))
    else:
        linha(P_(M.W, r), P_(M.W, M.H - r))
    linha(P_(M.W - r, M.H), P_(r, M.H))
    linha(P_(0.0, M.H - r), P_(0.0, r))
    arco(P_(M.W - r, r), 270, 360)
    arco(P_(M.W - r, M.H - r), 0, 90)
    arco(P_(r, M.H - r), 90, 180)
    arco(P_(r, r), 180, 270)


def pad_no_lugar(ref: str, numero: str, lugar: dict):
    """Where a pad ends up on the board, given the placement."""
    if ref not in lugar or ref not in FPS.FP:
        return None
    arv = fp_load.parse(fp_load.carregar(FPS.FP[ref][0])[0])
    for q in fp_load.kids(arv, "pad"):
        if q[1] != numero:
            continue
        a = fp_load.kid(q, "at")
        px, py = float(a[1]), float(a[2])
        x, y, ang, atras = lugar[ref]
        if atras:
            px = -px
        r = math.radians(ang)
        return (x + px * math.cos(r) + py * math.sin(r),
                y - px * math.sin(r) + py * math.cos(r))
    return None


def sem_plano_no_chaveamento(lugar: dict, por_pad: dict) -> list[tuple]:
    """Where no copper pour may go: under a switching node.

    Section 13 of DS-AEM1090x-v2.4.0, word for word: "PCB track capacitance
    must be reduced as much as possible on the boost converter switching node
    SWDCDC. This is done as follows: keep the connection between the SWDCDC
    pin and the inductor short; REMOVE THE GROUND AND POWER PLANES UNDER THE
    SWDCDC NODE - the polygon on the opposite external layer may also be
    removed - increase the distance between SWDCDC and the ground polygon on
    the external PCB layer where the AEM1090x is mounted." And the same
    principle for TH_REF.

    A pour under a switching node is capacitance the converter has to charge
    and discharge at its switching frequency, and on a harvester that runs on
    microwatts that is not a detail. So the rectangle that holds the node's
    pads, with margin, is cut out of every plane.
    """
    zonas = []
    for rede, folga in (("SW_DCDC", 0.6), ("TH_REF", 0.4)):
        pontos = []
        for (ref, num), nome in por_pad.items():
            if nome != rede or ref not in lugar:
                continue
            q = pad_no_lugar(ref, num, lugar)
            if q:
                pontos.append(q)
        if len(pontos) < 2:
            continue
        x0 = min(q[0] for q in pontos) - folga
        y0 = min(q[1] for q in pontos) - folga
        x1 = max(q[0] for q in pontos) + folga
        y1 = max(q[1] for q in pontos) + folga
        zonas.append((f"SEM_PLANO_{rede}", (x0, y0, x1, y1)))
    return zonas


def keepout(nome: str, x0: float, y0: float, x1: float, y1: float,
            so_plano: bool = False) -> str:
    """A forbidden area. With so_plano, only the pour is forbidden.

    An antenna zone forbids every kind of copper. A switching node is
    different: section 13 of the AEM10900 datasheet asks to "remove the
    ground and power PLANES under the SWDCDC node", and the node's own track
    obviously has to be there - it is the whole point of the rule. Forbidding
    tracks there too put sixteen items_not_allowed in the DRC, every one of
    them the switching node itself.
    """
    pts = [P_(x0, y0), P_(x1, y0), P_(x1, y1), P_(x0, y1)]
    poly = "\n".join(f"\t\t\t\t(xy {px:.4f} {py:.4f})" for px, py in pts)
    camadas = " ".join(f'"{ly}"' for ly in CU_LAYERS)
    return (f'\t(zone\n\t\t(net 0)\n\t\t(net_name "")\n\t\t(layers {camadas})\n'
            f'\t\t(uuid "{uid("z", nome)}")\n\t\t(name "{nome}")\n\t\t(hatch edge 0.5)\n'
            '\t\t(connect_pads\n\t\t\t(clearance 0)\n\t\t)\n\t\t(min_thickness 0.25)\n'
            '\t\t(filled_areas_thickness no)\n\t\t(keepout\n'
            # An antenna zone forbids COPPER, not parts: the radio module's
            # own antenna sits inside its own keep-out, and its pads with it.
            # A switching node's zone forbids only the POUR, because the node
            # itself has to run there.
            f'\t\t\t(tracks {"allowed" if so_plano else "not_allowed"})\n'
            f'\t\t\t(vias {"allowed" if so_plano else "not_allowed"})\n'
            '\t\t\t(pads allowed)\n'
            '\t\t\t(copperpour not_allowed)\n\t\t\t(footprints allowed)\n\t\t)\n'
            '\t\t(fill\n\t\t\t(thermal_gap 0.5)\n\t\t\t(thermal_bridge_width 0.5)\n\t\t)\n'
            f'\t\t(polygon\n\t\t\t(pts\n{poly}\n\t\t\t)\n\t\t)\n\t)')


def virar(corpo: str) -> str:
    """Flip a footprint to the back face.

    KiCad does not flip a footprint when its layer says B.Cu: the file has to
    already hold the mirrored geometry and the back layer names. Leaving the
    pads on F.Cu under a footprint declared on B.Cu is what makes the DRC say
    two pads of the same connector are shorted with zero clearance - which is
    what it said before this existed.
    """
    for f, b in (('"F.Cu"', '"B.Cu"'), ('"F.Paste"', '"B.Paste"'),
                 ('"F.Mask"', '"B.Mask"'), ('"F.SilkS"', '"B.SilkS"'),
                 ('"F.CrtYd"', '"B.CrtYd"'), ('"F.Fab"', '"B.Fab"'),
                 ('"F.Adhes"', '"B.Adhes"')):
        corpo = corpo.replace(f, b)

    # mirror x on every coordinate the footprint carries
    saida: list[str] = []
    i = 0
    chaves = ("(at ", "(start ", "(end ", "(center ", "(mid ", "(xy ")
    while i < len(corpo):
        for k in chaves:
            if corpo.startswith(k, i):
                j = corpo.index(")", i) if ")" in corpo[i:] else len(corpo)
                dentro = corpo[i + len(k):j].split()
                if dentro and _numero(dentro[0]):
                    dentro[0] = f"{-float(dentro[0]):g}"
                    if k == "(at " and len(dentro) == 3 and _numero(dentro[2]):
                        dentro[2] = f"{(180.0 - float(dentro[2])) % 360:g}"
                saida.append(k + " ".join(dentro) + ")")
                i = j + 1
                break
        else:
            saida.append(corpo[i])
            i += 1
    return "".join(saida)


def _numero(s: str) -> bool:
    try:
        float(s)
        return True
    except ValueError:
        return False


def girar_pads(corpo: str, ang: int) -> str:
    """Turn every pad by the footprint's angle.

    In a .kicad_pcb a pad's own angle is ABSOLUTE, not relative to its
    footprint: KiCad rotates the pad's position with the footprint but not the
    pad's body. Leave it out and a rotated connector's pads keep their
    original orientation while their centres turn, so they overlap and the DRC
    reports zero clearance between neighbours - which is what it reported
    until this existed.
    """
    if ang % 360 == 0:
        return corpo
    saida: list[str] = []
    i = 0
    dentro_pad = False
    while i < len(corpo):
        if corpo.startswith("(pad ", i):
            dentro_pad = True
        elif dentro_pad and corpo.startswith("(at ", i):
            j = corpo.index(")", i)
            v = corpo[i + 4:j].split()
            a = float(v[2]) if len(v) > 2 else 0.0
            saida.append(f"(at {v[0]} {v[1]} {(a + ang) % 360:g})")
            i = j + 1
            dentro_pad = False
            continue
        saida.append(corpo[i])
        i += 1
    return "".join(saida)


def plano_de_terra(numero: int, camadas: tuple[str, ...], recuo: float) -> str:
    """A ground pour, which is what makes the inner layer a reference plane.

    04-pcb-e-caixa.md is explicit that In1.Cu is a solid ground and that the
    plane is what the GNSS antenna radiates against. The zone is drawn here
    and KiCad fills it when the board is opened; the keep-outs already refuse
    a pour, so the two antenna areas stay clear on their own.
    """
    r = M.RADIUS_DRAWING
    pts = []
    for cx, cy, a0, a1 in ((r, r, 180, 270), (M.W - r, r, 270, 360),
                           (M.W - r, M.H - r, 0, 90), (r, M.H - r, 90, 180)):
        for k in range(9):
            a = math.radians(a0 + (a1 - a0) * k / 8.0)
            pts.append(P_(cx + (r - recuo) * math.cos(a) + (recuo if cx < M.W / 2 else -recuo),
                          cy + (r - recuo) * math.sin(a) + (recuo if cy < M.H / 2 else -recuo)))
    poly = "\n".join(f"\t\t\t\t(xy {px:.4f} {py:.4f})" for px, py in pts)
    lay = " ".join(f'"{ly}"' for ly in camadas)
    return (f'\t(zone\n\t\t(net {numero})\n\t\t(net_name "GND")\n\t\t(layers {lay})\n'
            f'\t\t(uuid "{uid("gnd", camadas)}")\n\t\t(name "PLANO_GND")\n'
            '\t\t(hatch edge 0.5)\n\t\t(priority 0)\n'
            # SOLID, not thermal reliefs. Left on the KiCad default, eleven
            # ground pads came out with fewer than two spokes - U101, U102,
            # U104, U503, U504, both shield rows of the USB-C receptacle and
            # three passives - because a track runs past the side the second
            # spoke needed. A one spoke connection is a 0.3 mm neck in series
            # with the return current of the USB shell and of the MCU, on a
            # board that carries a 2.4 GHz radio and two switching
            # converters, and it is the only thing the DRC calls an error
            # here. Thermal relief is a HAND and WAVE soldering aid; nothing
            # on this board can be soldered by hand anyway - 0402s, a WLP-9
            # and a 0.4 mm pitch QFN.
            #
            # What it costs, written down because it is a real cost: reworking
            # a ground pad by hand needs more heat, and a 0402 with one end on
            # the pour and the other not is a little likelier to tombstone at
            # reflow. If the assembly house objects, this is the one line to
            # change - `yes` back to nothing.
            '\t\t(connect_pads yes\n\t\t\t(clearance 0.2)\n\t\t)\n'
            '\t\t(min_thickness 0.2)\n\t\t(filled_areas_thickness no)\n'
            '\t\t(fill yes\n\t\t\t(thermal_gap 0.3)\n\t\t\t(thermal_bridge_width 0.3)\n\t\t)\n'
            f'\t\t(polygon\n\t\t\t(pts\n{poly}\n\t\t\t)\n\t\t)\n\t)')


def com_redes(corpo: str, ref: str, por_pad: dict, numeros: dict) -> str:
    """Put the net of each pad into the footprint body."""
    saida = []
    for linha in corpo.split("\n"):
        saida.append(linha)
        s = linha.strip()
        if s.startswith('(pad "'):
            num = s.split('"')[1]
            nome = por_pad.get((ref, num))
            if nome:
                ident = linha[:len(linha) - len(linha.lstrip())]
                saida.append(f'{ident}\t(net {numeros[nome]} "{nome}")')
    return "\n".join(saida)


def main() -> int:
    numeros, por_pad = redes()
    lugar, falhas = colocar()

    saida: list[str] = []
    contorno(saida, M.RADIUS_DRAWING)
    for nome, (x0, y0, x1, y1), _c, src in M.ZONES:
        if nome in KEEPOUTS:
            saida.append(keepout(nome, x0, y0, x1, y1))
        else:
            a, b = P_(x0, y0), P_(x1, y1)
            saida.append(
                f'\t(gr_rect\n\t\t(start {a[0]:.4f} {a[1]:.4f})\n'
                f'\t\t(end {b[0]:.4f} {b[1]:.4f})\n'
                f'\t\t(stroke (width 0.1) (type dash))\n\t\t(fill none)\n'
                f'\t\t(layer "Dwgs.User")\n\t\t(uuid "{uid("r", nome)}")\n\t)')

    # The switching nodes get their pour cut away, which is what section 13
    # of the AEM10900 datasheet asks for by name.
    for nome_z, (zx0, zy0, zx1, zy1) in sem_plano_no_chaveamento(lugar, por_pad):
        saida.append(keepout(nome_z, zx0, zy0, zx1, zy1, so_plano=True))

    # The ground planes. In1.Cu is the solid one and the reference the return
    # current follows; F.Cu and B.Cu get the leftover copper.
    #
    # The front pour is not decoration. Without it every ground pad on the
    # front face depended on a via of its own to reach In1.Cu, and in the
    # crowded corner around the power supply eighteen of the ninety-five had
    # nowhere to put one - so eighteen ground pads had no ground. With the
    # pour, KiCad ties them to it when it fills, and the stubs that do fit
    # stay as the low impedance path they were meant to be.
    if "GND" in numeros:
        saida.append(plano_de_terra(numeros["GND"], ("In1.Cu",), 0.3))
        saida.append(plano_de_terra(numeros["GND"], ("F.Cu",), 0.3))
        saida.append(plano_de_terra(numeros["GND"], ("B.Cu",), 0.3))

    # the mounting holes
    furo = pathlib.Path(
        r"D:\KiCAD\share\kicad\footprints\MountingHole.pretty"
        r"\MountingHole_2.2mm_M2.kicad_mod").read_text(encoding="utf-8")
    corpo_furo = furo[furo.index("\n"):].rstrip()[:-1].rstrip()
    # The library footprint carries a visible "REF**" on the silkscreen. It
    # names nothing - the hole is not a part - and on this board it was the
    # one label left sitting on another, over J402's.
    corpo_furo = corpo_furo.replace(
        '(property "Reference" "REF**"',
        '(property "Reference" "REF**" (hide yes)', 1)
    for i_furo, (dx_furo, dy_furo) in enumerate(M.FUROS_DOC):
        fx, fy = P_(dx_furo, dy_furo)
        saida.append('\t(footprint "MountingHole:MountingHole_2.2mm_M2"\n'
                     f'\t\t(at {fx:.4f} {fy:.4f})\n'
                     f'\t\t(uuid "{uid("furo%d" % i_furo)}")'
                     + corpo_furo.replace("\n", "\n\t") + "\n\t)")

    # where each reference designator goes, decided once for the whole board
    desloca = rotulos(lugar)

    # the parts
    for ref, (x, y, ang, atras) in sorted(lugar.items()):
        nome_fp = FPS.FP[ref][0]
        corpo = fp_load.corpo(nome_fp)
        if atras:
            corpo = virar(corpo)
            # a maker's model on the back may need its own offset, measured
            # (footprints.MODELO_GIRADO_VERSO): the flip is KiCad's, and it
            # does not mirror the model offset the way it mirrors the pads
            corpo = FPS.modelo_no_verso(corpo)
        corpo = girar_pads(corpo, ang)
        corpo = com_redes(corpo, ref, por_pad, numeros)
        px, py = P_(x, y)
        camada = "B.Cu" if atras else "F.Cu"
        # rotulos() picks the offset in the BOARD's frame, and KiCad turns a
        # footprint property by the footprint's own angle before drawing it.
        # Written straight through, a label placed "above" a part rotated 90
        # degrees came out beside it: measured in the exported silkscreen,
        # 38 pairs still overlapped while this file believed there were none.
        # So the world offset is turned back into the footprint's frame,
        # with the same transform pad_global() uses, and mirrored on the back
        # face for the same reason the pads are.
        _r = math.radians(ang)
        _dx, _dy, _ang_rot = desloca[ref]
        _rot = (_dx * math.cos(_r) - _dy * math.sin(_r),
                _dx * math.sin(_r) + _dy * math.cos(_r))
        if atras:
            _rot = (-_rot[0], _rot[1])
        cab = (f'\t(footprint "{nome_fp}"\n\t\t(layer "{camada}")\n'
               f'\t\t(at {px:.4f} {py:.4f} {ang})\n'
               f'\t\t(uuid "{uid("fp", ref)}")\n'
               f'\t\t(property "Reference" "{ref}"\n'
               f'\t\t\t(at {_rot[0]:.4f} {_rot[1]:.4f} {_ang_rot})\n'
               f'\t\t\t(layer "{"B" if atras else "F"}.SilkS")\n'
               f'\t\t\t(uuid "{uid("fpref", ref)}")\n'
               f'\t\t\t(effects (font (size {TEXTO_ALT} {TEXTO_ALT}) '
               f'(thickness {TEXTO_TRACO}))'
               + (' (justify mirror)' if atras else '') + ')\n\t\t)\n'
               f'\t\t(property "Value" "{P.PARTS[ref].value}"\n\t\t\t(at 0 1.8 0)\n'
               f'\t\t\t(layer "{"B" if atras else "F"}.Fab")\n'
               f'\t\t\t(uuid "{uid("fpval", ref)}")\n'
               '\t\t\t(effects (font (size 0.6 0.6) (thickness 0.1))'
               + (' (justify mirror)' if atras else '') + ')\n\t\t)')
        saida.append(cab + corpo + "\n\t)")

    notas = [
        f"GNSS BIKE COMPUTER - placa {M.W:g} x {M.H:g} mm, "
        f"{M.THICKNESS:g} mm, 4 camadas",
        f"{len(lugar)} pecas colocadas, {len(FPS.FORA_DA_PLACA)} fora da placa "
        "(painel, antena e modulos solares vivem na caixa)",
        f"{len(M.FUROS_DOC)} furos M2; empilhamento assimetrico {DIEL_RF:g} / "
        f"{DIEL_NUCLEO:.2f} / {DIEL_RF:g} mm, para os 50 ohm da linha de RF",
        "ROTEAMENTO PARCIAL; NADA FABRICADO, NADA MEDIDO",
    ]
    for i, s in enumerate(notas):
        p = P_(0.0, M.H + 3.0 + i * 2.0)
        saida.append(f'\t(gr_text "{s}"\n\t\t(at {p[0]:.4f} {p[1]:.4f} 0)\n'
                     f'\t\t(layer "Cmts.User")\n\t\t(uuid "{uid("t", i)}")\n'
                     '\t\t(effects (font (size 1.2 1.2) (thickness 0.2)) '
                     '(justify left top))\n\t)')

    out = HERE / "gnssbike.kicad_pcb"
    out.write_text(cabecalho(len(numeros), numeros) + "\n" + "\n".join(saida) + "\n)\n",
                   encoding="utf-8", newline="\n")
    print(f"{out.name}: {len(lugar)} pecas, {len(numeros) - 1} redes, "
          f"{len(KEEPOUTS)} areas de regra")
    if falhas:
        print(f"  NAO COLOCADAS: {len(falhas)}")
        for f in falhas:
            print(f"    {f}")
    return 1 if falhas else 0


if __name__ == "__main__":
    sys.exit(main())
