Guiimartinho/gnss-bike-computer/hardware_gnssbike/cad/nets.py

#!/usr/bin/env python3
"""Every net of the board, as (reference, pin name).

This is hardware_gnssbike/03-netlist.md turned into data. The pin NAME is used,
not the number, because that is what the documents state; parts.py turns the
name into the number the symbol carries.

Two rules were kept while writing this:

  - nothing that the documents do not state is wired here. Where a document
    leaves a connection open, the net is listed in ABERTO instead, and the
    schematic writes it as a note on the sheet rather than as a wire that
    would look decided.
  - where a document is internally inconsistent, the inconsistency is carried
    across with its name, not silently resolved. The central key is the
    clearest case: the devicetree wires it to P1.27 and four documents say it
    must go only to SHPHLD.
"""

from __future__ import annotations

# The only parts whose pin may appear in two nets: a connector and the part
# behind it are one electrical node, and the schematic draws them as two.
# ANY OTHER pin in two nets is a short, and check_sch.py fails on it - a
# capacitor that ended up in both PWR_SDA and 3V0 once shorted the whole power
# bus to the 3 V rail, and the merge hid it.
PASSA_DIRETO = {"J401", "J402", "DS401"}

# name -> [(ref, pin name), ...]
NETS: dict[str, list[tuple[str, str]]] = {}

# things a document explicitly leaves open: name -> why
ABERTO: dict[str, str] = {}


def net(name: str, *pins: tuple[str, str]) -> None:
    NETS[name] = list(pins)


# ------------------------------------------------------------ alimentacao
net("VBUS", ("J101", "VBUS_A4"), ("J101", "VBUS_A9"), ("J101", "VBUS_B4"),
    ("J101", "VBUS_B9"), ("U101", "VBUS"), ("D101", "IO"), ("C101", "1"))
net("VBUSOUT", ("U101", "VBUSOUT"), ("U201", "VBUS"), ("R104", "1"), ("C110", "1"))
# Os quatro NC do TPD4E05U06 estao nas redes de proposito. A tabela 4-2 da
# ficha (SLVSBO7O) diz deles: "Not connected; used for optional
# straight-through routing" - o sinal entra num lado do USON e sai pelo pino
# em frente, que e o unico jeito de um par de 0,5 mm de passo atravessar a
# peca sem contornar a fileira. O 10 fica em frente ao 1, o 9 ao 2, o 7 ao
# 4 e o 6 ao 5.
net("CC1", ("J101", "CC1"), ("U101", "CC1"), ("D102", "D1P"), ("D102", "NC4"))
net("CC2", ("J101", "CC2"), ("U101", "CC2"), ("D102", "D1N"), ("D102", "NC3"))
net("USB_DP", ("J101", "DP_A6"), ("J101", "DP_B6"), ("U201", "USB_DP"), ("D102", "D2P"), ("D102", "NC2"))
net("USB_DM", ("J101", "DM_A7"), ("J101", "DM_B7"), ("U201", "USB_DM"), ("D102", "D2N"), ("D102", "NC1"))

# The cell reaches the gauge through the measuring jumper; the gauge's 7 mOhm
# sense sits INSIDE the chip, between BATT and SYS, so those are two nodes.
# J102, a celula: 1 e 6 VBAT+, 2 e 5 GND, 3 NTC do pack, 4 reservado - a
# pinagem que 06-conectores-e-pontos-de-teste.md manda ao fabricante do pack.
# Ate 2026-09-26 o cobre tinha 1 VBAT+, 4 NTC e 6 GND, com 2, 3 e 5 soltos:
# um cabo feito como o documento pedia poria o VBAT+ do pino 6 no GND da
# placa - curto da celula - e o NTC no pino 3, que nao ia a lugar nenhum.
net("VBAT_CELULA", ("J102", "1"), ("J102", "6"), ("JP101", "1"))
net("VBAT", ("JP101", "2"), ("U102", "BATT"), ("U102", "TH"), ("C122", "1"))
# O BAT e o SYS do colhedor entram aqui. O STO do AEM10900 NAO estava
# ligado a lugar nenhum - defeito que so apareceu na troca de peca.
# A chave interna do ADP5091 fica entre os dois e abre com a celula
# abaixo de 3,0 V; SYS e de onde o proprio CI tira a corrente de
# repouso, e BAT e o no de armazenamento.
net("VBAT_SYS", ("U102", "SYS"), ("U101", "VBAT"), ("U104", "IN"),
    ("U103", "BAT"), ("U103", "SYS"),
    ("C120", "1"), ("C116", "1"),
    ("U104", "EN"), ("C117", "1"), ("C102", "1"), ("C113", "1"))
ABERTO["VBAT / VBAT_SYS"] = ("de que lado do sensor interno do MAX17262 ficam o BATT e o "
                             "SYS nao esta fechado; trocar os dois inverte o sinal da corrente")

net("VSYS", ("U101", "VSYS"), ("U101", "LSIN2"), ("U105", "V+"), ("D103", "A"), ("D104", "A"),
    ("D601", "ANODO"), ("C103", "1"))
net("BUCK1_SW", ("U101", "SW1"), ("L101", "1"))
# O BUCK1 ficou sem carga alem dos capacitores. Decisao do dono em
# 2026-09-26: o receptor passou para o 3V0 - opcao 1 da tabela 35 do manual
# de integracao UBXDOC-963802114-12892 (VCC e V_IO juntos, VIO_SEL aberto,
# V_IO de 2,7 a 3,6 V) -, o que tirou o tradutor de nivel TXU0204 e o LDO de
# 1,8 V que existiu por umas horas. O BUCK1 continua montado como na
# configuracao 1 da ficha do nPM1300 (tabela 39): a ficha so mostra buck sem
# uso para o BUCK2 (figura 56, 9.3.2: VOUT2 no VSYS, SW2 aberto, VSET2 no
# GND), e nao se copia para o BUCK1 o que ela nao mostrou. O firmware o
# desliga.
net("1V8", ("L101", "2"), ("U101", "VOUT1"), ("C104", "1"), ("C109", "1"))
net("3V0_BLOCO", ("JP103", "2"), ("FB301", "1"))
net("3V0_GNSS", ("FB301", "2"), ("U301", "VCC"), ("U301", "V_IO"), ("C303", "1"),
    ("C304", "1"))
net("BUCK2_SW", ("U101", "SW2"), ("L102", "1"))
net("3V0", ("L102", "2"), ("U101", "VOUT2"), ("U101", "LSIN1"),
    ("JP103", "1"), ("C129", "1"),
    ("C105", "1"), ("C106", "1"), ("C107", "1"), ("C108", "1"),
    ("JP102", "1"), ("JP104", "1"), ("JP105", "1"),
    ("R107", "1"), ("R108", "1"), ("R109", "1"), ("R110", "1"),
    ("J201", "VTref"), ("J202", "VTref"))
net("3V0_MOD", ("JP102", "2"), ("U201", "VDD"), ("C201", "1"), ("C210", "1"))
net("3V0_SENS", ("JP105", "2"), ("R112", "1"), ("C123", "1"), ("C124", "1"),
    ("C125", "1"), ("C126", "1"), ("U502", "VDD"), ("U502", "VDDIO"), ("U502", "CSB"),
    ("U502", "SDO"), ("U503", "VDD"), ("U503", "VDDIO"), ("U503", "ASDX"), ("U503", "ASCX"),
    ("U503", "CSB"), ("U504", "VDD"), ("U505", "VDD"),
    ("R504", "1"), ("R505", "1"), ("C502", "1"), ("C503", "1"))
net("SD3V0", ("U101", "LSOUT1"), ("JP106", "1"), ("R501", "1"), ("R502", "1"),
    ("R503", "1"))
# the bulk sits AFTER the jumper, beside the flash, like every other block on
# this board: 02-calculos.md asks for 22 uF "junto da flash", and a 1206
# jumper between the part and its energy is what the other blocks avoid
net("SD3V0_FLASH", ("JP106", "2"), ("U501", "VCC"), ("C501", "1"))
net("3V3BL", ("U101", "LSOUT2"), ("C111", "1"), ("J402", "5"), ("DS401", "LUZ_ANODO"))
net("VBCKP", ("U104", "OUT"), ("U301", "V_BCKP"), ("C114", "1"))
# O VINT do AEM10900 era o trilho interno que alimentava os pinos de
# configuracao por strap - R_MPP, T_MPP, STO_CFG, KEEP_ALIVE. O ADP5091
# nao tem nada disso: cada limiar sai de um divisor de resistores, e a
# referencia interna nao sai em pino nenhum.
# The six modules are wired in PARALLEL, and that is not a choice: each
# KXOB25-05X3F already has 3 cells in series and opens at 2,07 V, while the
# AEM10900 tracks from 0,12 to 2,73 V. Two in series would be 4,14 V, which
# is 1,4 V past the ceiling. So: everything in parallel, MPP at 80 % of
# 2,07 = 1,66 V, up to 110 mA with all six normal to the sun.
#
# Three groups, one per face of the case, each through its own 0 ohm - open
# one and the group can be measured alone in the sun.
net("PV_A", ("J103", "PV_A"), ("R113", "1"), ("PV101", "P"), ("PV102", "P"))
net("PV_B", ("J103", "PV_B"), ("R114", "1"), ("PV103", "P"), ("PV104", "P"))
net("PV_C", ("J103", "PV_C"), ("R115", "1"), ("PV105", "P"), ("PV106", "P"))
# A entrada do boost. O indutor vai de VIN a SW, que e o que a descricao do
# pino 13 da ficha manda; o capacitor de 10 uF fica entre VIN e PGND, o mais
# perto possivel.
net("SRC", ("U103", "VIN"), ("C115", "1"), ("L103", "1"), ("D105", "IO"),
    ("RT101", "1"), ("R124", "1"),
    ("R117", "1"),
    ("R113", "2"), ("R114", "2"), ("R115", "2"))
net("SW_DCDC", ("U103", "SW"), ("L103", "2"))

# O regulador interno de 150 mA fica DESABILITADO: a placa ja tem o nPM1300
# para isso, e com REG_D0 e REG_D1 em nivel baixo o consumo de repouso cai
# para 510 nA tipicos, o menor dos quatro estados. O que a ficha manda fazer
# com os pinos que sobram: REG_FB ligado ao REG_OUT (configuracao de saida
# fixa - e o que impede o no de realimentacao de flutuar, que e o risco real
# de oscilacao num regulador desligado), SETBK ao AGND, e o capacitor de
# 4,7 uF no REG_OUT mantido no footprint, podendo ficar nao montado.
#
# LLD e BACK_UP ficam ABERTOS: o LLD e saida e o nivel alto dele e o proprio
# REG_OUT, que com o regulador desligado e 0 V, entao ele nunca sobe; e as
# chaves do BACK_UP ficam permanentemente abertas por causa do SETBK no AGND.
net("REG_OUT", ("U103", "REG_OUT"), ("U103", "REG_FB"), ("C121", "1"))

# O MPPT: a razao e o resistor de BAIXO sobre o total. R117 de VIN ao pino,
# R116 do pino ao AGND, e o capacitor de 10 nF que segura a tensao por 16 s
# entre duas amostras da tensao em aberto.
net("MPPT", ("U103", "MPPT"), ("R116", "1"), ("R117", "2"))
net("CBP", ("U103", "CBP"), ("C119", "1"))

# Os dois limiares que o AEM10900 fazia por strap e por I2C, agora por
# divisor. Os dois penduram no pino REF, NAO no BAT: a figura 42 da ficha
# (Rev. A, p. 19) poe os quatro divisores externos entre REF e AGND, e o CI
# liga o REF ao BAT por dentro, por chaves, com RSETSD_HYS de 115 k em
# serie para fazer a histerese do SETSD, e ao TERM_REF na hora de comparar
# o TERM. Ate 2026-09-26 os dois estavam pendurados no VBAT com o REF
# aberto: a equacao 6 (VBAT_TERM = 3/2 x VINT_REF x (1 + RTERM1/RTERM2))
# so vale com o topo no REF, e a histerese do SETSD nao existia.
net("ADP_REF", ("U103", "REF"), ("R118", "1"), ("R120", "1"))
net("TERM", ("U103", "TERM"), ("R118", "2"), ("R119", "1"))
net("SETSD", ("U103", "SETSD"), ("R120", "2"), ("R121", "1"))
net("MINOP", ("U103", "MINOP"), ("R122", "1"))
net("VID", ("U103", "VID"), ("R123", "1"))

# O USB bloqueia a carga solar em hardware, sem pino do microcontrolador -
# a mesma funcao do DIS_STO_CH do AEM10900, agora no DIS_SW. A saida do
# comparador de temperatura entra em OU-cabeado no mesmo no: qualquer um dos
# dois levanta o pino e o boost para.
net("DIS_SW", ("U103", "DIS_SW"), ("R104", "2"), ("R105", "1"), ("D106", "K"))

# O corte termico que o AEM10900 fazia sozinho, agora por comparador: o
# ADP5091 nao tem entrada de temperatura, e ate 2026-09-26 o divisor do NTC
# (RT101 e R106) estava na placa sem ninguem para le-lo. Decisao do dono
# nesse dia: o divisor alimentado pelo proprio painel (SRC), o TLV7031
# (U105) compara com a referencia R124/R125 e, quente, leva o DIS_SW para
# cima pelo D106 - o mesmo pino que o divisor do VBUSOUT (R104/R105) ja usa
# para bloquear a carga solar com o cabo ligado. So o lado quente: o frio
# (carga abaixo de 0 graus) ficou em aberto, registrado em 01.
net("NTC_SOLAR", ("RT101", "2"), ("R106", "1"), ("U105", "IN+"))
net("REF_TERM", ("R124", "2"), ("R125", "1"), ("U105", "IN-"))
net("TERM_QUENTE", ("U105", "OUT"), ("D106", "A"))
ABERTO["DIS_STO_CH"] = ("qual dos dois resistores fica em serie nao esta em fonte "
                        "nenhuma; 100 k em serie da 5,0 V no pino e 1 M da 0,5 V")
net("NTC_BAT", ("U101", "NTC"), ("J102", "3"))
ABERTO["C107, C108, C109, C112"] = ("a lista de materiais nao diz em que no cada um destes entra: C101 a C109 sao \"entradas e saidas do nPM1300\" em bloco")
ABERTO["NTC_BAT"] = "qual via do J102 leva o NTC do pack vem do fabricante do pack"

net("RVSET1", ("U101", "VSET1"), ("R102", "1"))
net("RVSET2", ("U101", "VSET2"), ("R103", "1"))
net("REG_GAUGE", ("U102", "REG"), ("C118", "1"))
net("LED_CHG", ("U101", "LED1"), ("D103", "K"))
net("LED_ERR", ("U101", "LED0"), ("D104", "K"))
net("ALRT", ("U102", "ALRT"), ("R110", "2"))
# O ADP5091 nao tem pino de interrupcao. O R111, que fazia o pull-up do IRQ
# do AEM10900, ficou sem funcao em 2026-09-25 e saiu da lista em
# 2026-09-26: o TLV7031 do corte termico tem saida push-pull e nao precisa
# de pull-up.

# ------------------------------------------------------------ MCU e I2C
net("PWR_SDA", ("U201", "P0.02"), ("U101", "SDA"), ("U102", "SDA"),
    ("R107", "2"))
net("PWR_SCL", ("U201", "P0.03"), ("U101", "SCL"), ("U102", "SCL"),
    ("R108", "2"))
net("PMIC_INT", ("U201", "P0.00"), ("U101", "GPIO3"), ("R109", "2"))
net("SENS_SDA", ("U201", "P1.29"), ("U502", "SDX"), ("U503", "SDX"),
    ("U504", "SDA"), ("U505", "SDA"), ("R504", "2"))
net("SENS_SCL", ("U201", "P1.03"), ("U502", "SCX"), ("U503", "SCX"),
    ("U504", "SCL"), ("U505", "SCL"), ("R505", "2"))
net("IMU_INT", ("U201", "P1.10"), ("U503", "INT1"))
net("BARO_INT", ("U201", "P1.12"), ("U502", "INT"))
net("INT_OPT", ("U505", "INT"), ("R112", "2"))

net("SWDIO", ("U201", "SWDIO"), ("J201", "SWDIO"), ("J202", "SWDIO"))
net("SWDCLK", ("U201", "SWDCLK"), ("J201", "SWDCLK"), ("J202", "SWDCLK"))
net("MOD_RESET", ("U201", "RESET"), ("J201", "RESET"), ("J202", "nRESET"))
net("CON_TX", ("U201", "P1.00"), ("TP201", "1"))
net("CON_RX", ("U201", "P1.31"), ("TP202", "1"))

# ------------------------------------------------------------ armazenamento
net("NOR_SCK", ("U201", "P2.01"), ("R506", "1"))
net("NOR_SCK_F", ("R506", "2"), ("U501", "SCLK"))
net("NOR_MOSI", ("U201", "P2.02"), ("R507", "1"))
net("NOR_MOSI_F", ("R507", "2"), ("U501", "SI_IO0"))
net("NOR_MISO", ("U201", "P2.04"), ("R508", "1"))
net("NOR_MISO_F", ("R508", "2"), ("U501", "SO_IO1"))
net("NOR_CS", ("U201", "P2.05"), ("U501", "CS_N"), ("R501", "2"))
net("NOR_WP", ("U501", "WP_N_IO2"), ("R502", "2"))
net("NOR_HOLD", ("U501", "HOLD_N_IO3"), ("R503", "2"))

# ------------------------------------------------------------ display
net("DISP_SCK", ("U201", "P3.03"), ("J401", "SCLK"))
net("DISP_MOSI", ("U201", "P3.00"), ("J401", "SI"))
net("DISP_CS", ("U201", "P3.02"), ("J401", "SCS"), ("R405", "1"))
net("DISP_EXTCOMIN", ("U201", "P3.06"), ("J401", "EXTCOMIN"))
net("DISP_ON", ("U201", "P3.05"), ("J401", "DISP"), ("R404", "1"))
net("DISP_PWR_EN", ("U201", "P3.07"), ("R403", "1"))
net("DISP_VDD", ("JP401", "2"), ("J401", "VDD"), ("J401", "VDDA"), ("J401", "EXTMODE"),
    ("C404", "1"))
net("DISP_VDD_SEL", ("JP401", "1"), ("JP104", "2"))
net("BL_PWM", ("U201", "P3.08"), ("Q401", "G"), ("R402", "1"))
# um resistor por catodo: quatro LEDs em paralelo num resistor so repartem
# a corrente pela dispersao de V_F, e quem tem menos V_F leva mais
net("BL_K1", ("J402", "1"), ("DS401", "LUZ_K1"), ("R406", "1"))
net("BL_K2", ("J402", "2"), ("DS401", "LUZ_K2"), ("R407", "1"))
net("BL_K3", ("J402", "3"), ("DS401", "LUZ_K3"), ("R408", "1"))
net("BL_K4", ("J402", "4"), ("DS401", "LUZ_K4"), ("R409", "1"))
net("BL_CATODO", ("R406", "2"), ("R407", "2"), ("R408", "2"), ("R409", "2"),
    ("Q401", "D"))
ABERTO["J402"] = ("a ordem das cinco vias da luz nao esta em fonte nenhuma: as vias 1 e 2 "
                  "aqui sao posicao, nao pinagem, e a peca tambem esta em aberto")

# the panel itself, wired to the signal connector contact by contact
for _n in ("SCLK", "SI", "SCS", "EXTCOMIN", "DISP", "VDDA", "VDD", "EXTMODE",
           "VSS", "VSSA"):
    NETS.setdefault(f"FPC_{_n}", []).extend([("J401", _n), ("DS401", _n)])

# ------------------------------------------------------------ GNSS
# Receptor e MCU no mesmo 3V0 desde 2026-09-26: as quatro linhas vao direto,
# sem o tradutor de nivel que existia quando o receptor era de 1,8 V.
net("GNSS_TX", ("U201", "P1.04"), ("U301", "RXD"))
net("GNSS_EXTINT", ("U201", "P1.08"), ("U301", "EXTINT"))
net("GNSS_RX", ("U201", "P1.05"), ("U301", "TXD"))
net("GNSS_TIMEPULSE", ("U201", "P1.09"), ("U301", "TIMEPULSE"))
net("GNSS_RESET_N", ("U201", "P1.06"), ("U301", "RESET_N"))
net("RF_IN", ("U301", "RF_IN"), ("L301", "2"), ("C302", "1"))
# The antenna side of the pi network stops at the jumper, and the jumper
# decides which of the two antennas the line reaches. Three nets, not one:
# with a single net both branches hang off the line at once and the one not
# fitted is a stub.
net("RF_ANT", ("L301", "1"), ("C301", "1"), ("JP301", "COMUM"))
net("RF_UFL", ("JP301", "UFL"), ("J302", "FEED"))
net("RF_CHIP", ("JP301", "CHIP"), ("E301", "FEED"))
# Os pinos 1 e 2 da antena de chip sao terra E sintonia: vao ao plano
# por C305 e C306, nao direto. Sao as posicoes [8] e [9] do circuito da
# ficha da Unictron.
net("ANT_T1", ("E301", "GND_T1"), ("C305", "1"))
net("ANT_T2", ("E301", "GND_T2"), ("C306", "1"))

# ------------------------------------------------------------ interface
net("KEY_L", ("U201", "P1.26"), ("R604", "1"))
net("KEY_L_SW", ("R604", "2"), ("SW601", "1"), ("C601", "1"))
net("KEY_C", ("U201", "P1.27"), ("R605", "1"))
net("KEY_C_D", ("R605", "2"), ("D107", "A"))
net("KEY_C_SW", ("D107", "K"), ("SW602", "1"), ("C602", "1"),
    ("U101", "SHPHLD"))
net("KEY_R", ("U201", "P1.30"), ("R606", "1"))
net("KEY_R_SW", ("R606", "2"), ("SW603", "1"), ("C603", "1"))

net("RGB_R", ("U201", "P1.16"), ("Q601", "G"), ("R609", "1"))
net("RGB_G", ("U201", "P1.19"), ("Q602", "G"), ("R610", "1"))
net("RGB_B", ("U201", "P1.22"), ("Q603", "G"), ("R611", "1"))
net("RGB_R_D", ("D601", "K_R"), ("R601", "1"))
net("RGB_G_D", ("D601", "K_G"), ("R602", "1"))
net("RGB_B_D", ("D601", "K_B"), ("R603", "1"))
net("RGB_R_Q", ("R601", "2"), ("Q601", "D"))
net("RGB_G_Q", ("R602", "2"), ("Q602", "D"))
net("RGB_B_Q", ("R603", "2"), ("Q603", "D"))

net("BUZ_A", ("U201", "P1.25"), ("R607", "1"))
net("BUZ_A_LS", ("R607", "2"), ("LS601", "A"))
net("BUZ_B", ("U201", "P1.28"), ("R608", "1"))
net("BUZ_B_LS", ("R608", "2"), ("LS601", "B"))

# ------------------------------------------------------------ terra
net("GND",
    ("J101", "GND_A1"), ("J101", "GND_A12"), ("J101", "GND_B1"), ("J101", "GND_B12"),
    # The shell, which had no pin in the part until 2026-09-24 and so left the
    # four shell pads of the land pattern floating. Tied straight to GND, not
    # through the usual 1 M / 4,7 nF: that network exists to break a ground
    # loop between two mains-powered boxes, and this one runs off a cell.
    ("J101", "SHELL"),
    ("D101", "GND"), ("D102", "GND1"), ("D102", "GND2"),
    ("U101", "AVSS"), ("U101", "PVSS1"), ("U101", "PVSS2"), ("U102", "GND"), ("U103", "AGND"), ("U103", "PGND"), ("U103", "AGND2"),
    ("U103", "SETBK"), ("U103", "REG_D0"), ("U103", "REG_D1"),
    ("R116", "2"), ("R119", "2"), ("R121", "2"),
    ("R122", "2"), ("R123", "2"), ("C119", "2"), ("C120", "2"),
    ("C121", "2"),
    ("U104", "GND"), ("U104", "PAD"), ("J102", "2"), ("J102", "5"), ("R106", "2"), ("R125", "2"), ("U105", "GND"),
    ("C122", "2"), ("C123", "2"), ("C124", "2"), ("C125", "2"), ("C126", "2"),
    ("C129", "2"),
    ("U201", "GND"), ("U201", "GND3"), ("U201", "GND10"), ("U201", "GND11"),
    ("U201", "GND20"), ("U201", "GND_D0"), ("U201", "GND_E0"),
    ("U201", "GND_F0"), ("J201", "GND"), ("J202", "GND1"), ("J202", "GND2"),
    ("TP203", "1"),
    ("U301", "GND"), ("U301", "GND2"), ("U301", "GND3"),
    ("C301", "2"), ("C302", "2"), ("C303", "2"), ("C304", "2"),
    ("C305", "2"), ("C306", "2"),
    ("U501", "GND"), ("U502", "VSSIO"), ("U503", "GND"), ("U503", "GNDIO"),
    ("U503", "SDO"), ("U504", "VSA"), ("U505", "GND"), ("U505", "ADDR"),
    ("DS401", "VSS"), ("DS401", "VSSA"),
    ("Q401", "S"), ("Q601", "S"), ("Q602", "S"), ("Q603", "S"),
    ("R402", "2"), ("R403", "2"), ("R404", "2"), ("R405", "2"),
    ("R609", "2"), ("R610", "2"), ("R611", "2"),
    ("R105", "2"), ("C601", "2"), ("C602", "2"), ("C603", "2"),
    ("SW601", "2"), ("SW602", "2"), ("SW603", "2"),
    *[(f"PV10{i}", "N") for i in range(1, 7)],
    *[(c, "2") for c in ("C101", "C102", "C103", "C104", "C105", "C106", "C110",
                         "C111", "C114", "C115", "C116", "C117", "C118",
                         "C201", "C210", "C404", "C501", "C502", "C503")],
    ("J302", "GND"), ("D105", "GND"),
    ("J103", "GND"),
    ("R102", "2"), ("R103", "2"),
    ("C107", "2"), ("C108", "2"), ("C109", "2"), ("C113", "2"))

# ------------------------------------------------------------ nao ligados
# Pins that the documents leave with no destination, and why. Writing them
# here keeps them off the drawing as loose ends and out of the netlist as
# silent errors.
SEM_LIGACAO: dict[str, str] = {
    "U101 GPIO0, GPIO1, GPIO2, GPIO4": "GPIO do PMIC que este projeto nao usa; "
        "CONFERIR na ficha o estado de reset, porque entrada flutuante vira "
        "fuga e o orcamento solar depende da corrente de repouso",
    "U101 LED2": "o terceiro dreno de LED do PMIC, sem LED",
    "U103 SETPG, SETHYST, PGOOD, LLD, BACK_UP": "PGOOD e LLD sao saidas sem "
        "consumidor, SETPG e SETHYST sao os ajustes do PGOOD, BACK_UP e a "
        "celula primaria que nao existe (SETBK no AGND, como a tabela 5 da "
        "ficha manda). CONFERIR na Rev. A se SETPG/SETHYST abertos sao aceitos",
    "U201 RF": "o pino 2 do modulo e para antena externa; o ME54BS13 tem "
        "antena de PCB integrada, entao fica aberto",
    "U301 SDA, SCL": "o receptor fala por UART; a interface I2C dele nao e usada",
    "U301 SAFEBOOT_N": "aberto e o nivel alto que NAO entra em safeboot; "
        "nada de pull-down aqui",
    "U301 LNA_EN, VCC_RF": "o MAX-F10S ja tem SAW, LNA e SAW dentro do modulo",
    "U301 VIO_SEL": "aberto poe o V_IO na faixa de 2,7 a 3,6 V (manual de "
        "integracao UBXDOC-963802114-12892, 4.1.2 e tabela 35, opcao 1); no GND "
        "seria a faixa de 1,8 V, que este projeto deixou em 2026-09-26",
    "U503 INT2": "a segunda interrupcao do IMU nao e usada",
    "U503 OCSB, OSDO": "a Bosch manda deixar abertos com a interface OIS "
        "desligada",
    "J101 SBU1, SBU2": "as duas linhas laterais do USB-C, sem uso em USB 2.0",
    "J201 SWO": "o pino 6 do TC2030 e o SWO, saida de trace do alvo. A sonda nunca o aciona, entao deixa-lo aberto nao quebra nada; leva-lo a um pad de trace do modulo daria printf por ITM no bring-up, e falta descobrir qual pad do ME54BS13 expoe o SWO",
    "J202 SWO": "o pino 6 do conector Cortex de 10 vias e o SWO, como o 6 do TC2030: mesma pendencia, qual pad do ME54BS13 expoe o SWO",
    "J202 KEY": "o pino 7 e a chave do conector blindado: nao existe pino ali",
    "J202 TDI": "o pino 8 e TDI/NC, so JTAG; o nRF54LM20A e SWD",
    "J202 GNDDetect": "o pino 9 e o GNDDetect da ARM: a sonda o le para saber se ha alvo; fica aberto, como nas placas de referencia da Nordic",
    "D102 NC1 a NC4": "a TI os reserva para roteamento reto, nao sao pinos",
}

# The nPM1300's VDDIO (pin 12) is the supply of its TWI and of its GPIOs. It
# is a real pin that this project had never wired, and 08-layout.md carries
# "domain of the nPM1300's digital I/O" as an open question. It goes to 3V0
# so that the bus matches the MCU's 3.0 V.
NETS["3V0"].append(("U101", "VDDIO"))
# PVDD (pin 4) is the power input of both bucks.
NETS["VSYS"].append(("U101", "PVDD"))

ABERTO["L103 do ADP5091"] = (
    "22 uH entre VIN e SW, Isat >= 390 mA (ficha), SEM peca escolhida na "
    "LCSC; o AEM10900 e o seu 4,7 uH sairam em 2026-09-25, e os documentos "
    "02, 04, 05, 13, 14, 15 e 19 ainda dimensionam o colhedor antigo")
ABERTO["corte termico abaixo de 0 graus"] = (
    "o comparador U105 so corta o lado quente; o AEM10900 recusava carga "
    "abaixo de 0 graus e o ADP5091 nao tem entrada de temperatura. Segundo "
    "comparador (TLV7032) com a referencia do frio, ou aceitar o risco: "
    "decisao do dono, registrada em 01")
ABERTO["VDDIO do nPM1300"] = (
    "ligado ao 3V0, que e a saida do BUCK2 do proprio CI: ate o BUCK2 partir, "
    "o TWI e os GPIO do PMIC ficam sem alimentacao. E o arranjo da referencia "
    "da Nordic, mas a consequencia na partida nao foi verificada")

# The test points of 06-conectores-e-pontos-de-teste.md hang on the rails
# they measure. Appended here instead of being typed into each net() call
# above so that the list lives in ONE place - parts.TESTE - and a point that
# is added there cannot be forgotten here.
import parts as _P  # noqa: E402

for _tp, _rede, _porque in _P.TESTE:
    if _rede not in NETS:
        raise SystemExit(f"{_tp} mede {_rede}, que nao existe na lista de nos")
    NETS[_rede].append((_tp, "1"))


def resumo() -> str:
    pins = sum(len(v) for v in NETS.values())
    return (f"{len(NETS)} nos, {pins} ligacoes de pino, "
            f"{len(ABERTO)} pontos em aberto")


if __name__ == "__main__":
    print(resumo())
    for k, v in ABERTO.items():
        print(f"  em aberto: {k}: {v}")
