Guiimartinho/gnss-bike-computer/hardware_gnssbike/cad/parts.py

#!/usr/bin/env python3
"""Every part of the board, with its pins.

The reference designators and the values come from
hardware_gnssbike/05-materiais.md; the pin names come from
hardware_gnssbike/03-netlist.md and from the manufacturers' datasheets.

Pin NUMBERS are the dangerous part. A wrong number is a wrong netlist and a
wrong board, so a part whose numbering has not been read off the datasheet
carries `confirmed=False`, and its symbol says so on the drawing. Nothing here
is guessed: where the number is unknown the pin keeps its name as its number
and the part is marked.
"""

from __future__ import annotations

from sch_lib import Part, Pin

# Sides: L and R for signals, T for supply, B for ground - the usual reading
# order of a schematic, and what keeps the wires off the bodies.
L, R, T, B = "L", "R", "T", "B"

PARTS: dict[str, Part] = {}
UNCONFIRMED: set[str] = set()


def add(ref: str, value: str, pins: list[tuple], *, confirmed: bool,
        note: str = "", footprint: str = "", lcsc: str = "") -> Part:
    """pins: (number, name, etype, side). number None means 'not read yet'."""
    ps = []
    for number, name, etype, side in pins:
        ps.append(Pin(str(number) if number is not None else name, name, etype, side))
    if not confirmed:
        UNCONFIRMED.add(ref)
        note = (note + " | PINAGEM NAO CONFIRMADA NA FICHA").strip(" |")
    p = Part(ref, value, tuple(ps), footprint=footprint, note=note, lcsc=lcsc)
    PARTS[ref] = p
    return p


def passive(ref: str, value: str, note: str = "", vertical: bool = False,
            lcsc: str = "") -> Part:
    """A two-terminal part. Pins 1 and 2 are the two ends, which is universal."""
    sides = (T, B) if vertical else (L, R)
    return add(ref, value, [(1, "1", "passive", sides[0]), (2, "2", "passive", sides[1])],
               confirmed=True, note=note, lcsc=lcsc)


# ---------------------------------------------------------------- folha 1
# The board is made AND assembled at JLCPCB, so every part here has to be one
# LCSC stocks - the owner's rule of 2026-09-24, with the Minew module and the
# solar cells as the only exceptions. That is why the `lcsc=` field exists and
# why several parts below are not the ones the earlier drafts chose.
#
# The USB-C receptacle was the Molex 2036150003: 309 in the world at US$ 5,69.
# This one is the most used USB-C of JLCPCB's whole catalogue - 91.943 in
# stock at US$ 0,186 - and it carries the same 16 of the 24 USB-IF contacts.
# A2, A3, A10, A11, B2, B3, B10 and B11 (the SuperSpeed pairs) do not exist.
#
# S1 is the shell. It was not in the part before, so the four shell pads of
# the land pattern sat unconnected; a USB shell that floats is an antenna on
# the one edge of the board that leaves the case.
add("J101", "HRO TYPE-C-31-M-12", [
    ("A4", "VBUS_A4", "power_out", T), ("A9", "VBUS_A9", "power_out", T),
    ("B4", "VBUS_B4", "power_out", T), ("B9", "VBUS_B9", "power_out", T),
    ("A5", "CC1", "passive", R), ("B5", "CC2", "passive", R),
    ("A6", "DP_A6", "passive", R), ("B6", "DP_B6", "passive", R),
    ("A7", "DM_A7", "passive", R), ("B7", "DM_B7", "passive", R),
    ("A8", "SBU1", "passive", R), ("B8", "SBU2", "passive", R),
    ("A1", "GND_A1", "power_out", B), ("A12", "GND_A12", "power_out", B),
    ("B1", "GND_B1", "power_out", B), ("B12", "GND_B12", "power_out", B),
    ("S1", "SHELL", "passive", B),
], confirmed=True, lcsc="C165948",
    note="USB-C de 16 contatos, USB 2.0, SMD de borda, 20 V / 5 A, 10.000 "
         "ciclos. Substitui o Molex 2036150003 (309 unidades, US$ 5,69): "
         "corpo de 7,35 mm no lugar de 8,58, land pattern proprio, e a "
         "abertura da caixa muda. CONFERIR o desenho antes de fabricar")

# ESD761 is gone: zero stock at LCSC and at JLCPCB, both sides. This is the
# same X1SON-2 land pattern and a better capacitance (0,42 pF against 1,1),
# but it is NOT the same part: the ESD761 was a bidirectional clamp with 24 V
# of standoff and this one is UNIDIRECTIONAL with 5,5 V. Two consequences:
# the symbol is polarised, so orientation now matters on the board and on the
# silkscreen; and a faulty cable that puts 20 V on a CC line is no longer
# survivable. The bidirectional part that is in stock, TPD1E10B06DPYR
# (C48260, 299.830 units), costs 12 pF instead of 0,42 - fine for CC, which
# is hundreds of kbps, and not fine for D+/D-.
add("D101", "TPD1E05U06DPYR", [
    (1, "IO", "passive", L), (2, "GND", "passive", B),
], confirmed=True, lcsc="C436349",
    note="TVS do VBUS, X1SON-2, 0,42 pF, 5,5 V de trabalho, clamp em 14 V. "
         "UNIDIRECIONAL: o ESD761 que estava aqui era bidirecional de 24 V e "
         "esta com estoque zero. Orientacao passa a importar")

# TPD4E05U06 in DQA is a USON of TEN pins, 1.0 x 2.5 mm: four ESD channels,
# two grounds and four pins TI means to be used for straight-through routing,
# which is why they are passive here and not no_connect.
add("D102", "TPD4E05U06DQAR", [
    (1, "D1P", "passive", L), (2, "D1N", "passive", L), (3, "GND1", "passive", B),
    (4, "D2P", "passive", R), (5, "D2N", "passive", R), (6, "NC1", "passive", R),
    (7, "NC2", "passive", R), (8, "GND2", "passive", B),
    (9, "NC3", "passive", R), (10, "NC4", "passive", R),
], confirmed=True, lcsc="C138714", note="ESD de CC1, CC2, D+ e D-")

# nPM1300 Product Specification v1.1, table 35 and figure 50, QFN32.
# Note VSET1 and VSET2, not RVSET; and VDDIO on pin 12, which is the supply of
# the TWI and of the GPIOs - the domain 08-layout.md still carries as an open
# question. It is a real pin and it needs a rail.
add("U101", "nPM1300-QEAA", [
    (1, "VOUT1", "power_out", R), (2, "PVSS1", "power_in", B),
    (3, "SW1", "passive", R), (4, "PVDD", "power_in", L),
    (5, "SW2", "passive", R), (6, "PVSS2", "power_in", B),
    (7, "GPIO0", "bidirectional", R), (8, "GPIO1", "bidirectional", R),
    (9, "GPIO2", "bidirectional", R), (10, "GPIO3", "bidirectional", R),
    (11, "GPIO4", "bidirectional", R), (12, "VDDIO", "power_in", T),
    (13, "SDA", "bidirectional", L), (14, "SCL", "input", L),
    (15, "SHPHLD", "input", L), (16, "VSET2", "input", L),
    (17, "VSET1", "input", L), (18, "NTC", "input", L),
    (19, "VBAT", "power_in", L), (20, "VSYS", "power_out", R),
    (21, "VBUS", "power_in", L), (22, "VBUSOUT", "power_out", R),
    (23, "CC1", "input", L), (24, "CC2", "input", L),
    (25, "LED0", "open_collector", R), (26, "LED1", "open_collector", R),
    (27, "LED2", "open_collector", R), (28, "LSIN1", "power_in", L),
    (29, "LSOUT1", "power_out", R), (30, "LSIN2", "power_in", L),
    (31, "LSOUT2", "power_out", R), (32, "VOUT2", "power_out", R),
    (33, "AVSS", "power_in", B),
], confirmed=True,
    note="PMIC: carregador, 2 bucks, 2 chaves de carga. FICA no QFN-32 e vai "
         "por CONSIGNACAO na JLCPCB: estoque zero na LCSC nos dois carreteis. "
         "A versao WLCSP-35 (C25346894) tem estoque, mas o passo de bolas de "
         "0,419 x 0,440 mm e menor que a via de 0,45 da placa e obrigaria "
         "via-in-pad na placa inteira, provavel ida para 6 camadas, dobro da "
         "resistencia termica (24,2 para 48,3 C/W) e anteparo de luz na caixa "
         "(secao 5.2 da ficha: o WLCSP e sensivel a luz e este aparelho tem "
         "painel solar). Nao compensa")

passive("L101", "2,2 uH", "indutor do BUCK1", lcsc="C337891")
passive("L102", "2,2 uH", "indutor do BUCK2", lcsc="C337891")

# MAX17262 datasheet 19-100308 rev 0, WLP of nine balls. The 7 mOhm sense is
# internal, between BATT and SYS: the electrical table gives RSNS = 7 mOhm and
# the ordering information lists only "Internal Sensing" parts.
add("U102", "MAX17262REWL", [
    ("A1", "TH", "input", L), ("A2", "BATT", "power_in", L),
    ("A3", "NC", "no_connect", R), ("B1", "SCL", "input", L),
    ("B2", "ALRT", "open_collector", R), ("B3", "SYS", "power_out", R),
    ("C1", "SDA", "bidirectional", L), ("C2", "REG", "power_out", R),
    ("C3", "GND", "power_in", B),
], confirmed=True, lcsc="C5328777", note="medidor de carga; sensor de 7 mOhm INTERNO entre BATT e SYS")

# O colhedor solar passou do e-peas AEM10900 para o Analog ADP5091 em
# 2026-09-24, e a razao foi disponibilidade: a LINHA E-PEAS INTEIRA esta com
# estoque zero na LCSC - 31 referencias, todas em 0 - e a placa e montada na
# JLCPCB. A DigiKey nunca vendeu a peca.
#
# O ADP5091ACPZ-2-R7 (C579259) faz o mesmo trabalho: boost com MPPT de 0,08 a
# 3,3 V de entrada, partida a frio em 380 mV, carga de celula Li-ion 1S com
# limiar programavel e corte de descarga programavel COM chave que abre de
# verdade entre a bateria e o sistema. O sufixo -2 e o de 300 mA de pico do
# indutor; o -1 e de 200/250 e ficaria em cima do nosso ponto.
#
# O QUE SE PERDE, e nao e pouco:
#   - I2C. Nao ha barramento nenhum: tudo e resistor. O `status.solar_mw` da
#     tela sai, ou passa a ser estimado pela corrente liquida que o MAX17262
#     ja mede. O driver aem10900.c do firmware, 361 linhas, desaparece junto
#     com o binding, os registradores e o no do devicetree.
#   - O NTC. O AEM10900 tinha TH_MON e cortava a carga fora de 0 a 45 graus
#     sozinho; este nao tem entrada de temperatura nenhuma. O corte volta por
#     um comparador externo - ver U105 abaixo -, porque a caixa ao sol passa
#     de 45 graus e carregar Li-ion acima disso e questao de seguranca.
#
# Pinagem da tabela 5 da ficha Rev. A (D14145-0-5/17(A)), paginas 8 e 9. O
# pad exposto NAO tem numero na ficha e a nota 1 da figura 3 manda liga-lo ao
# AGND.
# CORRIGIDO em 2026-09-25, e era o segundo erro de placa do dia.
#
# Uma primeira leitura desta ficha trocou SEIS pinos, em duas permutacoes de
# tres: 2/4/6 (SETHYST, SETSD, TERM) e 7/9/10 (MPPT, VIN, AGND). O erro so
# apareceu porque o simbolo `Battery_Management:ADP5091` da biblioteca do
# KiCad discordava, e a conferencia por NUMERO passava - os numeros batem, os
# sinais e que nao.
#
# A ficha decidiu: Tabela 5, paginas 8 e 9 da Rev. A (D14145-0-5/17(A)), com
# a Figura 3 confirmando lado por lado. O KiCad esta certo nos 24. Tres
# leituras independentes fecharam: a tabela remontada pela geometria das
# colunas, a autoconsistencia de cada descricao (a do pino 2 cita "the SETSD
# pin", a do 6 cita "between SETPG and SETHYST") e a Figura 3.
#
# O que iria para o cobre se ficasse como estava: o divisor de MPPT ligado ao
# pino 7, que e o AGND - curto-circuitado ao terra analogico -, o colhedor com
# o indutor de 22 uH e o capacitor de 10 uF no pino 9, que e o MPPT, e o terra
# no pino 10, que e a entrada.
#
# CUIDADO com a Rev. PrA preliminar: a Tabela 5 dela troca 14 e 17, e
# contradiz a propria Figura 2. Nao serve para nada.
add("U103", "ADP5091ACPZ-2", [
    (1, "REF", "passive", L), (2, "SETSD", "input", L),
    (3, "SETBK", "input", L), (4, "TERM", "input", L),
    (5, "SETPG", "input", L), (6, "SETHYST", "input", L),
    (7, "AGND", "power_in", B), (8, "CBP", "passive", B),
    (9, "MPPT", "input", B), (10, "VIN", "power_in", B),
    (11, "LLD", "output", B), (12, "PGND", "power_in", B),
    (13, "SW", "passive", R), (14, "REG_OUT", "power_out", R),
    (15, "REG_FB", "input", R), (16, "SYS", "power_out", R),
    (17, "BAT", "bidirectional", R), (18, "BACK_UP", "power_in", R),
    (19, "PGOOD", "output", T), (20, "VID", "input", T),
    (21, "MINOP", "input", T), (22, "DIS_SW", "input", T),
    (23, "REG_D1", "input", T), (24, "REG_D0", "input", T),
    # O pad exposto e o pad 25 no footprint do KiCad, e a nota 1 da figura 3
    # da ficha manda liga-lo ao AGND.
    # A ficha NAO da numero ao pad exposto - a linha dele na
    # Tabela 5 tem a coluna vazia -, e manda liga-lo ao AGND.
    # O 25 e convencao de CAD: e como o footprint do KiCad o
    # numera, e o simbolo o chama AGND, empilhado no pino 7.
    (25, "AGND2", "power_in", B),
], confirmed=True, lcsc="C579259",
    note="colhedor solar com MPPT, LFCSP-24 de 4 x 4 mm. Sem I2C e sem NTC: "
         "tudo por resistor. O pad exposto vai ao AGND (nota 1 da figura 3)")

# DEFEITO ABERTO, aberto em 2026-09-24 com a troca do colhedor solar.
#
# O AEM10900 tinha o pino TH_MON e cortava a carga fora de 0 a 45 graus
# sozinho, em hardware, sem firmware nenhum. O ADP5091 NAO TEM entrada de
# temperatura, e a caixa ao sol passa de 45 graus - carregar uma celula
# Li-ion acima disso e questao de seguranca, nao de rendimento.
#
# A saida obvia seria um comparador de nanoamperes (TLV7031, C2869832, 315 nA)
# lendo o NTC RT101 e puxando o DIS_SW. NAO E TAO SIMPLES, e a conta que
# derruba a ideia e esta:
#
#   O divisor do NTC fica LIGADO O TEMPO TODO. Com o RT101 de 10 k e um
#   resistor de 22 k, a 4,2 V isso e 4,2 / 32 k = 131 uA CONTINUOS - mais do
#   que o aparelho inteiro dormindo. O AEM10900 nao tinha esse problema
#   porque ligava o divisor so no instante da medida.
#
# Alem disso o DIS_SW e ativo em ALTO e a saida do TLV7031 e dreno aberto,
# que so puxa para baixo: ligar os dois direto faz o comparador frio segurar
# o DIS_SW em zero e ANULAR o bloqueio pelo USB. Seria preciso um diodo de
# OU e um divisor de referencia, mais duas ou tres pecas.
#
# CAMINHOS, para decidir com o dono e nao no meio de um commit:
#   a) NTC de 100 k ou 470 k no lugar do de 10 k, o que baixa a fuga para
#      13 ou 3 uA, com o custo de rever a curva e a precisao;
#   b) alimentar o divisor por um pino que so fique de pe quando ha sol -
#      por exemplo o PGOOD do proprio ADP5091 -, o que zera a fuga no escuro;
#   c) aceitar que o corte fique com o nPM1300 e o firmware, registrando que
#      uma placa travada carregaria a celula quente;
#   d) chave analogica ou MOSFET ligando o divisor so periodicamente.
#
# Ate escolher, o caminho solar NAO TEM corte termico. Isto esta em
# 09-dry-run-da-pcb.md e em 10-status-do-port.md.

# O indutor do boost do ADP5091. A ficha e explicita: 22 uH +-20 % nominais,
# porque o controle de pico interno foi dimensionado para esse valor, e
# corrente de saturacao ao menos 30 % acima do pico esperado - com os 300 mA
# de pico da variante -2, Isat >= 390 mA. O 4,7 uH que estava aqui era do
# AEM10900 e NAO SERVE. O encapsulamento sobe de 2,5 x 2,0 para 3 x 3 mm.
passive("L103", "22 uH", "indutor do boost do ADP5091, entre VIN e SW; "
                       "Isat >= 390 mA. ESCOLHER a peca na LCSC")

# TPS7A02 in DQN is an X2SON of four pins, 1.0 x 1.0 mm, not a SOT-563.
add("U104", "TPS7A0218PDQN", [
    (1, "OUT", "power_out", R), (2, "GND", "power_in", B),
    (3, "EN", "input", L), (4, "IN", "power_in", L),
    (5, "PAD", "power_in", B),
], confirmed=True, lcsc="C2862166", note="LDO de 1,8 V do VBCKP do receptor; pad termico ao GND")

# A alimentacao do receptor GNSS, decidida duas vezes em 2026-09-26. De
# manha: o BUCK1 do nPM1300 e de +-5 % (1,71-1,89 V) e a tabela 35 do manual
# do MAX-F10S pede +-2 % para o projeto de 1,8 V, entao entrou um segundo
# TPS7A02 de 1,8 V +-1 % (U106) alimentado do 3V0. De tarde a conta do
# consumo mostrou que o LDO custava 35 mW na bateria (o receptor passava a
# ser pago a 3,0 V com 1,2 V queimados no LDO) e a opcao 1 da mesma tabela
# custa menos: VCC e V_IO no 3V0, VIO_SEL aberto, 19 mA a 3,0 V (57 mW, 10 a
# mais que a 1,8 V; docs/15) e sem tradutor de nivel. O dono escolheu a
# opcao 1; sairam o U106 com os seus dois capacitores e o TXU0204 (U302)
# com os seus dois. O BUCK1 fica montado e sem carga (nets.py explica).

# KXOB25-05X3F: the datasheet does NOT number the terminals. The silkscreen on
# the back marks + on one pad and - on the other, and 1 and 2 below follow the
# usual convention; if the footprint numbers them the other way, this follows.
for i in range(1, 7):
    add(f"PV10{i}", "KXOB25-05X3F", [
        (1, "P", "passive", R), (2, "N", "passive", B),
    ], confirmed=False,
        note="modulo solar de 3 celulas, 23 x 8 mm; a ficha nao numera os "
             "terminais, so marca + e - na serigrafia do verso")

# JST SH (1,0 mm, side entry, 2,9 mm tall) since 2026-09-26, on the FRONT;
# it was the GH SM06B-GHS-TB (1,25 mm, 4,25 mm tall) on the back. With the
# board at 95 mm the strip of the back under the cell's shadow could not
# hold the GH, the 12 mm buzzer and the M2 hole together (the buzzer cannot
# get within 5 mm of the module's antenna keep-out), and on the front the
# case's lid leaves 3,8 mm: the GH does not fit, the SH does. The pack
# maker still decides the pinout, and now the pitch too.
add("J102", "JST SM06B-SRSS-TB", [
    (1, "1", "passive", R), (2, "2", "passive", R), (3, "3", "passive", R),
    (4, "4", "passive", R), (5, "5", "passive", R), (6, "6", "passive", R),
], confirmed=True,
    note="conector da celula, 6 vias, JST SH passo 1,0 mm, entrada lateral, "
         "2,9 mm de altura, na face da frente; o catalogo da JST nao da "
         "funcao a contato nenhum, e quem decide e o fabricante do pack. "
         "LCSC a conferir (era o GH C133065)")

passive("RT101", "10 k B3380", "NTC do corte termico, na face de tras sob a celula; agora "
                                       "lido pelo comparador U105, nao por pino do colhedor", lcsc="C209959")
# APT1608SURCK spec DSAD0926 rev V.22A: the cathode bar is on terminal 1, so
# the ANODE IS TERMINAL 2. A draft of this schematic had it the other way.
add("D103", "APT1608SURCK", [(1, "K", "passive", L), (2, "A", "passive", R)],
    confirmed=True, note="LED de carga; anodo no terminal 2")
add("D104", "APT1608SURCK", [(1, "K", "passive", L), (2, "A", "passive", R)],
    confirmed=True, note="LED de erro; anodo no terminal 2")


# O divisor que faz o USB bloquear a carga solar em hardware. O levantamento
# da ficha confirmou a perna de serie: 100 k de VBUSOUT ao DIS_SW e 1 M do
# DIS_SW ao AGND da 4,09 V no pino com 4,5 V de VBUS, acima do limiar de 1 V.
# Invertido daria 0,41 V e o USB NAO bloquearia - funcionaria ao contrario.
# O 1 M para o terra nao e opcional: sem ele o pino flutua sem USB.
passive("R102", "47 k", "VSET1: BUCK1 em 1,8 V")
passive("R103", "150 k", "VSET2: BUCK2 em 3,0 V")
passive("R104", "100 k", "serie do DIS_SW, de VBUSOUT")
passive("R105", "180 k", "do DIS_SW ao AGND; sem ele o pino flutua sem USB")

# A rede de resistores do ADP5091. Todos os divisores somam mais de 6 MOhm,
# que e o que a equacao 7 da ficha exige para nao comer corrente de repouso.
#
# MPPT (equacao 1): a razao e o resistor de BAIXO sobre o total, e inverter
# poe o MPPT em 0,19 em vez de 0,81. 18 M embaixo e 4,3 M em cima dao 0,80717
# contra o alvo de 0,807 (1,67 V de MPP sobre 2,07 V em aberto): 0,9 mV de
# erro. Sao valores E24 e somam os mesmos 22,3 MOhm da figura 45 da ADI.
passive("R116", "18 M", "ROC1 do MPPT, do pino MPPT ao AGND")
passive("R117", "4,3 M", "ROC2 do MPPT, de VIN ao pino MPPT")

# TERM (equacao 6): VBAT_TERM = 1,5 x VINT_REF x (1 + RTERM1/RTERM2), com
# VINT_REF de 1,0 V, que e como a ADI monta a tabela 8 dela.
#
# 3,93 V NOMINAIS, E NAO 4,05, DE PROPOSITO. A referencia interna tem +-5,5 %
# de espalhamento especificado (0,955 a 1,067 V) e ele vai INTEIRO para o
# limiar: programando 4,05 nominais, o pior caso e 4,32 V, acima do limite de
# 4,2 V da celula - e este comparador e o UNICO controle de terminacao do
# caminho solar. Com 3,93 nominais o pior caso fica em 4,19 V.
#
# Nao e perda: o AEM10900 ja estava configurado para 3,90 V, o perfil Li-ion
# long life, e o nPM1300 continua fazendo a carga fina pelo USB. Assim o
# solar nunca decide o topo da celula.
passive("R118", "4,32 M", "RTERM1, do pino REF ao pino TERM (figura 42 da ficha)")
passive("R119", "2,67 M", "RTERM2, do pino TERM ao AGND")

# SETSD (equacao 8): VSETSD = VINT_REF x (1 + RSD1/RSD2). 3,00 V nominais,
# pior caso de 2,87 a 3,20 V - seguro nos dois extremos. Sao os valores da
# linha de 3 V da tabela 8 da propria ADI. A histerese e INTERNA (115 kOhm
# tipicos) e da cerca de 112 mV com estes divisores.
passive("R120", "6,65 M", "RSD1, do pino REF ao pino SETSD (figura 42 da ficha)")
passive("R121", "3,32 M", "RSD2, do pino SETSD ao AGND")

# MINOP: R = V_MINOP / 2,00 uA. 402 k da 0,804 V, ou seja o boost para quando
# a tensao em aberto do painel cai abaixo de 1,0 V - evita chaveamento inutil
# no escuro. Flutuando, o pino poe o CI em modo sem sensoriamento; no AGND,
# desabilita a funcao. Nenhum dos dois e o que queremos.
passive("R122", "402 k", "MINOP: para o boost com o painel abaixo de 1,0 V")

# VID define a tensao do regulador que NAO usamos. Flutuando ele daria 2,5 V;
# um resistor deixa o pino em estado definido, que e o que importa aqui.
passive("R123", "111 k", "VID: estado definido do regulador desabilitado")

# O divisor de temperatura do comparador: o NTC RT101 e o R106 que ja
# estavam na placa para o TH_MON do AEM10900. VALORES A CONFERIR contra o
# limiar de 45 graus e a referencia do comparador.
passive("R106", "4,87 k", "limiar de 45 graus do corte termico: o NTC 10 k B3380 vale 4,90 k a 45 graus, e com este resistor embaixo o meio do divisor cruza VIN/2 exatamente ai"
                        "que le esse divisor ainda nao existe - ver o "
                        "defeito aberto do corte termico, acima")
passive("R107", "4,7 k", "pull-up do PWR_SDA")
passive("R108", "4,7 k", "pull-up do PWR_SCL")
passive("R109", "10 k", "pull-up do PMIC_INT")
passive("R110", "10 k", "pull-up do ALRT do MAX17262")
passive("R112", "10 k", "pull-up do INT do OPT3001")

for n, v in (("C101", "10 uF"), ("C102", "10 uF"), ("C103", "10 uF"), ("C104", "10 uF"),
             ("C105", "10 uF"), ("C106", "10 uF"), ("C107", "10 uF"), ("C108", "10 uF"),
             ("C109", "10 uF"), ("C110", "1 uF"), ("C111", "1 uF"),
             ("C113", "1 uF"), ("C114", "1 uF"), ("C115", "22 uF"), ("C116", "22 uF"),
             ("C117", "22 uF"), ("C118", "0,47 uF")):
    passive(n, v)

passive("JP101", "0 R 1206", "jumper de medicao da corrente da celula")

# ---------------------------------------------------------------- folha 2
# MinewSemi ME54BS13 pad map, from "ME54BS13-nRF54LM20A Datasheet K EN"
# V1.0.0 of 2026-06-23, pages 6 to 9, cross-checked against the module's own
# schematic symbol on page 10 and against an independent KiCad footprint.
#
# The module is a hybrid: 20 CASTELLATED pads numbered 1 to 20 down the two
# long sides, and a 60 pad LGA matrix A0..F9 in the middle. 80 pads, 64 GPIO.
#
# Careful with one thing: three of the port pins this board uses come out on
# the castellated row, not on the matrix - P1.15 to P1.19 and P1.23 and P1.26
# are the ones the module brings to the edge.
PADS_ME54BS13 = {
    # LGA matrix, columns A..F left to right, rows 0..9 top to bottom
    "P0.04": "A0", "P0.02": "B0", "P0.05": "C0",
    "P0.01": "A1", "P0.03": "B1", "P0.06": "C1", "P0.07": "D1",
    "P0.08": "E1", "P0.09": "F1",
    "P0.00": "A2", "P3.03": "B2", "P3.07": "C2", "P3.11": "D2",
    "P3.12": "E2", "P1.14": "F2",
    "P3.04": "A3", "P3.02": "B3", "P3.08": "C3", "P3.10": "D3",
    "P1.10": "E3", "P1.13": "F3",
    "P1.01": "A4", "P3.01": "B4", "P3.06": "C4", "P1.24": "D4",
    "P1.22": "E4", "P1.12": "F4",
    "P1.02": "A5", "P3.00": "B5", "P3.05": "C5", "P3.09": "D5",
    "P1.25": "E5", "P1.11": "F5",
    "P1.06": "A6", "P1.07": "B6", "P1.08": "C6", "P1.09": "D6",
    "P1.28": "E6", "P1.27": "F6",
    "P1.00": "A7", "P1.31": "B7", "P1.05": "C7", "P2.10": "D7",
    "P2.09": "E7", "P2.06": "F7",
    "P1.04": "A8", "P1.03": "B8", "P2.04": "C8", "P2.05": "D8",
    "P2.07": "E8", "P2.08": "F8",
    "P1.30": "A9", "P1.29": "B9", "P2.03": "C9", "P2.02": "D9",
    "P2.01": "E9", "P2.00": "F9",
    # castellated row
    "P1.26": "12", "P1.23": "13", "P1.19": "14", "P1.18": "15",
    "P1.17": "16", "P1.16": "17", "P1.15": "18",
}
# only the port pins this board actually wires
_usados = ("P0.00", "P0.02", "P0.03", "P1.00", "P1.03", "P1.04", "P1.05", "P1.06",
           "P1.08", "P1.09", "P1.10", "P1.12", "P1.16", "P1.19", "P1.22", "P1.25",
           "P1.26", "P1.27", "P1.28", "P1.29", "P1.30", "P1.31", "P2.01", "P2.02",
           "P2.04", "P2.05", "P3.00", "P3.02", "P3.03", "P3.05", "P3.06", "P3.07",
           "P3.08")
_mod = [("7", "USB_DM", "bidirectional", R), ("8", "USB_DP", "bidirectional", R),
        ("9", "VBUS", "power_in", T), ("5", "SWDIO", "bidirectional", R),
        ("6", "SWDCLK", "input", R), ("4", "RESET", "input", L),
        ("2", "RF", "passive", R), ("19", "VDD", "power_in", T),
        ("1", "GND", "power_in", B), ("3", "GND3", "power_in", B),
        ("10", "GND10", "power_in", B), ("11", "GND11", "power_in", B),
        ("20", "GND20", "power_in", B), ("D0", "GND_D0", "power_in", B),
        ("E0", "GND_E0", "power_in", B), ("F0", "GND_F0", "power_in", B)]
for _i, _pp in enumerate(_usados):
    _mod.append((PADS_ME54BS13[_pp], _pp, "bidirectional", L if _i < 17 else R))
add("U201", "MinewSemi ME54BS13", _mod, confirmed=True,
    note="nRF54LM20A, 16,5 x 12,0 x 2,4 mm, 80 pads (20 castelados + 60 LGA), "
         "64 GPIO. A ficha V1.0.0 e a V0.5.0 discordam do espelhamento: "
         "CONFERIR num modulo real que os GND D0, E0 e F0 ficam do lado do "
         "VCC (pino 19) antes de fabricar")

# CORRIGIDO em 2026-09-25, e era erro de placa.
#
# Este projeto declarava o pino 3 sem ligacao e o RESET no pino 6. A ficha
# oficial `TC2030-CTX_1.pdf` da Tag-Connect, tabela "Connections", diz o
# contrario: no footprint de 6 pinos e **3 = nRESET** e **6 = SWO/TDO**.
#
# De onde vinha a confusao: o arranjo 1 VCC, 2 SWDIO, 3 GND, 4 SWCLK, 5 GND,
# 6 SWO e a numeracao do CABECALHO CORTEX DE 10 VIAS, do lado da sonda, e
# nao a do footprint de 6 pinos da placa. Quem mistura as duas chega
# exatamente ao que estava escrito aqui.
#
# O que acontecia com a placa: o nRESET da sonda, que e dreno aberto, nao
# acionaria nada, e o nRESET do micro ficaria pendurado na entrada SWO da
# sonda. Nada queima - SWO e alvo para sonda, nao ha curto -, mas o
# depurador NUNCA conseguiria resetar o alvo: sem connect under reset, sem
# pin reset. Num nRF54LM20A que reinicia pelo task_wdt ou reconfigura os
# pinos de SWD, isso tira a saida de emergencia e sobra so o apagamento
# total por CTRL-AP.
#
# O pino 6 fica sem ligacao por enquanto. Ele e o SWO, e leva-lo a um pad de
# trace do modulo daria printf por ITM no bring-up - falta descobrir QUAL
# pad do ME54BS13 expoe o SWO.
add("J201", "Tag-Connect TC2030-NL", [
    (1, "VTref", "power_in", L), (2, "SWDIO", "bidirectional", R),
    (3, "RESET", "output", R), (4, "SWDCLK", "output", R),
    (5, "GND", "power_in", B), (6, "SWO", "no_connect", R),
], confirmed=True,
    note="so furos e pads. Pinagem da ficha TC2030-CTX_1.pdf da Tag-Connect: "
         "1 VCC, 2 SWDIO/TMS, 3 nRESET, 4 SWCLK/TCK, 5 GND, 6 SWO/TDO")

# The plug-in SWD connector the owner asked for on 2026-09-26, IN ADDITION to
# the Tag-Connect pads: the 10-pin, 2 x 5, 1,27 mm "Cortex Debug Connector"
# that the J-Link's 9-pin Cortex-M adapter (or any 10-way 1,27 mm IDC lead)
# mates with. Same nets as J201; only one of the two is used at a time.
# Pinout is ARM's, the one every Cortex-M board and SEGGER's adapter use:
# 1 VTref, 2 SWDIO/TMS, 3 GND, 4 SWDCLK/TCK, 5 GND, 6 SWO/TDO, 7 KEY (pin
# removed on the shrouded part), 8 TDI/NC, 9 GNDDetect, 10 nRESET. The part
# is still to be chosen (Samtec FTSH-105-01-L-DV-K or an equivalent shrouded
# 2 x 5 1,27 mm SMD header); the footprint is KiCad's generic one.
# SWDCLK and nRESET are `passive` here, not `output` as on J201: the two
# connectors share the nets, and two `output` pins on one net is an ERC
# error (pin_to_pin). J201 keeps the `output` that tells the ERC the net has
# a driver; this one is electrically the same thing in parallel.
add("J202", "SWD 2x5 1,27 mm", [
    (1, "VTref", "power_in", L), (2, "SWDIO", "bidirectional", R),
    (3, "GND1", "power_in", L), (4, "SWDCLK", "passive", R),
    (5, "GND2", "power_in", L), (6, "SWO", "no_connect", R),
    (7, "KEY", "no_connect", L), (8, "TDI", "no_connect", R),
    (9, "GNDDetect", "no_connect", L), (10, "nRESET", "passive", R),
], confirmed=True,
    note="conector Cortex Debug de 10 vias, 2 x 5, passo 1,27 mm, SMD, para o "
         "adaptador Cortex-M de 9 vias do J-Link; pinagem da ARM (Cortex Debug "
         "Connector): 1 VTref, 2 SWDIO, 3 GND, 4 SWDCLK, 5 GND, 6 SWO, 7 KEY, "
         "8 TDI, 9 GNDDetect, 10 nRESET. Peca a escolher, SEM carcaca (2,5 mm "
         "sobre a placa): o blindado de 4,83 mm nao cabe sob a tampa da caixa "
         "proposta, que deixa 3,6 mm da face da placa (make_caixa.py)")

# The sixteen test points of 06-conectores-e-pontos-de-teste.md. Eleven of
# the twelve on the power sheet were missing from the board entirely - only
# the three of the console sheet existed - and a rail you cannot put a probe
# on is a rail you cannot debug. TP111 and TP401 are NOT here, and both
# absences are the document's own: ST_STO is a node the AEM10900 datasheet
# does not have, and 5V0 belongs to a REG710NA-5 that is not fitted with the
# JDI panel.
TESTE = (
    ("TP101", "VBUS", "o que a fonte USB entrega, depois do TVS"),
    ("TP102", "VBUSOUT", "saida do limitador do nPM1300"),
    ("TP103", "VBAT", "lado SYS do medidor, 3,0 a 4,2 V"),
    ("TP104", "VSYS", "saida do power path; chega a 5,5 V com cabo"),
    ("TP105", "3V0", "BUCK2, o trilho do MCU"),
    ("TP106", "1V8", "BUCK1; maximo absoluto de 1,98 V no V_IO do receptor"),
    ("TP107", "SD3V0", "LDSW1, a flash; desligado tem de estar em 0 V"),
    ("TP108", "3V3BL", "LDSW2, a luz"),
    ("TP109", "VBCKP", "TPS7A02; continua de pe com o aparelho desligado"),
    # Era o VINT, o trilho interno do AEM10900. O ADP5091 nao tem trilho
    # interno em pino nenhum, e o no que mais importa medir no lugar dele e a
    # entrada do painel: e ela que diz se o MPPT esta no ponto certo, porque
    # em regime ela tem de ficar em 80,7 % da tensao em aberto.
    #
    # NAO ponha ponto de teste no MPPT nem no CBP: a pagina 24 da ficha pede
    # que nao haja plano de terra perto deles e avisa que residuo de fluxo
    # cria resistencia parasita que degrada o MPPT, porque o CBP tem de
    # segurar a tensao por 16 s entre duas amostras.
    ("TP110", "SRC", "entrada do painel; em regime fica em 80,7 % da tensao "
                     "em aberto, que e onde o MPPT trabalha"),
    ("TP112", "GND", "referencia do bloco de energia, com via propria ao plano"),
)

for n in [t[0] for t in TESTE] + ["TP201", "TP202", "TP203"]:
    add(n, "pad", [(1, "1", "passive", R)], confirmed=True, note="ponto de teste")
for n, v in (("C201", "100 nF"), ("C210", "4,7 uF")):
    passive(n, v)

# Por onde os seis modulos solares entram na placa.
#
# Eles NAO sao soldados na placa e nao podem ser: ficam na caixa, virados
# para o sol - dois na face inclinada e dois em cada chanfro - enquanto a
# placa fica dentro, atras do display. Sao tres orientacoes diferentes, e e
# isso que faz a colheita render com o guidao apontando para qualquer lado.
#
# Ate 2026-09-24 eram tres pares de pads de mola (J103, J104, J105), que 04
# registrava como nao dimensionados. Viraram UM conector, por tres motivos:
# a JLCPCB nao monta mola; uma bicicleta vibra, e um contato pressionado que
# abre e fecha na entrada de um conversor chaveado e um transitorio sujo; e
# o conector ocupa 8 mm da borda contra os 16 mm dos tres pares.
#
# A familia e ZH de 1,5 mm DE PROPOSITO. A bateria e um GH de 1,25 mm de 6
# vias, e o plugue de um nao entra no header do outro: 4,2 V numa entrada de
# 2,73 V queima o AEM10900. Alem disso o JST SH de 6 vias lateral, que seria
# a escolha obvia, saiu de linha - 3 pecas na JLCPCB.
#
# QUATRO vias, nao seis: os tres grupos dividem o mesmo terra, entao tres
# pinos de GND eram o mesmo no repetido. Alem de desperdicio, o corpo de 6
# vias tem 13,5 mm e fazia sombra no sensor de luz ambiente, que pede o dobro
# da propria altura livre em volta.
add("J103", "JST S4B-ZR-SM4A-TF", [
    (1, "PV_A", "passive", R), (2, "PV_B", "passive", R),
    (3, "PV_C", "passive", R), (4, "GND", "passive", B),
], confirmed=False,
    note="entrada dos seis modulos solares, em tres grupos de dois: frente, "
         "chanfro esquerdo, chanfro direito, mais o terra comum. ZH de "
         "1,5 mm, 4 vias, SMD lateral, com trava. CONFERIR o estoque na LCSC "
         "e a ordem das vias no chicote")

# Os tres 0 ohm que juntam os grupos ao SRC. Sem eles os seis modulos so dao
# um numero e nunca se sabe qual face esta rendendo; com eles, abre-se um e
# mede-se o grupo sozinho no sol. Mesmo raciocinio do JP301 da antena.
for _n in ("R113", "R114", "R115"):
    passive(_n, "0 R", "junta um grupo de modulos ao SRC; abrir para medir o "
                       "grupo sozinho na bancada")

# O grampo da entrada do colhedor. O conector certo impede o engano de plugar
# a bateria no painel; este impede o prejuizo quando o engano vier de outro
# lugar - fio invertido no crimp, painel trocado, fonte de bancada. O MPPT do
# ADP5091 vai ate 3,3 V e o arranjo em aberto da 2,07 V, entao um grampo com
# 3,3 V de trabalho fica acima do sinal util. Contra 4,2 V de uma celula ele
# NAO protege - grampo nao segura fonte sustentada; a familia do conector e
# que segura. Contra polaridade trocada protege, por ser unidirecional.
add("D105", "PESD3V3S1UB-N", [
    (1, "IO", "passive", L), (2, "GND", "passive", B),
], confirmed=False, lcsc="C920299",
    note="grampo do SRC: ESD unidirecional de 3,3 V em SOD-523, 1 uA de fuga "
         "no maximo a 3,3 V (bem menos nos 2,07 V de circuito aberto do "
         "painel), 160 pF, 100 W a 8/20 us. UNIDIRECIONAL de proposito: o "
         "diodo direto grampeia a entrada em -0,7 V se o chicote vier com a "
         "polaridade trocada. Nao protege de fonte errada sustentada (uma "
         "celula de 4,2 V no J103): quem impede isso e a familia do conector. "
         "Escolhida em 2026-09-25; o maximo absoluto do VIN do ADP5091 nao "
         "pode ser conferido - a ficha dele nao esta no repositorio")

# ---- corte termico do caminho solar. Decidido pelo dono em 2026-09-25, a
# opcao (b) das quatro registradas acima: o divisor do NTC e o divisor de
# referencia sao alimentados pelo VIN do painel (SRC), nao pela bateria.
# No escuro VIN e zero e o consumo e zero; ao sol os ~180 uA saem do painel,
# que da ~88 mA. O comparador compara as duas razoes, entao o limiar nao
# depende da tensao do painel. A saida push-pull sobe ao VSYS quando esta
# quente e, por um Schottky, poe o DIS_SW em alto - o OU com o divisor do
# USB, que continua funcionando porque com a saida em baixo o diodo fica
# reverso. O ADP5091 nao tem entrada de temperatura; carregar Li-ion acima
# de 45 graus e questao de seguranca.
#
#   SRC ---[RT101 10k NTC]---+---[R106 4,87k]--- GND     IN+ = VIN/2 a 45 C
#   SRC ---[R124 100k]-------+---[R125 100k]---- GND     IN- = VIN/2
#   U105 OUT ---|>|--- DIS_SW                             D106
add("U105", "TLV7031DCKR", [
    (1, "IN+", "input", L), (2, "GND", "power_in", B), (3, "IN-", "input", L),
    (4, "OUT", "output", R), (5, "V+", "power_in", T),
], confirmed=False, lcsc="C2869832",
    note="comparador de 315 nA com saida push-pull, SC70-5; alimentado pelo "
         "VSYS. A PINAGEM E A DO SC70 PADRAO DE COMPARADOR (IN+, GND, IN-, "
         "OUT, V+) e tem de ser CONFERIDA na ficha SNOSD54 antes de fabricar; "
         "o comentario antigo desta lista o dava como dreno aberto, e e o "
         "TLV7041 que e dreno aberto")
passive("R124", "100 k", "referencia do corte termico: metade do VIN do painel")
passive("R125", "100 k", "referencia do corte termico, ao GND")
add("D106", "BAT54WS-7-F", [
    (1, "K", "passive", L), (2, "A", "passive", R),
], confirmed=False, lcsc="C124205",
    note="Schottky do OU no DIS_SW: anodo na saida do comparador, catodo no "
         "DIS_SW. SOD-323; catodo no terminal 1 CONFERIR pela marca do desenho")

# A tecla central. Decidido pelo dono em 2026-09-26: o P1.27 do MCU le o
# no da tecla por um Schottky, anodo no MCU (pull-up interno) e catodo no
# no. O no e o SHPHLD do nPM1300, que tem pull-up interno de 50 k para VBAT
# OU VBUS, o que for maior (ficha, p. 120): com cabo ele vai a 5,5 V, acima
# do maximo absoluto do pino do MCU (VDD + 0,3 V); e em ship mode, com o
# 3V0 em zero, o diodo de protecao do P1.27 grampeava o SHPHLD em 0,6 V e o
# PMIC lia tecla pressionada - o aparelho nao ficava desligado.
add("D107", "BAT54WS-7-F", [
    (1, "K", "passive", L), (2, "A", "passive", R),
], confirmed=False, lcsc="C124205",
    note="Schottky que isola o P1.27 do no da tecla central; catodo no no, "
         "anodo no MCU. SOD-323; catodo no terminal 1 CONFERIR pela marca")

# ---- desacoplamento que as fichas pedem e faltava (revisao de 2026-09-26)
passive("C122", "100 nF", "bypass do BATT do MAX17262, junto do CI (ficha, p. 12)")
passive("C123", "100 nF", "desacoplamento do VDD do BMI270, junto do pino 8 (ficha, p. 136)")
passive("C124", "100 nF", "desacoplamento do VDDIO do BMI270, junto do pino 5 (ficha, p. 136)")
passive("C125", "100 nF", "desacoplamento do VDD/VDDIO do BMP585, junto do CI")
passive("C126", "100 nF", "desacoplamento do VDD do OPT3001, junto do CI")
passive("C129", "100 nF", "desacoplamento do VDDIO do nPM1300: o C13 da referencia (tabela 40)")

# ---- luz do display: um resistor por catodo. Os quatro LEDs em paralelo
# num resistor so repartiam os 16 mA pela dispersao de V_F; com um por
# catodo, cada um leva (3,3 - 2,68 - 0,05) / 4 mA = 143 ohm -> 150 ohm, 4 mA.
for _n in ("R406", "R407", "R408", "R409"):
    passive(_n, "150 R", "R_BL, um por catodo da luz: 4 mA cada, 16 mA no total")

# ---------------------------------------------------------------- folha 3
# MAX-F10S data sheet UBXDOC-963802114-12732 R03, table 10, page 9.
add("U301", "u-blox MAX-F10S", [
    (1, "GND", "power_in", B), (2, "TXD", "output", R), (3, "RXD", "input", L),
    (4, "TIMEPULSE", "output", R), (5, "EXTINT", "input", L),
    (6, "V_BCKP", "power_in", T), (7, "V_IO", "power_in", T),
    (8, "VCC", "power_in", T), (9, "RESET_N", "input", L),
    (10, "GND2", "power_in", B), (11, "RF_IN", "input", L),
    (12, "GND3", "power_in", B), (13, "LNA_EN", "output", R),
    (14, "VCC_RF", "power_out", R), (15, "VIO_SEL", "input", L),
    (16, "SDA", "bidirectional", L), (17, "SCL", "input", L),
    (18, "SAFEBOOT_N", "input", L),
], confirmed=True,
    note="receptor L1+L5 no 3V0, VCC e V_IO juntos e VIO_SEL aberto (opcao 1 da "
         "tabela 35 do manual de integracao): V_IO de 2,7 a 3,6 V, e as quatro "
         "linhas digitais vao direto ao MCU, que tambem e de 3,0 V")

# O tradutor de nivel TXU0204 (U302) saiu em 2026-09-26, quando o receptor
# passou a 3,0 V: MCU e receptor no mesmo trilho nao precisam de tradutor.

# A antena de chip mudou de peca em 2026-09-24, e a nova resolve de vez o
# problema que a antiga criava.
#
# A TE L000670-01 esta com estoque ZERO na LCSC, e exigia area sem cobre de
# 40,5 x 14,5 mm EM TODAS AS CAMADAS - mais larga que esta placa inteira, que
# tem 34 mm. Alem disso a curva de eficiencia da ficha dela desabava com
# plano de terra curto: 62 % de eficiencia em L5 com 90 mm de terra, 43 % com
# 70 e 29 % com 50, e L5 e a razao inteira de ter escolhido o MAX-F10S.
#
# A Unictron H2UJ4U1H2Q0100 pede 15,00 x 9,35 mm na face de cima e 15,00 x
# 9,88 na de baixo, medidos da BORDA DA PLACA, e o recorte nao e simetrico em
# relacao a ela: a antena ocupa 5,0 mm no meio, com 2,45 mm de recorte de um
# lado e 7,55 do outro. Entre o recorte de cima e a borda fica uma faixa de
# terra de 0,65 mm, interrompida no meio, onde os pads de terra se ligam.
#
# O que NAO melhorou: a ficha da 70 % de eficiencia tipica em L1 e em L5, mas
# medidos numa placa de avaliacao de 80 x 40 mm. Esta placa tem 34 mm de
# largura, menos que os 40 do plano de referencia, e antena de chip depende
# forte do plano de terra. A ficha NAO traz curva de eficiencia contra
# tamanho de terra, entao 70 % e teto otimista, nao previsao.
#
# Os pinos 1 e 2 sao terra E sintonia: vao ao plano por dois capacitores, e
# nao direto. O 3 e o sinal, no centro geometrico da antena.
add("E301", "Unictron H2UJ4U1H2Q0100", [
    (1, "GND_T1", "passive", B), (2, "GND_T2", "passive", B),
    (3, "FEED", "passive", R),
], confirmed=True, lcsc="C6569550",
    note="antena de chip ceramica L1+L5, 5,0 x 3,0 x 0,5 mm, na borda da "
         "placa. Substitui a TE L000670-01 (estoque zero e recorte de "
         "40,5 x 14,5). Uma das duas opcoes, escolhida pelo JP301")

# Os dois capacitores de sintonia dos pinos de terra da antena: posicoes [8]
# e [9] do circuito da pagina 11 da ficha. Os valores sao os que a Unictron
# recomenda, e a propria ficha avisa que eles centram a antena na placa de
# avaliacao de 80 x 40 mm e VAO PRECISAR DE MUDANCA numa placa diferente.
passive("C119", "10 nF", "CBP do ADP5091: X7R ou C0G de baixa fuga, e ele "
                         "segura a tensao por 16 s entre amostras da Voc")
passive("C120", "100 nF", "desacoplamento de alta frequencia do SYS, em "
                          "paralelo com o C116; a ficha pede os DOIS")
passive("C121", "4,7 uF", "REG_OUT do regulador desabilitado; footprint "
                          "mantido, pode ficar NAO MONTADO")
passive("C305", "2,7 pF", "sintonia do pino 1 da antena ao terra; valor de "
                          "partida da ficha, a ajustar na bancada")
passive("C306", "6,8 pF", "sintonia do pino 2 da antena ao terra; valor de "
                          "partida da ficha, a ajustar na bancada")
# The board carries BOTH ways of feeding the receiver, and a 0 ohm chooses.
# The chip soldered on the edge is the shorter path and has no connector in
# it; the u.FL lets an external element be tried without touching the board.
# Which one is better is a bench question - the efficiency of the chip falls
# with the ground plane and this board is 34 mm wide against the 90 x 41 the
# datasheet measured on - so both are laid out and only one is fitted.
#
# THREE pads and one 0 ohm, not two jumpers: the branch that is not chosen
# has to be an open pad, not a stub. A stub on a 50 ohm line at 1,6 GHz is
# a quarter wave at 23 mm and a short at the receiver long before that.
add("JP301", "0 R", [
    (1, "COMUM", "passive", L), (2, "UFL", "passive", T),
    (3, "CHIP", "passive", R),
], confirmed=True,
    note="escolhe a antena: 0 ohm entre COMUM e UFL, ou entre COMUM e CHIP. "
         "Monta-se UM so")
# The GNSS antenna arrives on a u.FL, not on a spring contact. The line it
# feeds is the L1 + L5 path of the MAX-F10S, and 4.4 of the integration
# manual asks for 50 ohm on ALL of it: a pair of gold pads that a leaf
# spring presses on has no defined impedance at 1,2 and 1,6 GHz, no defined
# return path and a contact resistance that changes with how the case was
# closed. A u.FL is a 50 ohm coaxial transition, it is what every GNSS
# module reference design uses for an external element, and it lets the
# antenna be a cable assembly instead of a mechanical fit.
#
# It costs the board a 2,6 x 2,6 mm part and it costs the case a cable
# instead of a contact - which is a mechanical decision, and it is written
# here because nothing else records it.
add("J302", "Hirose U.FL-R-SMT-1", [
    (1, "FEED", "passive", R), (2, "GND", "passive", B),
], confirmed=False, lcsc="C88374",
    note="conector coaxial u.FL da antena GNSS L1+L5. Substitui o contato de "
         "mola que 04:271 tinha decidido: mola nao tem impedancia definida, "
         "e a 4.4 do manual do MAX-F10S pede 50 ohm em TODO o caminho de RF. "
         "CONFERIR o cabo e o conector da outra ponta antes de fabricar")
# DEFEITO ABERTO, achado em 2026-09-24. As duas fichas do receptor - MAX-F10S
# UBXDOC-963802114-12732 R03 e MAX-M10S UBX-20035208 R08 - proibem mais de
# 0,2 ohm em serie na linha de alimentacao, e pedem 1,8 V +-2 %, que sao
# 36 mV. O BLM15PX601SN1D tinha 230 mOhm de DCR: no pico de partida de 100 mA
# isso da 23 mV, dois tercos da tolerancia inteira, so no ferrite.
#
# FECHADO em 2026-09-25: BLM18KG601SN1D (LCSC C85833), 0603, 600 ohm a
# 100 MHz, 1,3 A, 150 mOhm - 15 mV no pico de 100 mA e 3,9 mV nos 26 mA de
# regime. Em 0402 nao existe 600 ohm com DCR abaixo de 200 mOhm no catalogo,
# que e por que o encapsulamento subiu; 371 mil pecas em estoque na consulta.
passive("FB301", "600 R @100 MHz", "ferrite do 3V0 junto do receptor: Murata "
                                   "BLM18KG601SN1D, 0603, 1,3 A, DCR 150 mOhm "
                                   "- dentro dos 0,2 ohm do manual (4.1.1). "
                                   "Fechado em 2026-09-25; era o BLM15PX601SN1D "
                                   "de 0402 e 230 mOhm",
        lcsc="C85833")
passive("C301", "1,5 pF", "shunt [1] da rede de casamento. O valor depende "
                          "de QUAL antena for montada: 1,5 pF e o que a "
                          "Unictron recomenda para a antena de chip; com "
                          "o u.FL e uma antena externa de 50 ohm, nao se "
                          "monta")
passive("C302", "NP", "shunt [3] da rede de casamento: a Unictron manda "
                      "NAO MONTAR. O pad fica para a bancada")
# O elemento em serie MUDA DE TIPO conforme a antena. A Unictron pede um
# CAPACITOR de 3,6 pF em [2]; o caminho do u.FL com antena externa de
# 50 ohm pede um 0 ohm ou um indutor. O footprint e 0402 nos dois casos,
# entao a placa nao muda - so o que se solda nela.
passive("L301", "3,6 pF", "serie [2] da rede de casamento, com a antena de "
                          "chip. Com o u.FL, 0 ohm. A serie de indutores "
                          "de RF 2,2 a 5,6 nH esta toda na LCSC para "
                          "ajuste de bancada", lcsc="C98063")
passive("C303", "10 uF")
passive("C304", "100 nF")

# ---------------------------------------------------------------- folha 4
# The 10-way display FPC order is the one 03-netlist.md uses, contact by
# contact, and it is the same for the JDI and for the Sharp.
# O conector do display passou do FH28 para o FH12 em 2026-09-24, e a altura
# foi a razao: a sombra sob o display tem 2,6 mm de teto, o FH28 tem 2,55 de
# altura fechado (folga de 0,05, que na pratica nao passa) e o FH12 tem
# 2,00 +-0,2 (folga de 0,40 no pior caso da tolerancia). De quebra o FH12 e
# 0,8 mm mais estreito, o land pattern economiza 2,4 mm de profundidade, tem
# mais estoque na LCSC (8.351 contra 2.487) e e o footprint que o KiCad ja
# traz - com modelo STEP, que o FH28 nao tem em lugar nenhum.
#
# Os dois sao BOTTOM CONTACT: a cauda do display entra com as trilhas
# viradas para a placa. E os dois sao flip-lock rotativo - o atuador gira
# para cima, entao o FPC tem de ser travado ANTES de fechar a caixa.
add("J401", "Hirose FH12-10S-0.5SH(55)", [
    (1, "SCLK", "input", R), (2, "SI", "input", R), (3, "SCS", "input", R),
    (4, "EXTCOMIN", "input", R), (5, "DISP", "input", R), (6, "VDDA", "power_in", R),
    (7, "VDD", "power_in", R), (8, "EXTMODE", "input", R), (9, "VSS", "power_in", R),
    (10, "VSSA", "power_in", R),
], confirmed=True, lcsc="C506791", note="FPC de sinal do painel, 10 vias; ordem de 03-netlist.md")

# LPM027M128C specification ver.02: the signal FPC in 1.4.1 (page 4) and the
# backlight FPC in 1.4.2 (page 5). The light is four white LEDs in parallel
# inside the panel: pin 5 is the common anode and pins 1 to 4 are one cathode
# each. No via is spare, which is what this project assumed for a whole day.
add("DS401", "JDI LPM027M128C", [
    (1, "SCLK", "input", L), (2, "SI", "input", L), (3, "SCS", "input", L),
    (4, "EXTCOMIN", "input", L), (5, "DISP", "input", L), (6, "VDDA", "power_in", L),
    (7, "VDD", "power_in", L), (8, "EXTMODE", "input", L), (9, "VSS", "power_in", B),
    (10, "VSSA", "power_in", B),
    ("BL1", "LUZ_K1", "passive", R), ("BL2", "LUZ_K2", "passive", R),
    ("BL3", "LUZ_K3", "passive", R), ("BL4", "LUZ_K4", "passive", R),
    ("BL5", "LUZ_ANODO", "passive", R),
], confirmed=True,
    note="painel MIP 2,7 pol com luz de 4 LED em paralelo; V_F 2,68 V tipico a "
         "4 mA por LED (16 mA no total), maximo absoluto de 30 mA no conjunto")

# The same outline drawing names the connector: "Backlight FPC 503480-0500,
# 5pin / molex". The 4-way 5034800440 of the Sharp plan B is the same family.
# O Molex 503480-0500 que a JDI nomeia no desenho de contorno do display nao
# esta na LCSC, e a placa e montada na JLCPCB. Este e o equivalente com
# estoque: 45.619 pecas, contato inferior como o J401 do sinal, e corpo bem
# menor - 4,27 x 2,90 x 1,00 contra 7,93 x 4,40 x 1,20.
add("J402", "HCTL HC-FPC-05-10-5RLTAG", [
    (1, "1", "passive", L), (2, "2", "passive", L), (3, "3", "passive", L),
    (4, "4", "passive", L), (5, "5", "passive", L),
], confirmed=True, lcsc="C5213728", note="conector da luz do painel, 5 vias, passo 0,5 mm, "
                        "recomendado pela propria JDI no desenho de contorno")

add("Q401", "DMG1012T-7", [
    (1, "G", "input", L), (2, "S", "passive", B), (3, "D", "passive", T),
], confirmed=False, lcsc="C20512",
    note="chave de canal N da luz. A Diodes NAO publica numero de pino: o "
         "diagrama so mostra a posicao, e a numeracao vem do padrao SOT-523")

passive("R402", "100 k", "pull-down da porta do Q401")
passive("R403", "100 k", "pull-down do DISP_PWR_EN")
passive("R404", "100 k", "pull-down do DISP_ON")
passive("R405", "100 k", "pull-down do DISP_CS")
passive("JP401", "0 R", "VDD do painel: 0 R fixo na posicao do 3V0")
passive("C404", "100 nF")

# ---------------------------------------------------------------- folha 5
add("U501", "MX25R6435F", [
    (1, "CS_N", "input", L), (2, "SO_IO1", "bidirectional", R),
    (3, "WP_N_IO2", "bidirectional", R), (4, "GND", "power_in", B),
    (5, "SI_IO0", "bidirectional", L), (6, "SCLK", "input", L),
    (7, "HOLD_N_IO3", "bidirectional", R), (8, "VCC", "power_in", T),
], confirmed=True, lcsc="C2802844", note="flash NOR SPI; numeros 1, 2, 5 e 6 vem de 03-netlist.md")

# BMP585: BST-BMP585-DS003-02 rev 1.2, section 6.1, table 26, page 45.
# LGA of 8 pins, 3.25 x 3.25 mm - not the 2.0 x 2.0 this project assumed.
add("U502", "Bosch BMP585", [
    (1, "SCX", "input", L), (2, "SDX", "bidirectional", L),
    (3, "SDO", "bidirectional", L), (4, "VDDIO", "power_in", T),
    (5, "INT", "output", R), (6, "VSSIO", "power_in", B),
    (7, "CSB", "input", L), (8, "VDD", "power_in", T),
], confirmed=True, lcsc="C18184976",
    note="barometro; 0x46 com SDO em 0 e 0x47 com SDO em 1, e a Bosch proibe "
         "SDO flutuando. CSB ao VDDIO para I2C. O pino 9 e so marcacao a laser")

# BMI270: BST-BMI270-DS000-08 rev 1.6, table 22, page 135.
add("U503", "Bosch BMI270", [
    (1, "SDO", "bidirectional", L), (2, "ASDX", "bidirectional", L),
    (3, "ASCX", "bidirectional", L), (4, "INT1", "bidirectional", R),
    (5, "VDDIO", "power_in", T), (6, "GNDIO", "power_in", B),
    (7, "GND", "power_in", B), (8, "VDD", "power_in", T),
    (9, "INT2", "bidirectional", R), (10, "OCSB", "input", R),
    (11, "OSDO", "output", R), (12, "CSB", "input", L),
    (13, "SCX", "input", L), (14, "SDX", "bidirectional", L),
], confirmed=True, lcsc="C2836813",
    note="IMU, 0x68 com o SDO no GND; CSB ao VDDIO para I2C; ASDX e ASCX ao "
         "VDDIO ou abertos, NUNCA ao GND")

# MMC5603NJ Rev. B: WLP of four balls, 0,82 x 0,82 x 0,40 mm plus 0,14 of
# ball, so 0,54 of total height. There is no LGA version and no INT or
# address pin on this package.
#
# It replaces the MMC5633NJL, which does not exist at LCSC. Same family, same
# 7-bit address 0x30, and the same 0x10 in register 0x39 - so the Zephyr
# driver and the devicetree node do not change. What changes is the land
# pattern (0,82 instead of 0,85, pad o0,23 instead of 0,20) and the
# decoupling, which this data sheet puts at a MINIMUM of 2,2 uF.
add("U504", "Memsic MMC5603NJ", [
    ("A1", "VSA", "power_in", B), ("A2", "SCL", "input", L),
    ("B1", "VDD", "power_in", T), ("B2", "SDA", "bidirectional", L),
], confirmed=True, lcsc="C404328",
    note="magnetometro, 0x30; VSA e o terra; NAO varrer o barramento "
         "(0x7E poe a peca em I3C ate faltar energia)")

# OPT3001: SBOS681C, section 5, page 3. One package only, DNP, USON-6.
add("U505", "TI OPT3001DNPR", [
    (1, "VDD", "power_in", T), (2, "ADDR", "input", L), (3, "GND", "power_in", B),
    (4, "SCL", "input", L), (5, "INT", "open_collector", R),
    (6, "SDA", "bidirectional", L),
], confirmed=True, lcsc="C90462", note="luz ambiente, 0x44 com ADDR no GND")

passive("R501", "100 k", "pull-up do NOR_CS ao SD3V0")
passive("R502", "47 k", "pull-up do WP ao SD3V0")
passive("R503", "47 k", "pull-up do HOLD ao SD3V0")
passive("R504", "4,7 k", "pull-up do SENS_SDA")
passive("R505", "4,7 k", "pull-up do SENS_SCL")
passive("R506", "33 R", "serie do NOR_SCK, junto do MCU")
passive("R507", "33 R", "serie do NOR_MOSI, junto do MCU")
passive("R508", "33 R", "serie do NOR_MISO, junto da flash")
passive("C501", "22 uF")
passive("C502", "4,7 uF", "VDD do MMC5603NJ; a ficha Rev. B, pagina 5, "
                          "pede MINIMO de 2,2 uF junto do pino - nao sao "
                          "os 100 nF de costume")
passive("C503", "100 nF")

# ---------------------------------------------------------------- folha 6
for n in ("SW601", "SW602", "SW603"):
    # DOIS terminais, nao quatro. A Omron B3S-1002P que estava aqui tinha
    # quatro pinos em dois pares ligados por dentro; esta tem dois e pronto.
    # O esquematico ja tratava a tecla como duas pontas, entao so o land
    # pattern muda.
    #
    # O part number se decodifica no desenho: TS-1088 R = sem pino de
    # posicionamento, 020 = 2,0 mm de altura, 26 = 260 gf.
    add(n, "XunPu TS-1088R-02026", [
        (1, "1", "passive", L), (2, "2", "passive", R),
    ], confirmed=True, lcsc="C455280",
        note="tecla tatil SPST-NO, 3,90 x 3,00 x 2,00 mm, 260 gf, curso de "
             "0,2 mm. O embolo de o1,80 sobe so 0,50 mm acima da tampa de "
             "aco, contra os 0,7 da Omron que ela substitui: a mecanica do "
             "embolo da caixa MUDA")

# Murata PKLCS1212E4001-R1, especificacao JGB40-1584B. Transdutor PASSIVO,
# sem oscilador: quem gera a onda e o firmware, em contrafase pelos dois
# transistores. A nota 12-4 da especificacao pede resistor de serie de 1 k a
# 2 k ou diodo em paralelo, e PROIBE DC - os R607 e R608 de hoje precisam de
# conferencia contra esse numero.
#
# O furo de som e uma FENDA LATERAL de 1,9 x 0,9 mm, com a aresta de baixo a
# 0,30 mm da placa, e a face inferior tem um canal saindo pela parede oposta.
# A caixa precisa de duto lateral, nao de furo na tampa.
add("LS601", "Murata PKLCS1212E4001-R1",
    [(1, "A", "passive", L), (2, "B", "passive", R)],
    confirmed=True, lcsc="C113159",
    note="buzzer piezo passivo, 12 x 12 x 3,0 mm, 84 dB a 4 kHz, acionado em "
         "contrafase. Sem polaridade. Furo de som LATERAL, rente a placa")

add("D601", "TUOZHAN S4-3528RGBTA-A", [
    ("A", "ANODO", "passive", T), ("KR", "K_R", "passive", B),
    ("KG", "K_G", "passive", B), ("KB", "K_B", "passive", B),
], confirmed=True, lcsc="C2827321",
    note="LED RGB de ANODO COMUM, 3,5 x 2,8 x 1,9 mm; o resistor fica do "
         "lado do catodo. Pinos da ficha S35210052: 1 azul, 2 anodo, "
         "3 verde, 4 vermelho, com o canto chanfrado junto ao vermelho. "
         "MUITO mais brilhante que o APTF1616 que substitui (460 a 1000 mcd "
         "no vermelho contra 15): RECALCULAR R601, R602 e R603. MSL4"),

for n in ("Q601", "Q602", "Q603"):
    add(n, "DMG1012T-7", [
        (1, "G", "input", L), (2, "S", "passive", B), (3, "D", "passive", T),
    ], confirmed=False,
        note="chave de canal N de uma cor do LED; a Diodes nao publica numero "
             "de pino, a numeracao vem do padrao SOT-523")

passive("R601", "1 k", "R_LEDR, do lado do catodo")
passive("R602", "1 k", "R_LEDG, do lado do catodo")
passive("R603", "1 k", "R_LEDB, do lado do catodo")
passive("R604", "100 R", "serie da tecla esquerda")
passive("R605", "100 R", "serie da tecla central")
passive("R606", "100 R", "serie da tecla direita")
passive("C601", "1 nF", "da tecla esquerda ao GND")
passive("C602", "1 nF", "da tecla central ao GND")
passive("C603", "1 nF", "da tecla direita ao GND")
passive("R607", "1 k", "serie do BUZ_A")
passive("R608", "1 k", "serie do BUZ_B")
passive("R609", "100 k", "pull-down da porta do Q601")
passive("R610", "100 k", "pull-down da porta do Q602")
passive("R611", "100 k", "pull-down da porta do Q603")

for n in ("JP102", "JP103", "JP104", "JP105", "JP106"):
    passive(n, "0 R", "jumper de corrente do bloco")


def by_sheet() -> dict[str, list[str]]:
    """Which parts belong to which sheet of 01-esquematico.md."""
    out: dict[str, list[str]] = {"1 Energia": [], "2 MCU": [], "3 GNSS": [],
                                 "4 Display": [], "5 Memoria e sensores": [],
                                 "6 Interface": []}
    for ref in PARTS:
        digits = "".join(c for c in ref if c.isdigit())
        n = int(digits[0]) if digits else 1
        key = {1: "1 Energia", 2: "2 MCU", 3: "3 GNSS", 4: "4 Display",
               5: "5 Memoria e sensores", 6: "6 Interface"}.get(n, "1 Energia")
        out[key].append(ref)
    for k in out:
        out[k].sort()
    return out


if __name__ == "__main__":
    print(f"{len(PARTS)} posicoes")
    for k, v in by_sheet().items():
        print(f"  folha {k}: {len(v)}")
    print(f"pinagem nao confirmada em {len(UNCONFIRMED)}: {', '.join(sorted(UNCONFIRMED))}")
