Guiimartinho/gnss-bike-computer/hardware_gnssbike/cad/route.py

#!/usr/bin/env python3
"""Route the board: tracks on the two outer layers, vias, and ground by plane.

How a four layer board of this kind is routed, and what this does:

  GND      is not routed as tracks. In1.Cu is a solid ground pour and F.Cu
           and B.Cu carry one too, so a ground pad is connected by the pour
           of its own face; on top of that each one gets a short stub to a
           via down into the inner plane, which is the short return path.
           The edge is stitched with a ground via about every 3 mm, because
           two planes are one plane only if they are tied together often
           enough - a tenth of a wavelength at 2.44 GHz is about 6 mm.
  signals  are maze routed on F.Cu, In2.Cu and B.Cu, with a via to change
           layer. The cost of a via is high enough that a run only changes
           layer when it has to.
  power    uses the wider track of the Alimentacao net class.
  RF       goes FIRST, on the front layer only, at the calculated 50 ohm
           width for this stack-up (0.196 mm), with ground vias down both
           sides. First because its path is the one that is not negotiable
           and it has to leave the receiver's pin before anything else takes
           the room; front only because a via in the middle of an RF run is
           a stub, which 7.2 of the module datasheet forbids by name. The
           width still assumes the dielectric constant of ordinary FR-4 -
           the fabricator's own stack-up is an open item in
           04-pcb-e-caixa.md, and the dry-run prints the assumption.

Order matters: the switching nodes of the two bucks and of the harvester go
first and stay short, because their loop area is what radiates; then the USB
pair, together; then everything else, shortest first.

TWO GRIDS, and why. The first version kept one grid, inflated by half a
track plus the clearance, and used it for tracks and for vias alike. The
board it produced failed 974 design rules. So: one grid for what a track may
occupy, one for where the CENTRE of a via may land. Along the way, each of
these was a defect that the DRC found and the grid had not:

  a via is 0.45 mm wide where a track is 0.15, with a 0.25 mm hole that the
  grid did not model, so every via sat about 0.15 mm too close;
  pads were inflated as circles of half their longest side, which fits a
  round pad and leaves the corners of a square one bare;
  the ground stub left the pad on whatever bearing was free AT THE VIA,
  crossing whatever lay in between without asking;
  the clearance of a pad was remembered with "first come, first served", so
  a cell inside TWO pads' clearance kept only one of them and a track of the
  first ran 0.025 mm from the second;
  the USB class asks for 0.2 mm and was treated as the default 0.127;
  a 0.4 mm power track ran onto a 0.2 mm pad and stuck out on both sides;
  a via was checked at the grid cell and then drilled at the raw coordinate,
  up to half a step - 0.075 mm - away from what had been checked;
  and writing the tracks did not remove the previous run's, so routing twice
  left two sets of copper on top of each other.

What guards against the next one is conferir(): it measures the result
against itself, shape by shape, before the board is written.

Run:   python hardware_gnssbike/cad/route.py
Check: python hardware_gnssbike/cad/check_pcb.py
"""

from __future__ import annotations

import heapq
import math
import pathlib
import sys

HERE = pathlib.Path(__file__).resolve().parent
sys.path.insert(0, str(HERE))

import footprints as FPS  # noqa: E402,F401
import fp_load  # noqa: E402
import make_dxf as M  # noqa: E402
import make_pcb as MP  # noqa: E402

PASSO = 0.15                # routing grid, mm. 0.3 does not fit between
                            # the balls of the module's LGA: the free band
                            # between two columns is 0.45 mm wide
LARGURA = 0.15              # default track width
LARGURA_ALIM = 0.4          # power track width
LARGURA_USB = 0.2
VIA_D, VIA_FURO = 0.45, 0.25

# The grid is marked for the NARROWEST track and the smallest clearance, and
# a wider or better spaced net asks for the extra radius when it looks. The
# first version inflated everything by the widest track and the widest
# clearance, and then nothing could escape a 0.5 mm pitch LGA: every net
# failed, every failure retried over the whole board, and a pass took
# forever. Two nets need centre to centre wA/2 + folga + wB/2, and marking
# wA/2 + FOLGA + LARGURA/2 while B asks for (wB - LARGURA)/2 gives exactly
# that.
# The classes of gnssbike.kicad_pro, read and not guessed: Default 0.127,
# Alimentacao 0.127 (it differs by via size, not by clearance) and USB 0.2.
# Treating USB as 0.127 is what put a ground track 0.075 mm from USB_DP.
FOLGA = 0.14                # 0.127 of the class, plus the grid
FOLGA_FURO = 0.21           # 0.2 do min_hole_clearance, mais a grade
FOLGA_USB = 0.21            # 0.2 of the USB class, plus the grid
# A via next to a pad has to leave more than the electrical clearance: the
# two solder mask openings grow about 0.05 mm each and the web of mask left
# between them has to be wide enough to survive, or the DRC reports a mask
# bridge - 41 of them on the last board. 0.35 mm of copper leaves about
# 0.25 mm of mask, which is the usual minimum.
FOLGA_MASCARA = 0.35
BORDA_COBRE = 0.3           # copper to board edge
# O que um ponto da grade precisa guardar ate a borda: o isolamento de
# cobre MAIS metade da via, porque o roteador poe uma via em qualquer
# ponto onde troca de camada.
MARGEM_BORDA = 0.3 + 0.45 / 2
# Three routing layers, not two. In1.Cu is the ground plane and stays one:
# it is what the return current follows and what the GNSS antenna radiates
# against, and cutting it up to gain routing space would cost more than it
# gains. In2.Cu was EMPTY - a whole copper layer paid for and unused - while
# 77 connections had nowhere to go on the other two. A signal on In2.Cu has
# the ground plane above it and the back pour below, which is a better
# reference than either outer layer gets.
CAMADAS = ("F.Cu", "In2.Cu", "B.Cu")
NC = len(CAMADAS)
I_BCU = NC - 1
CUSTO_VIA = 16.0            # in grid steps, about 2,4 mm
CUSTO_CURVA = 0.7             # virar 90 graus
CUSTO_CURVA_45 = 0.2          # virar 45: meia virada, meio custo
# A maze search that cannot get through explores everything it is allowed to
# before saying so, and on a 367 x 647 grid over two layers that is nearly a
# million cells for one net that was never going to route. The budget turns a
# hopeless search into two seconds instead of half a minute; what it costs is
# that a genuinely tortuous path may be given up on, and that shows in the
# report as a net left unrouted rather than as a wrong board.
ORCAMENTO = 300000   # era 90000: o tabuleiro tem ~400 mil celulas

BLOQUEADO = "\x00"          # a net name no net can have: blocked for everyone

# The RF nets. They are routed LAST and at the calculated 50 ohm width, on
# the front layer only, with the ground pour beside them and ground vias
# along both sides: a via in the middle of an RF run is a stub, and a stub is
# what section 7.2 of the module datasheet forbids by name.
# RF_UFL and RF_CHIP are the two branches after the choice jumper: both are
# 50 ohm line and both are routed at the RF width on the front layer, even
# though only one is ever fitted. The unfitted one ends at an open pad.
NAO_ROTEAR = {"RF_IN", "RF_ANT", "RF_UFL", "RF_CHIP"}
# O par do USB tambem fica na frente: os 0,207 mm de 90 ohm foram
# calculados para microstrip em F.Cu sobre o plano de terra a 0,10 mm. Em
# In2.Cu a mesma trilha tem o plano a 0,46 mm de um lado e o despejo de B.Cu
# a 0,10 do outro, e nao e 90 ohm de nada. As amarracoes dos contatos
# repetidos ficam em In2.Cu de proposito, mas sao emendas de 1,7 mm entre
# ilhas do mesmo no, nao a linha.
SO_FRENTE = NAO_ROTEAR | {"USB_DP", "USB_DM"}
# The differential pair. They are routed one after the other, and the second
# one is drawn towards the first, so they run together instead of taking two
# unrelated paths across the board.
PAR = ("USB_DP", "USB_DM")
# Nets that go first and have to stay short: the switching loops.
PRIMEIRO = ["BUCK1_SW", "BUCK2_SW", "SW_DCDC", "SW_DCDC_L", "USB_DP", "USB_DM"]


ALIMENTACAO = ("GND", "VSYS", "VBAT", "VBAT_SYS", "VBAT_CELULA", "VBUS",
               "VBUSOUT", "3V0", "1V8", "SD3V0", "3V3BL", "VBCKP", "VINT")


def e_alimentacao(rede: str) -> bool:
    return rede in ALIMENTACAO or rede.startswith(("3V0_", "1V8_", "SD3V0_"))



# --- impedancia ------------------------------------------------------------
# The RF line has to be 50 ohm and the USB pair 90 ohm differential, and both
# datasheets say so: ME54BS13 7.2 ("strict 50 ohm characteristic impedance,
# tolerance +-10 %") and MAX-F10S integration manual 4.4 ("the impedance of
# the RF signal line must be 50 ohm; select the stack-up, copper, and
# dielectric properties of the PCB accordingly").
#
# The stack-up is in the board file, so the width is a calculation and not an
# open question: four copper layers of 35 um in 0.80 mm, which leaves
# (0.80 - 4 x 0.035) / 3 = 0.22 mm of dielectric between F.Cu and the ground
# plane on In1.Cu. What is NOT known is the dielectric constant - it is the
# fabricator's, and 4.3 is the usual value for FR-4 at these frequencies.
# That assumption is the reason the result is printed with its inputs.
ER_FR4 = 4.3                 # ASSUMIDO: confirmar com o fabricante
H_DIEL = MP.DIEL_RF           # F.Cu ao plano de terra, do empilhamento
T_CU = 0.035


def z0_microstrip(w: float, h: float = H_DIEL, er: float = ER_FR4) -> float:
    """Hammerstad's microstrip impedance, in ohm."""
    u = w / h
    ef = (er + 1) / 2 + (er - 1) / 2 * (1 + 12 / u) ** -0.5
    if u <= 1:
        return 60 / math.sqrt(ef) * math.log(8 / u + u / 4)
    return 120 * math.pi / (math.sqrt(ef) * (u + 1.393 + 0.667 * math.log(u + 1.444)))


def largura_para(z_alvo: float) -> float:
    """The width that gives this impedance, by bisection on the formula."""
    lo, hi = 0.05, 3.0
    for _ in range(60):
        meio = (lo + hi) / 2
        # a narrower track has HIGHER impedance, so overshooting the target
        # means the track has to get wider, not narrower
        if z0_microstrip(meio) > z_alvo:
            lo = meio
        else:
            hi = meio
    return round((lo + hi) / 2, 3)


LARGURA_RF = largura_para(50.0)
# A coplanar waveguide with its ground far enough away behaves as a plain
# microstrip; the datasheets ask for CPWG, so the pour stays beside the line
# with a gap of at least three widths, and the ground vias go along both
# sides. Closer than that and this number would have to be recomputed with
# the coplanar formula.
FOLGA_CPWG = 3.0 * LARGURA_RF
# The USB pair is 90 ohm DIFFERENTIAL, and that is not two 45 ohm lines: a
# 0.2 mm gap over 0.22 mm of dielectric couples them, and coupling lowers the
# differential impedance. The usual closed form for an edge-coupled
# microstrip is used here,
#
#     Zdiff = 2 x Z0 x (1 - 0.48 x exp(-0.96 x S/H))
#
# which is an approximation: the real number comes from the fabricator's
# field solver together with the real dielectric constant. Both assumptions
# are printed by the dry-run so that neither hides.
PASSO_PAR = 0.2              # gap between the two tracks of the pair


def z_diferencial(w: float, s: float = PASSO_PAR) -> float:
    return 2 * z0_microstrip(w) * (1 - 0.48 * math.exp(-0.96 * s / H_DIEL))


def largura_par(z_alvo: float = 90.0) -> float:
    lo, hi = 0.05, 3.0
    for _ in range(60):
        meio = (lo + hi) / 2
        if z_diferencial(meio) > z_alvo:
            lo = meio
        else:
            hi = meio
    return round((lo + hi) / 2, 3)


LARGURA_USB_CALC = largura_par(90.0)


def largura(rede: str) -> float:
    if rede in NAO_ROTEAR:
        return LARGURA_RF
    if rede.startswith("USB_D"):
        # A largura que da 90 ohm diferenciais NESTA pilha, calculada logo
        # acima: 0,207 mm com 0,2 de afastamento. Ela cabe.
        #
        # Este comentario dizia 0,352 mm, e isso ficou aqui desde
        # 2026-09-24 sem nunca ter sido conta: 0,352 e a largura de 90 ohm
        # na pilha UNIFORME de 0,22 mm por vao, que foi abandonada no mesmo
        # commit que criou este calculo. Com os 0,10 mm de prepreg que a
        # placa tem, a mesma formula da 0,207. O numero errado sustentava um
        # argumento inteiro - "0,352 nao sai do campo de ilhas de 0,5 mm de
        # passo, entao o par e roteado mais fino e a diferenca e reportada" -
        # que simplesmente nao existe: 0,207 sai.
        return LARGURA_USB_CALC
    if e_alimentacao(rede):
        return LARGURA_ALIM
    return LARGURA


def folga_de(rede: str) -> float:
    return FOLGA_USB if rede.startswith("USB_D") else FOLGA


def extra_de(rede: str) -> float:
    """How much further than the marked halo this net has to look.

    The grid carries the narrowest track at the smallest clearance. A net
    that is wider, or that belongs to a class with more clearance, makes up
    the difference here, at the moment it looks - which costs a small disc
    per cell instead of shutting every fine-pitch escape route.
    """
    return max(0.0, (folga_de(rede) - FOLGA) + (largura(rede) - LARGURA) / 2)


def _disco_off(raio: float) -> tuple[tuple[int, int], ...]:
    """The cells a net of this net's width has to look at, beyond its own.

    A full grid step of slack, not none. The marked cells are a discrete
    set: the nearest one to a given cell can be up to a step further away
    than the true nearest point of the obstacle, and asking only about cells
    whose CENTRE is within the radius then misses it. That gap is what let a
    0.4 mm power track sit 0.110 mm from a pad that wanted 0.127.
    """
    if raio <= 1e-9:
        # nothing to make up: a cell that is not marked is already far
        # enough, because that is exactly what the marking means
        return ((0, 0),)
    lim = raio + PASSO
    n = int(math.ceil(lim / PASSO))
    return tuple((dx, dy)
                 for dx in range(-n, n + 1) for dy in range(-n, n + 1)
                 if math.hypot(dx * PASSO, dy * PASSO) <= lim + 1e-9)


class Grade:
    """Where a track may run, and where the centre of a via may land.

    Two maps, because the two things have different sizes. `t` answers "may
    a track of this net occupy this cell"; `v` answers "may a via of this
    net be centred on this cell". Both are keyed by (layer, ix, iy); the via
    map is checked on both layers, since a via goes through.
    """

    def __init__(self) -> None:
        self.nx = int(M.W / PASSO) + 1
        self.ny = int(M.H / PASSO) + 1
        self.t: dict[tuple[int, int, int], str] = {}
        self.v: dict[tuple[int, int, int], str] = {}
        self.fixo: set[tuple[int, int, int]] = set()   # a pad's own copper
        self.postas: set[tuple[int, int]] = set()      # via centres already used

    def cel(self, x: float, y: float) -> tuple[int, int]:
        return (int(round(x / PASSO)), int(round(y / PASSO)))

    def pos(self, ix: int, iy: int) -> tuple[float, float]:
        return (ix * PASSO, iy * PASSO)

    def dentro(self, ix: int, iy: int) -> bool:
        """Can a track or a via CENTRE sit here?

        The margin is not BORDA_COBRE. BORDA_COBRE is what the DRC asks
        between COPPER and the board outline, and what sits on a grid point
        is a centre line: a via of 0,45 mm centred 0,3 mm from the edge
        leaves copper at 0,075, and the DRC says so. The router also drops a
        via wherever it changes layer, so every grid point has to hold the
        widest thing that can land on it, which is the via and not the
        track. That costs 0,225 mm of routable area all round, and it is the
        difference between a board that passes the DRC and one that does
        not - two errors of exactly this kind, a GND track at 0,100 mm and a
        stitching via at 0,075 mm, are what put this comment here.
        """
        x, y = self.pos(ix, iy)
        if x < MARGEM_BORDA or y < MARGEM_BORDA or \
                x > M.W - MARGEM_BORDA or y > M.H - MARGEM_BORDA:
            return False
        # the notch under the module's antenna is not board: copper there is
        # copper hanging in the air, and the DRC calls it what it is
        for nome, (rx0, ry0, rx1, ry1), _c, _s in M.ZONES:
            if nome != "RECORTE_ANTENA_MODULO":
                continue
            if rx0 - MARGEM_BORDA < x < rx1 + MARGEM_BORDA and \
                    ry0 - MARGEM_BORDA < y < ry1 + MARGEM_BORDA:
                return False
        r = M.RADIUS_DRAWING
        for cx, cy in ((r, r), (M.W - r, r), (r, M.H - r), (M.W - r, M.H - r)):
            fora_x = x < r if cx < M.W / 2 else x > M.W - r
            fora_y = y < r if cy < M.H / 2 else y > M.H - r
            if fora_x and fora_y and math.hypot(x - cx, y - cy) > r - MARGEM_BORDA:
                return False
        return True

    # -- marking ----------------------------------------------------------
    def _por(self, mapa: dict, k, rede: str,
             respeitar_fixo: bool = True) -> None:
        """Claim one cell for a net's clearance, and refuse to lie about it.

        A cell can fall inside the clearance of TWO different nets. Marking
        it with setdefault - which is what this did - makes it remember only
        the first, and then a track of that first net may legally run through
        it although it is 0.025 mm from the second net's pad. That was 42 of
        the board's clearance errors, and the same mistake in the via map was
        another 47.

        A cell wanted by two nets belongs to neither: nobody may put copper
        there, because whoever does is too close to the other one. Copper
        that is already a pad of some net is the exception, in `fixo`: it is
        real metal, its own net has to be able to reach it, and two pads too
        close together is a placement problem that the DRC reports on its own.
        """
        if respeitar_fixo and k in self.fixo:
            return
        d = mapa.get(k)
        if d is None:
            mapa[k] = rede
        elif d != rede:
            mapa[k] = BLOQUEADO

    def _ret(self, mapa: dict, camada: int, x: float, y: float,
             hw: float, hh: float, rede: str,
             respeitar_fixo: bool = True) -> None:
        """Reserve the cells of an axis-aligned rectangle, inflated already.

        A cell is a place a track CENTRE may sit, and the rectangle is
        already inflated by the clearance plus half a track. So the cells to
        reserve are exactly those whose centre falls inside it: a centre
        0.075 mm outside the boundary is 0.075 mm MORE than the clearance
        away from the copper, and it is legal.

        This used floor and ceil on the corners, reserving every cell the
        rectangle so much as touched - up to a full step, 0.15 mm, beyond
        the boundary on each side. A 0.365 mm ring became a 0.5 mm one, and
        at 0.5 mm of pad pitch the rings of two neighbouring pads met ON TOP
        of every pad, where two nets' rings make a cell blocked for all.
        Nothing could leave a fine-pitch row: not the USB pair from the
        receptacle, not CC1 from the ESD diode, not the module's pins from
        the top. The DRC, which measures real copper, never saw a problem,
        because there was none: the only thing too close was the model.
        """
        eps = 1e-6
        ix0 = int(math.floor((x - hw) / PASSO + eps)) + 1
        iy0 = int(math.floor((y - hh) / PASSO + eps)) + 1
        ix1 = int(math.ceil((x + hw) / PASSO - eps)) - 1
        iy1 = int(math.ceil((y + hh) / PASSO - eps)) - 1
        for ix in range(ix0, ix1 + 1):
            for iy in range(iy0, iy1 + 1):
                self._por(mapa, (camada, ix, iy), rede, respeitar_fixo)

    def _disco(self, mapa: dict, camada: int, x: float, y: float,
               raio: float, rede: str, respeitar_fixo: bool = True) -> None:
        n = int(math.ceil(raio / PASSO))
        cx, cy = self.cel(x, y)
        for dx in range(-n, n + 1):
            for dy in range(-n, n + 1):
                if math.hypot(dx * PASSO, dy * PASSO) > raio + 1e-9:
                    continue
                self._por(mapa, (camada, cx + dx, cy + dy), rede,
                          respeitar_fixo)

    def cobre(self, camadas, x: float, y: float, hw: float, hh: float,
              rede: str) -> None:
        """A pad's own copper: real metal, and its net has to reach it."""
        for c in camadas:
            ix0, iy0 = self.cel(x - hw, y - hh)
            ix1, iy1 = self.cel(x + hw, y + hh)
            for ix in range(ix0, ix1 + 1):
                for iy in range(iy0, iy1 + 1):
                    k = (c, ix, iy)
                    self.t[k] = rede
                    self.fixo.add(k)

    def pad(self, camadas, x: float, y: float, hw: float, hh: float,
            rede: str, folga: float = FOLGA) -> None:
        """A pad, as the rectangle it is, into both maps.

        A track has to keep FOLGA from the copper, so its centre line has to
        keep FOLGA + half a track. A via has to keep FOLGA from the copper
        with its 0.45 mm pad, AND 0.2 mm from the copper with its 0.25 mm
        hole; the first is the larger, so it decides.
        """
        for c in camadas:
            self._ret(self.t, c, x, y, hw + folga + LARGURA / 2,
                      hh + folga + LARGURA / 2, rede)
        # a via goes through: a pad on any layer blocks it on all of them
        # respeitar_fixo=False on purpose. In the track map that exemption
        # is what lets a net reach its own pad; in the VIA map there is no
        # such thing to protect, and keeping it there let a ground stub drop
        # a via 0.075 mm from a neighbouring pad - eleven of the board's
        # nineteen clearance errors.
        for c in range(NC):
            self._ret(self.v, c, x, y, hw + FOLGA_MASCARA + VIA_D / 2,
                      hh + FOLGA_MASCARA + VIA_D / 2, rede,
                      respeitar_fixo=False)

    def trilha(self, camada: int, p0, p1, larg: float, rede: str,
               folga: float = FOLGA) -> None:
        """Reserve a run of track on both maps, along its whole length.
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
